skiselev/mb386sx-rc2016/KiCad/AT386SX-Schematic-1.1.pdf

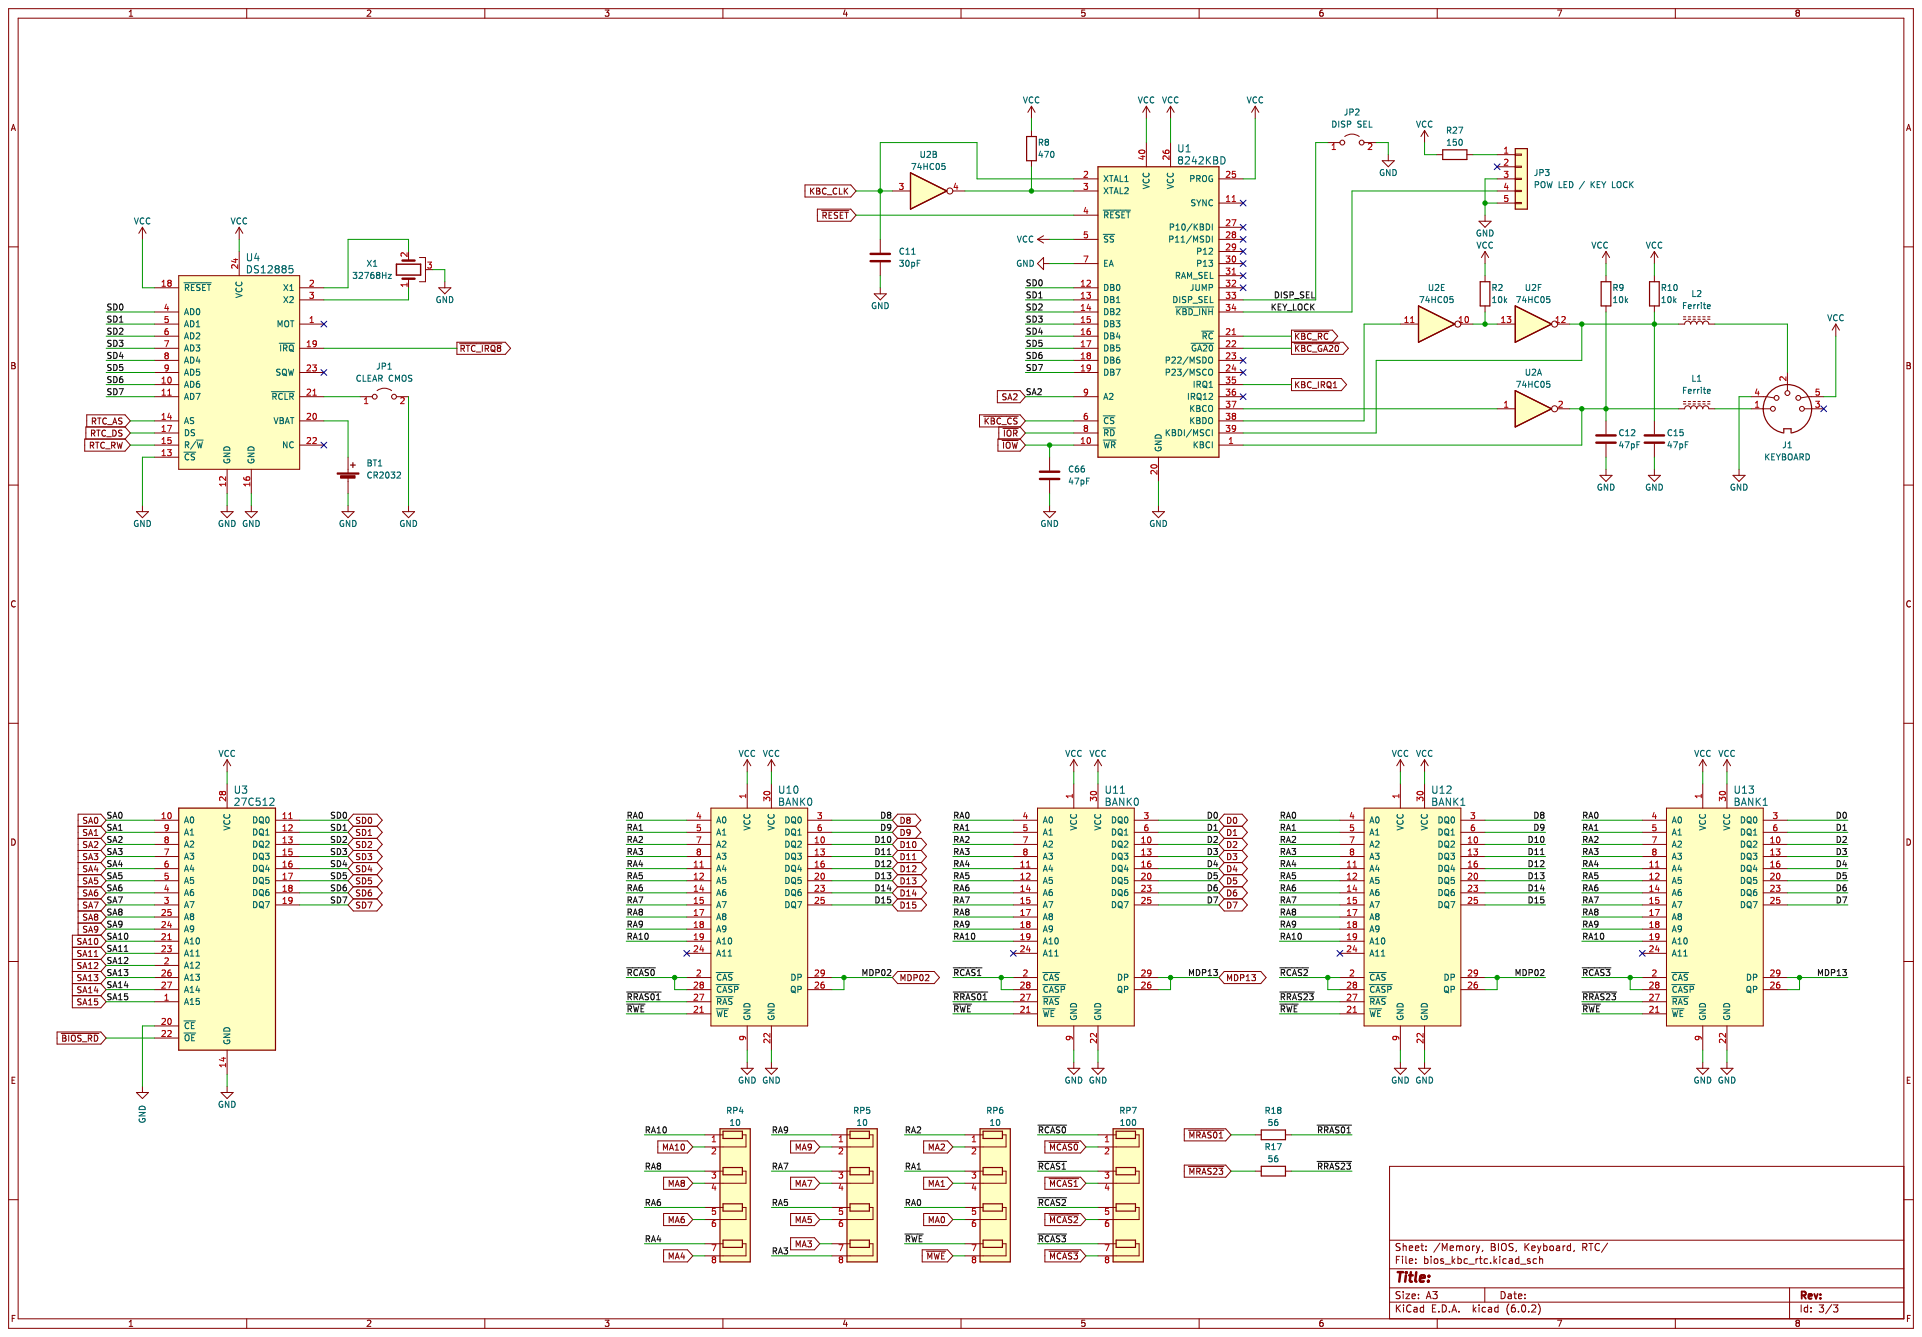
[picture p44: page 3]
