skiselev/mb386sx-rc2016/KiCad/AT386SX-Schematic-1.0.pdf

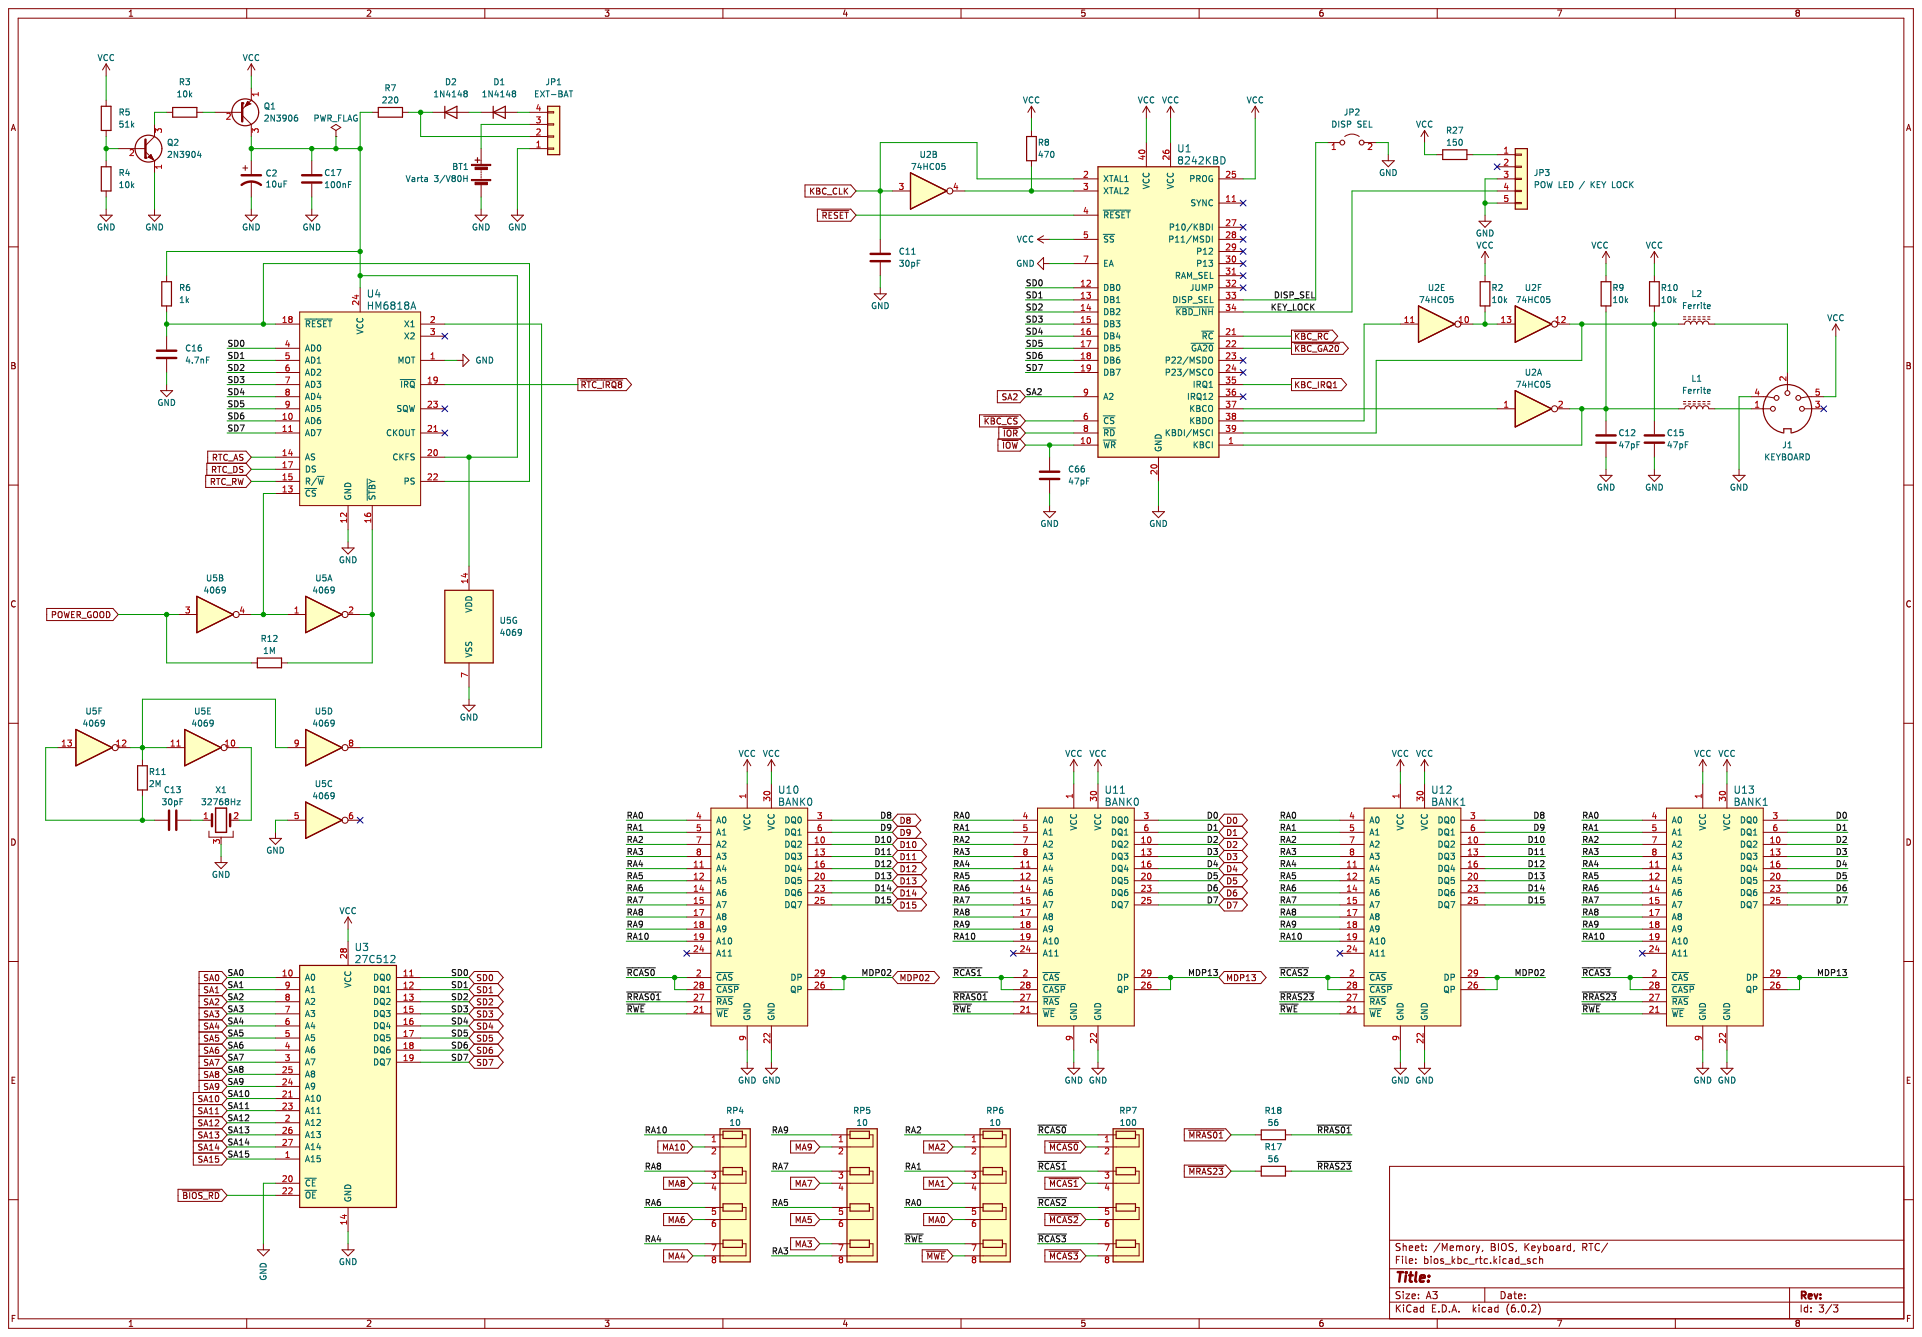
[picture p45: page 3]
