skiselev/mb386sx-rc2016/KiCad/AT386SX-Board-2.3.pdf

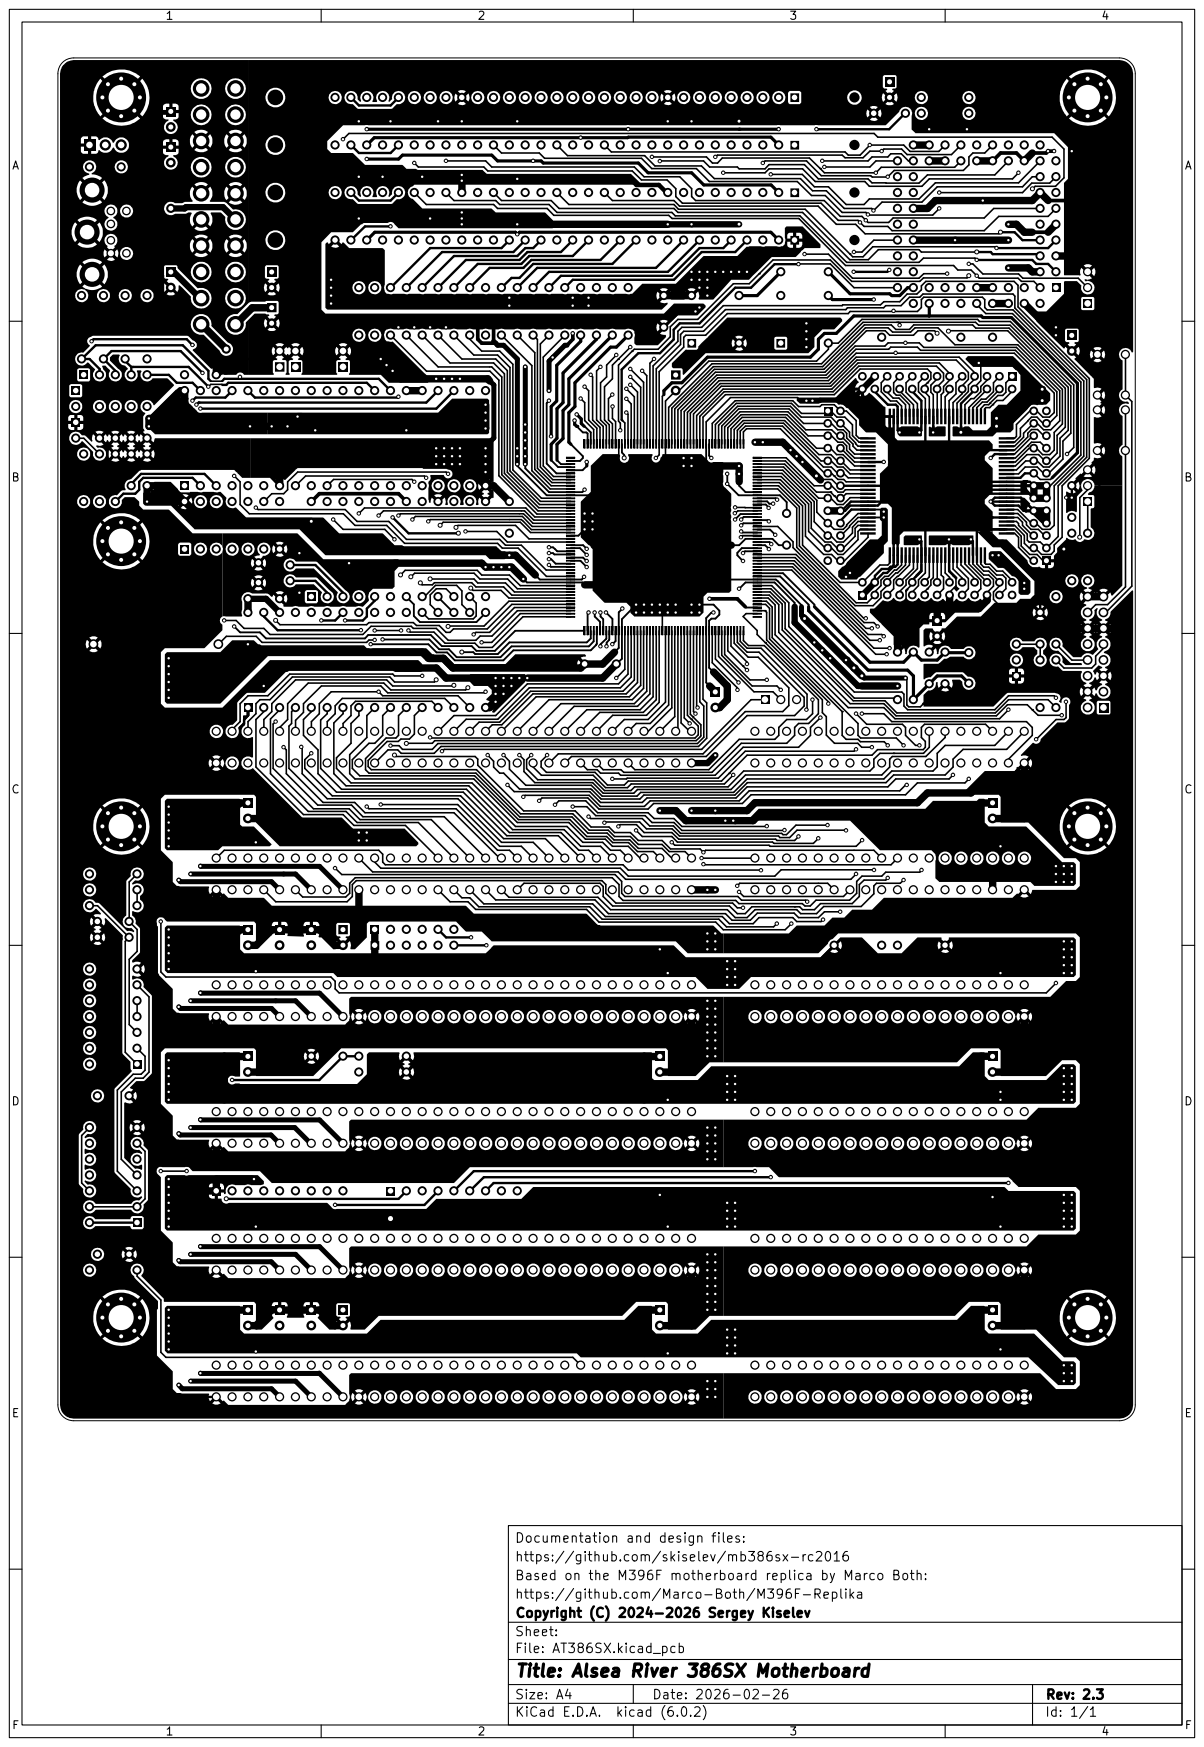
[picture p46: page 1]

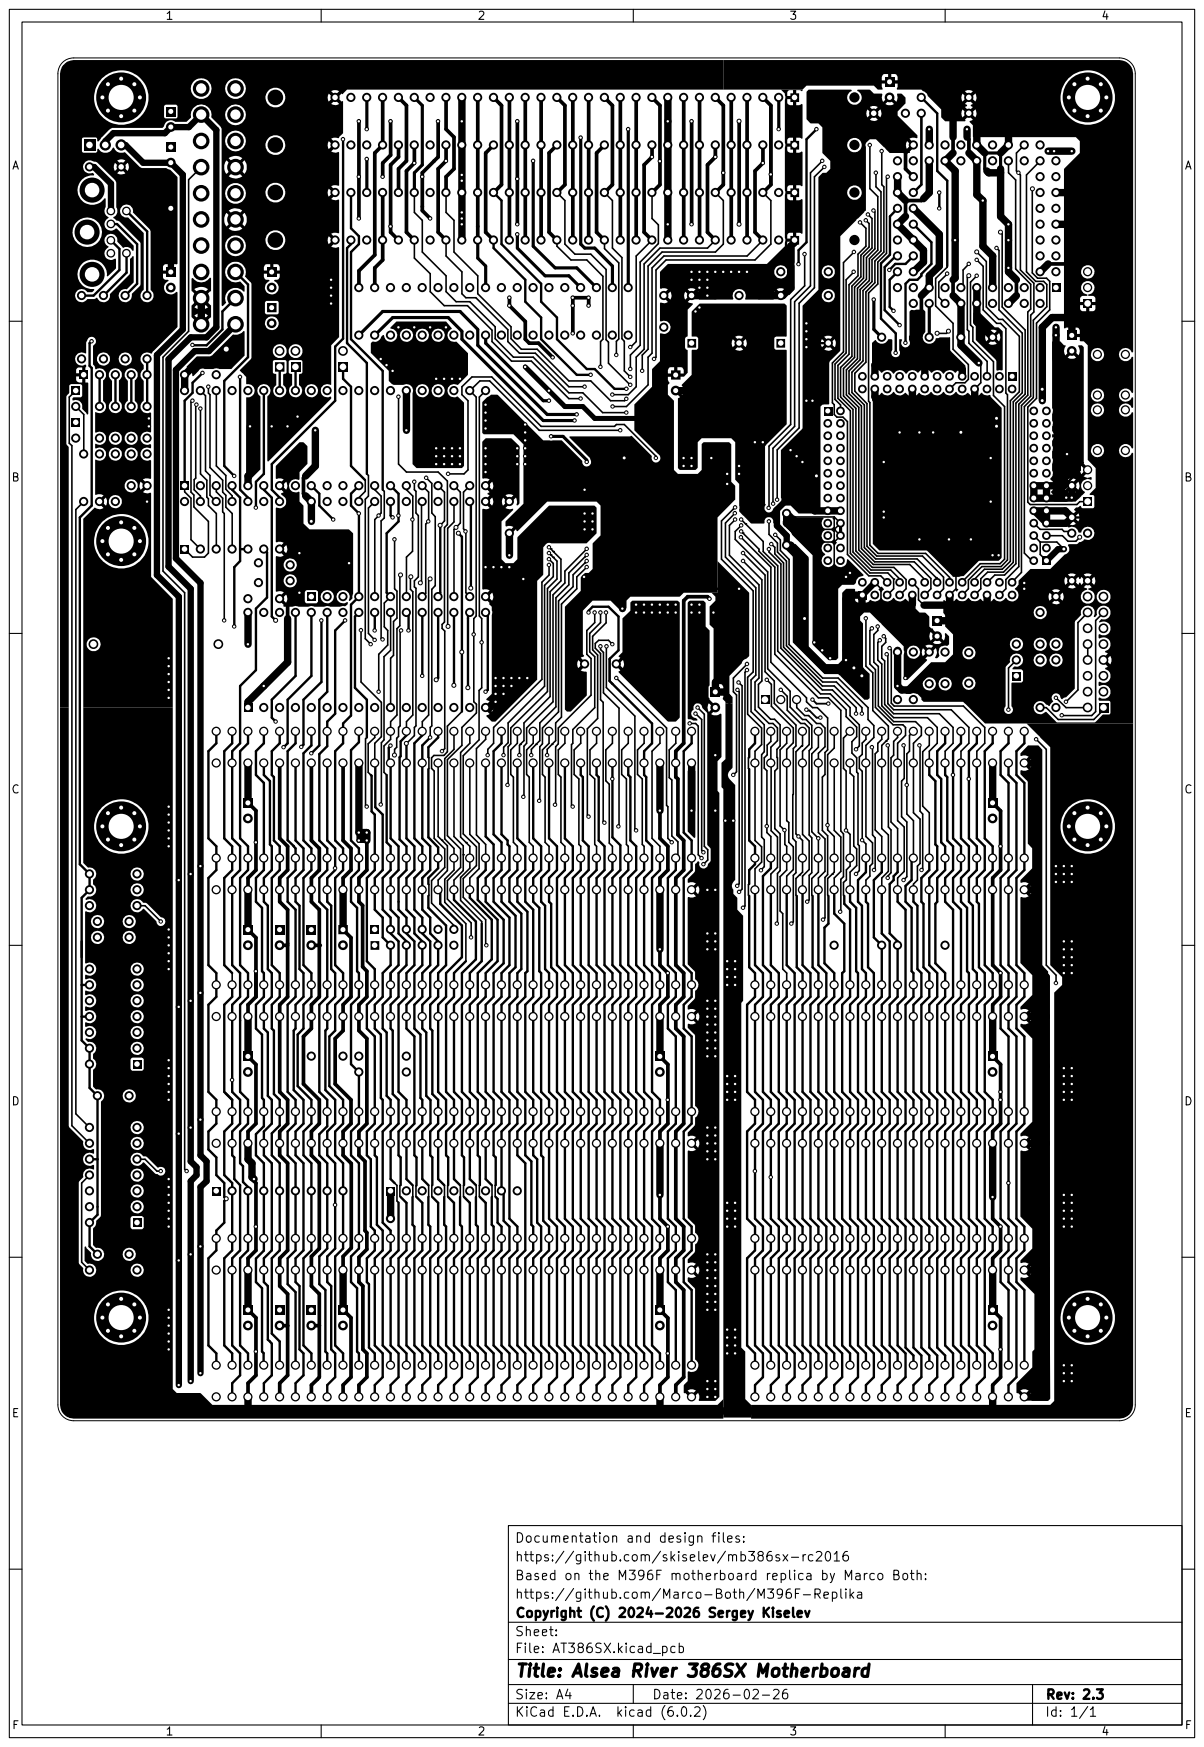
[picture p47: page 2]

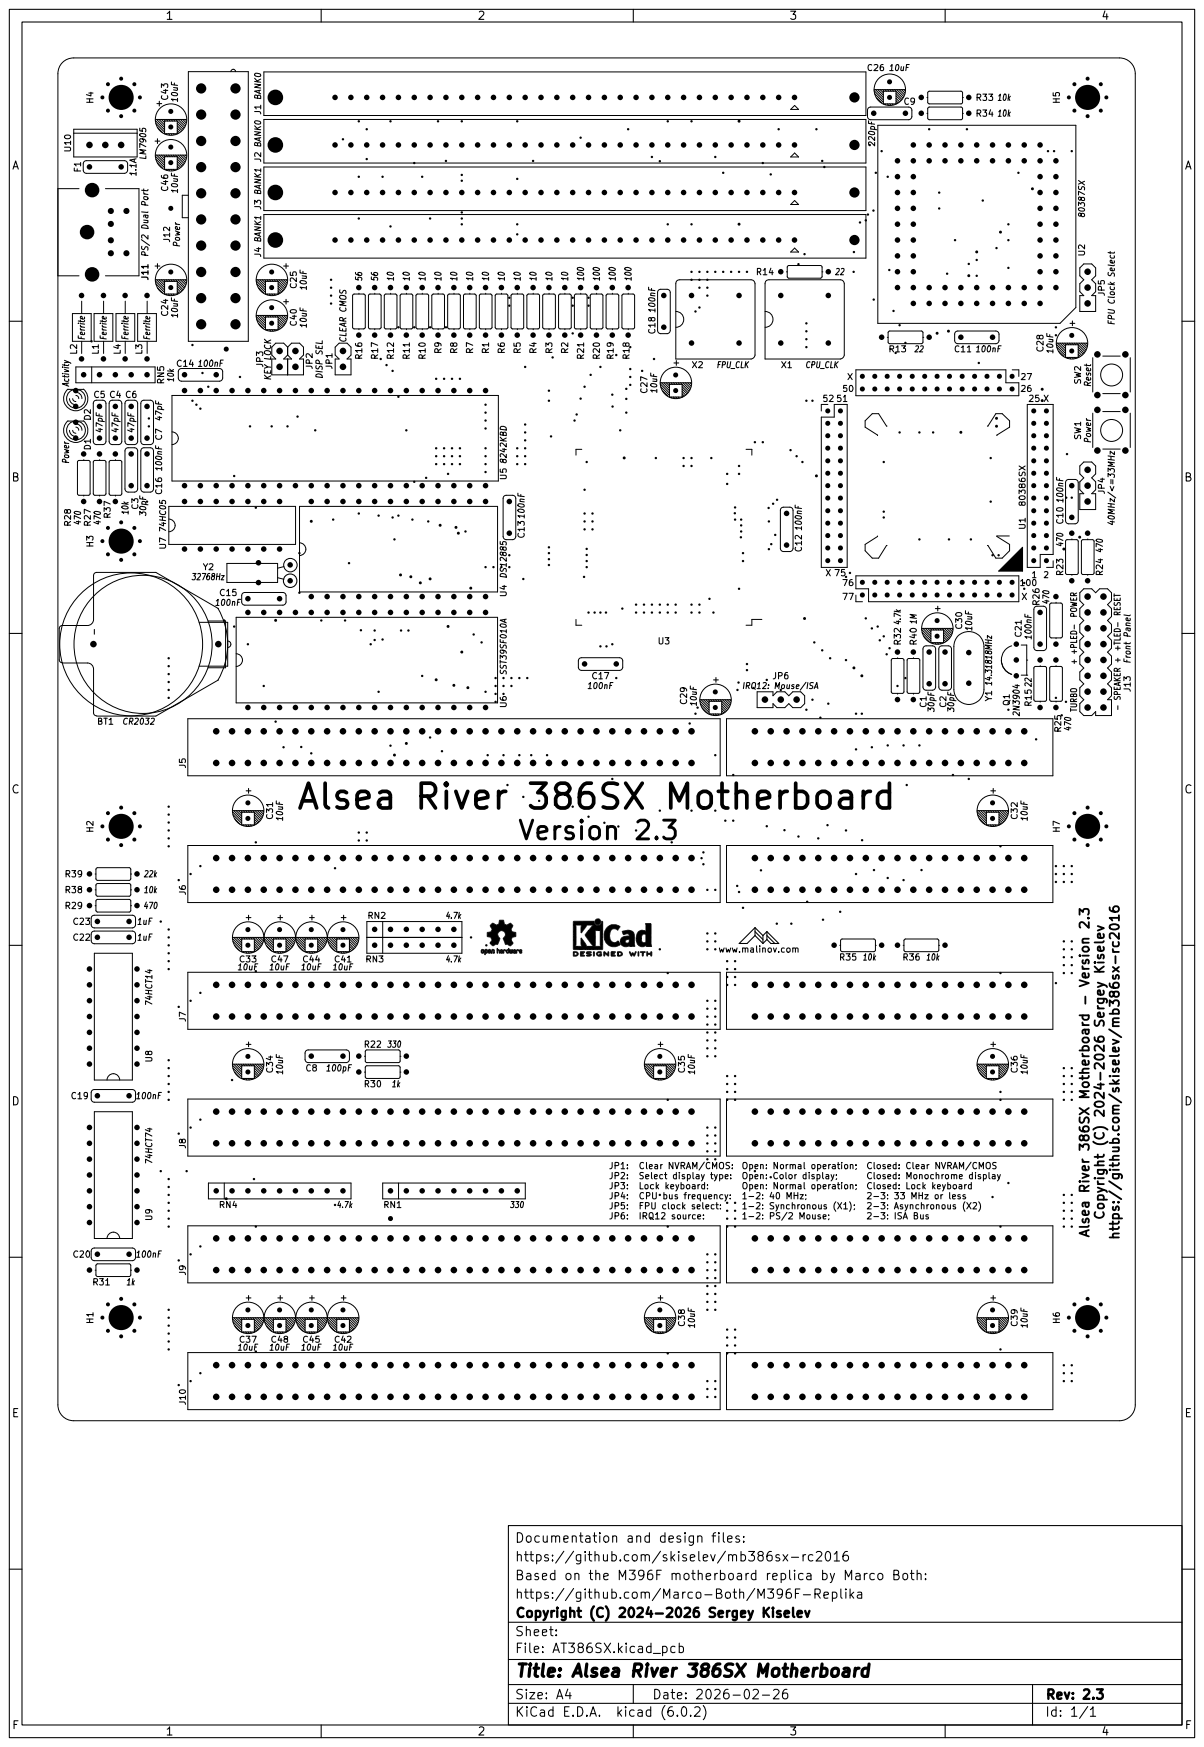
[picture p48: page 3]

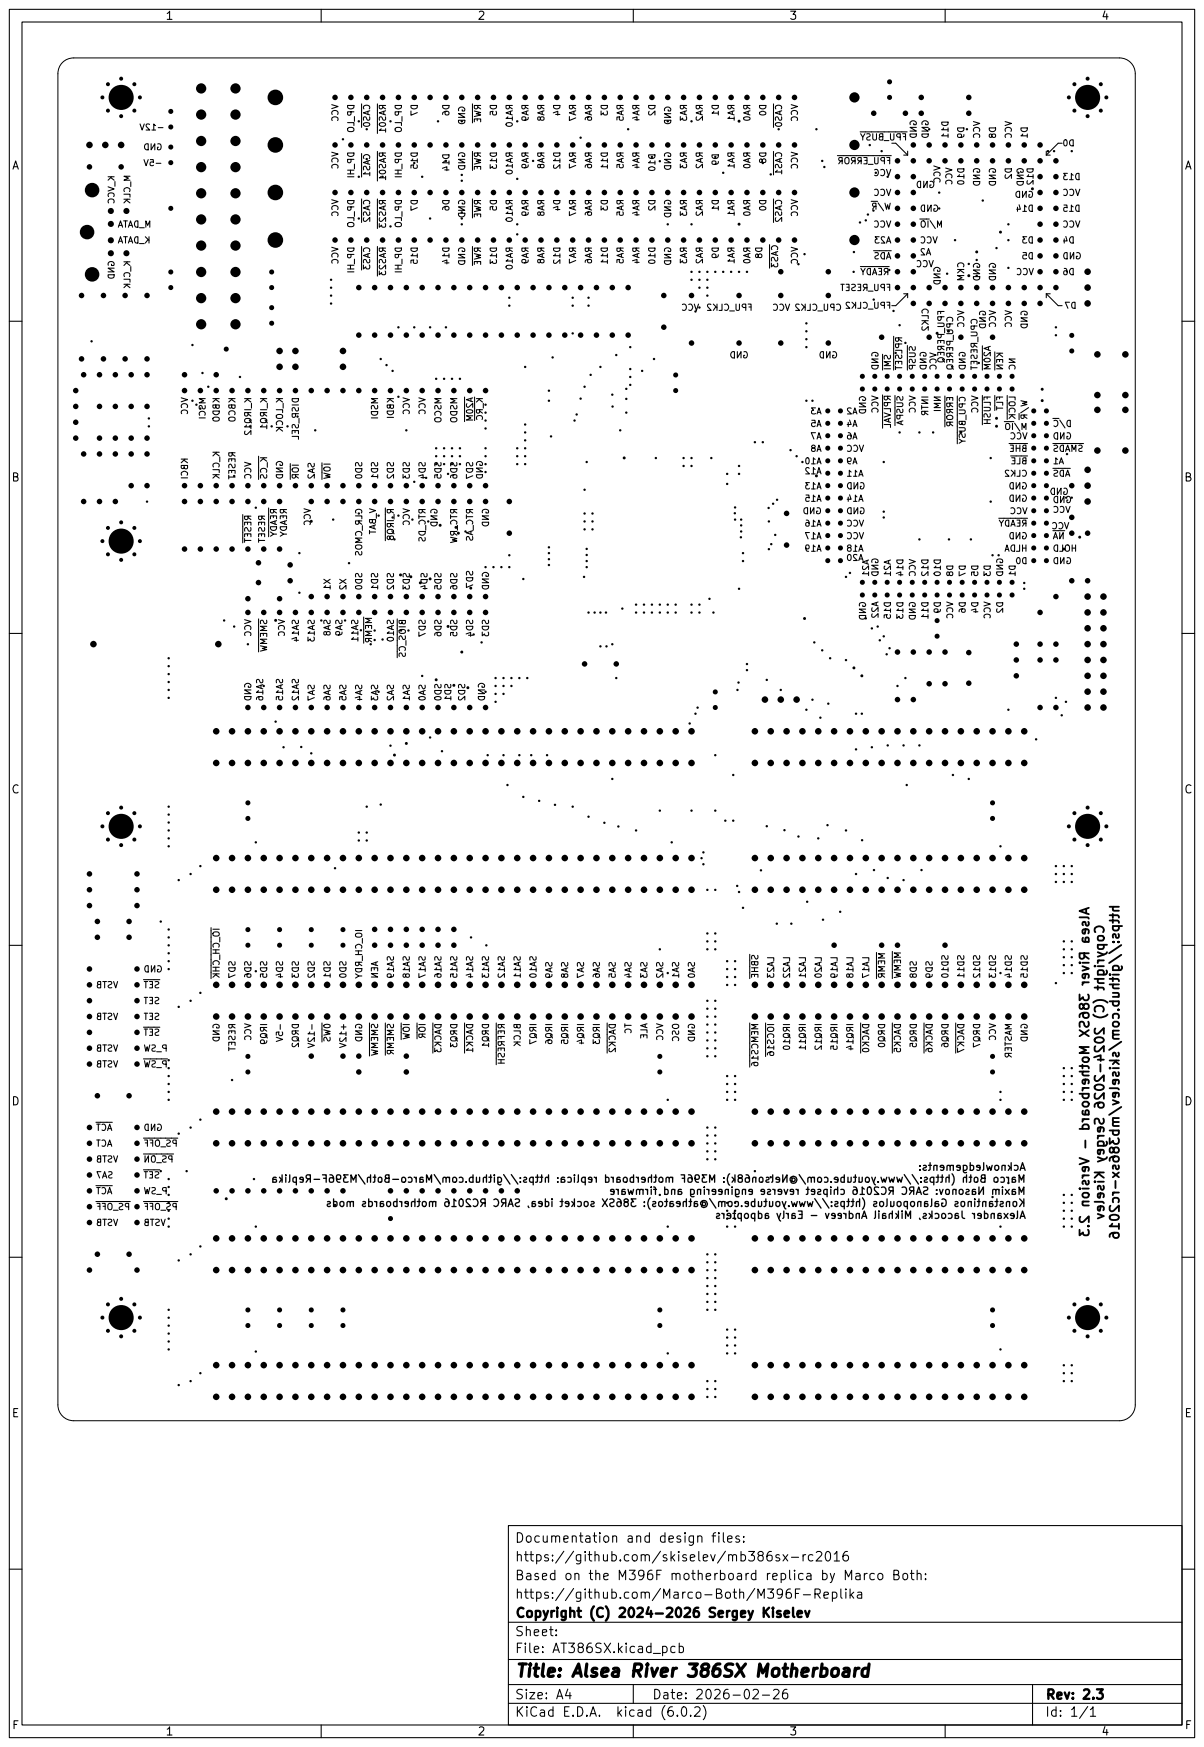
[picture p49: page 4]
