skiselev/mb386sx-rc2016/KiCad/AT386SX-Board-2.2.pdf

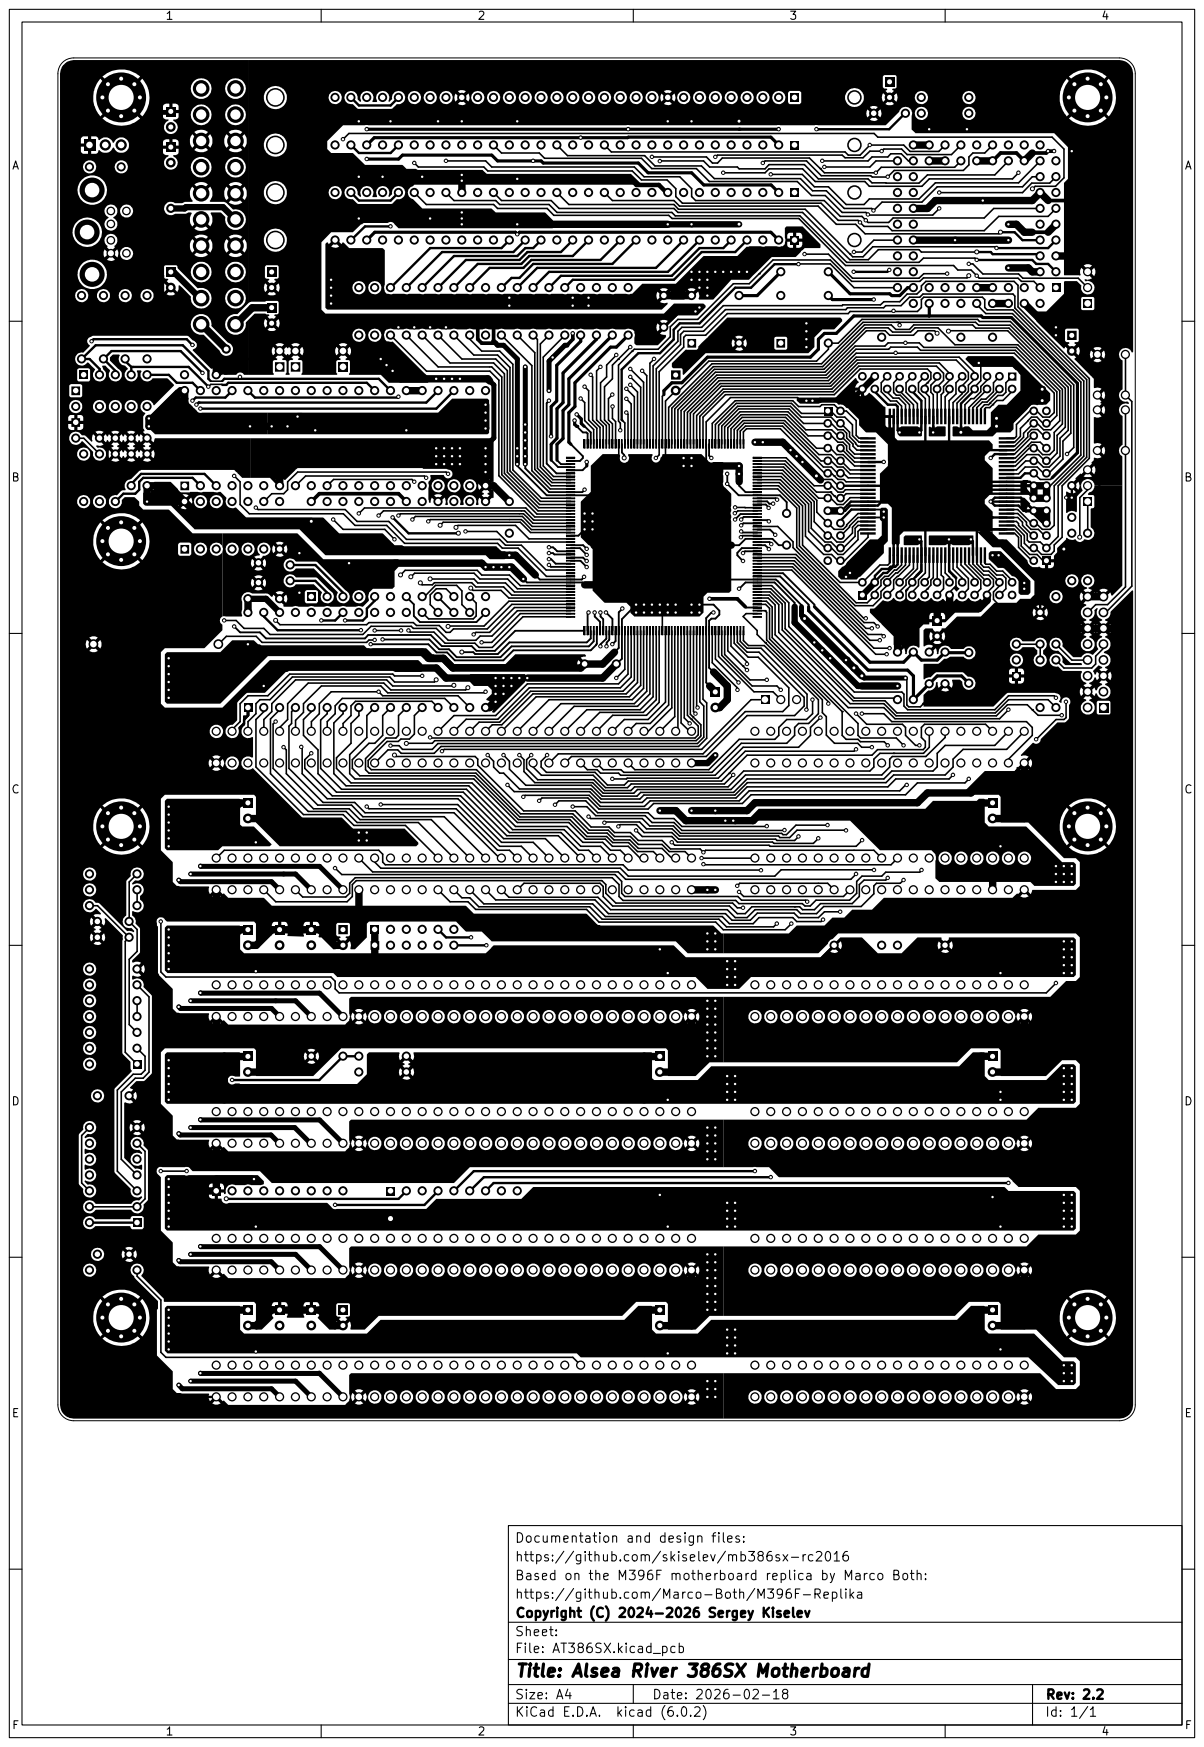
[picture p50: page 1]

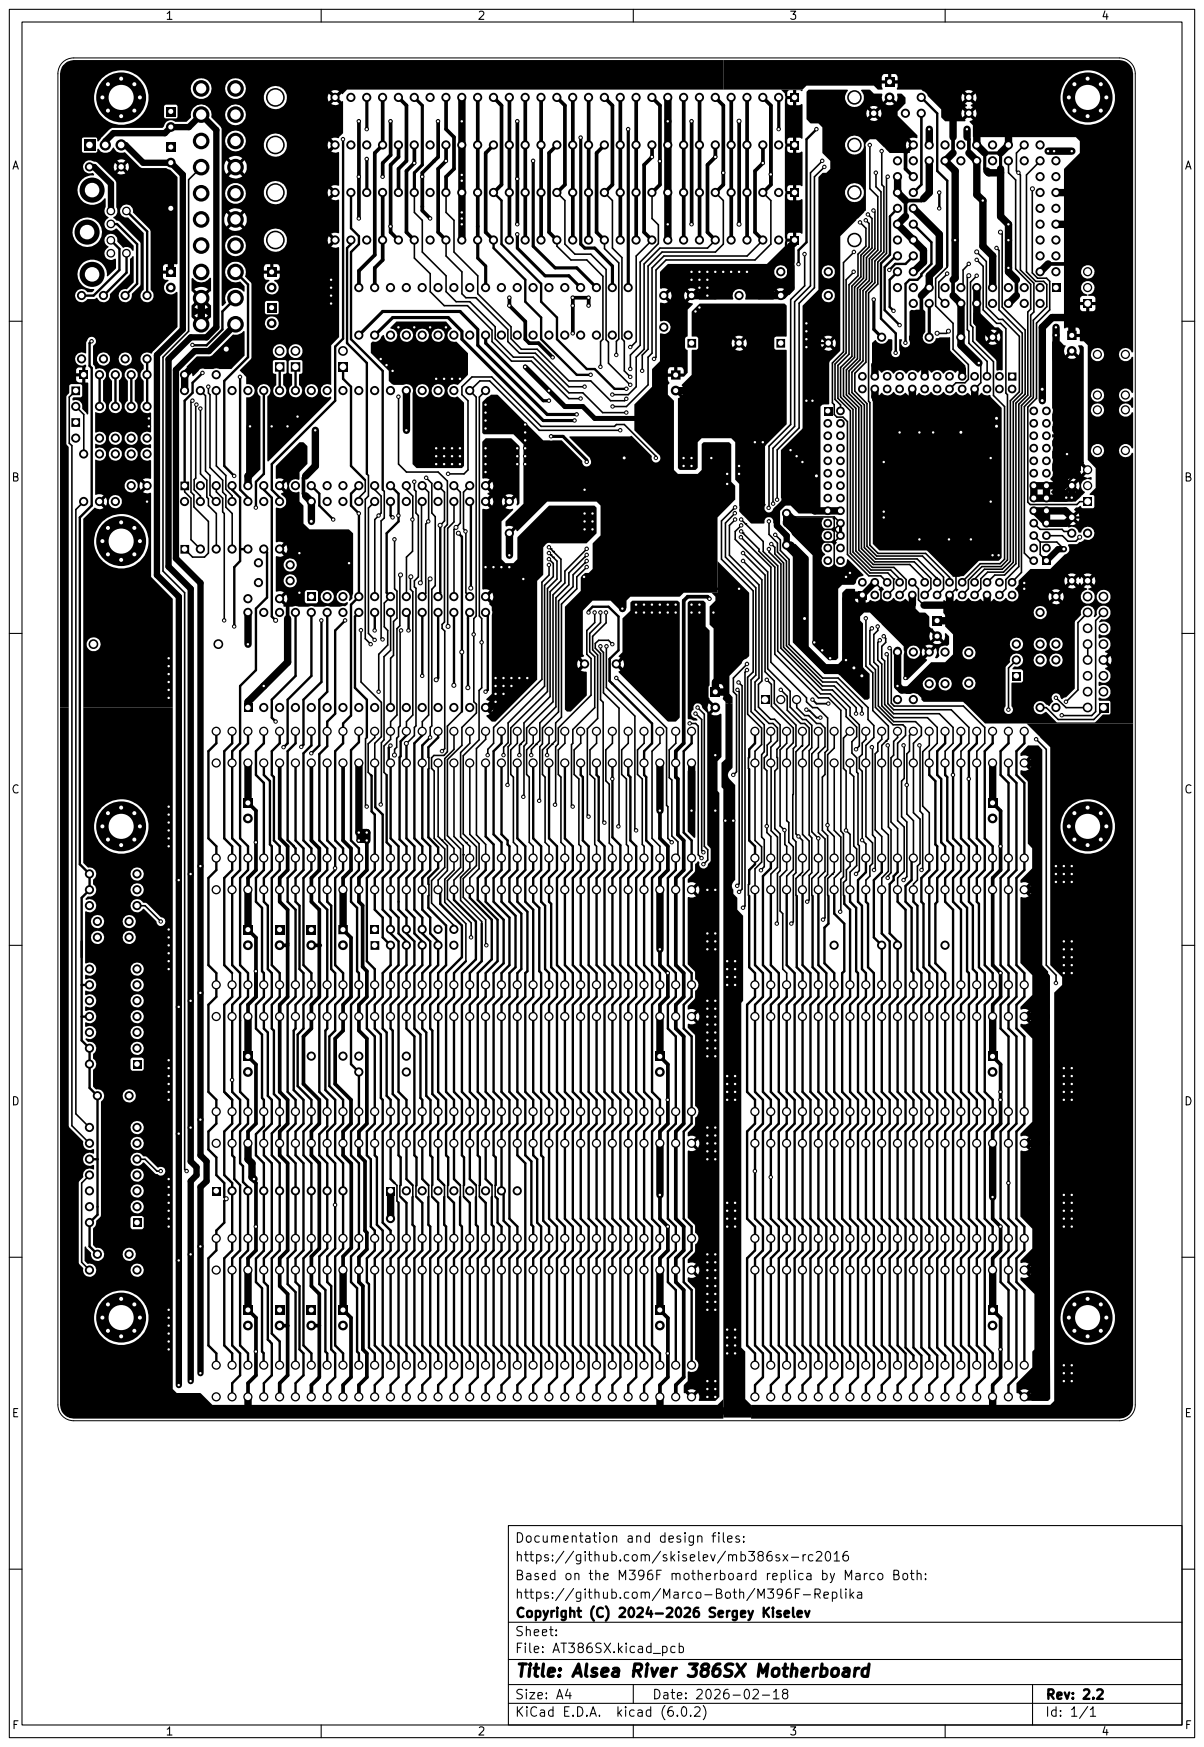
[picture p51: page 2]

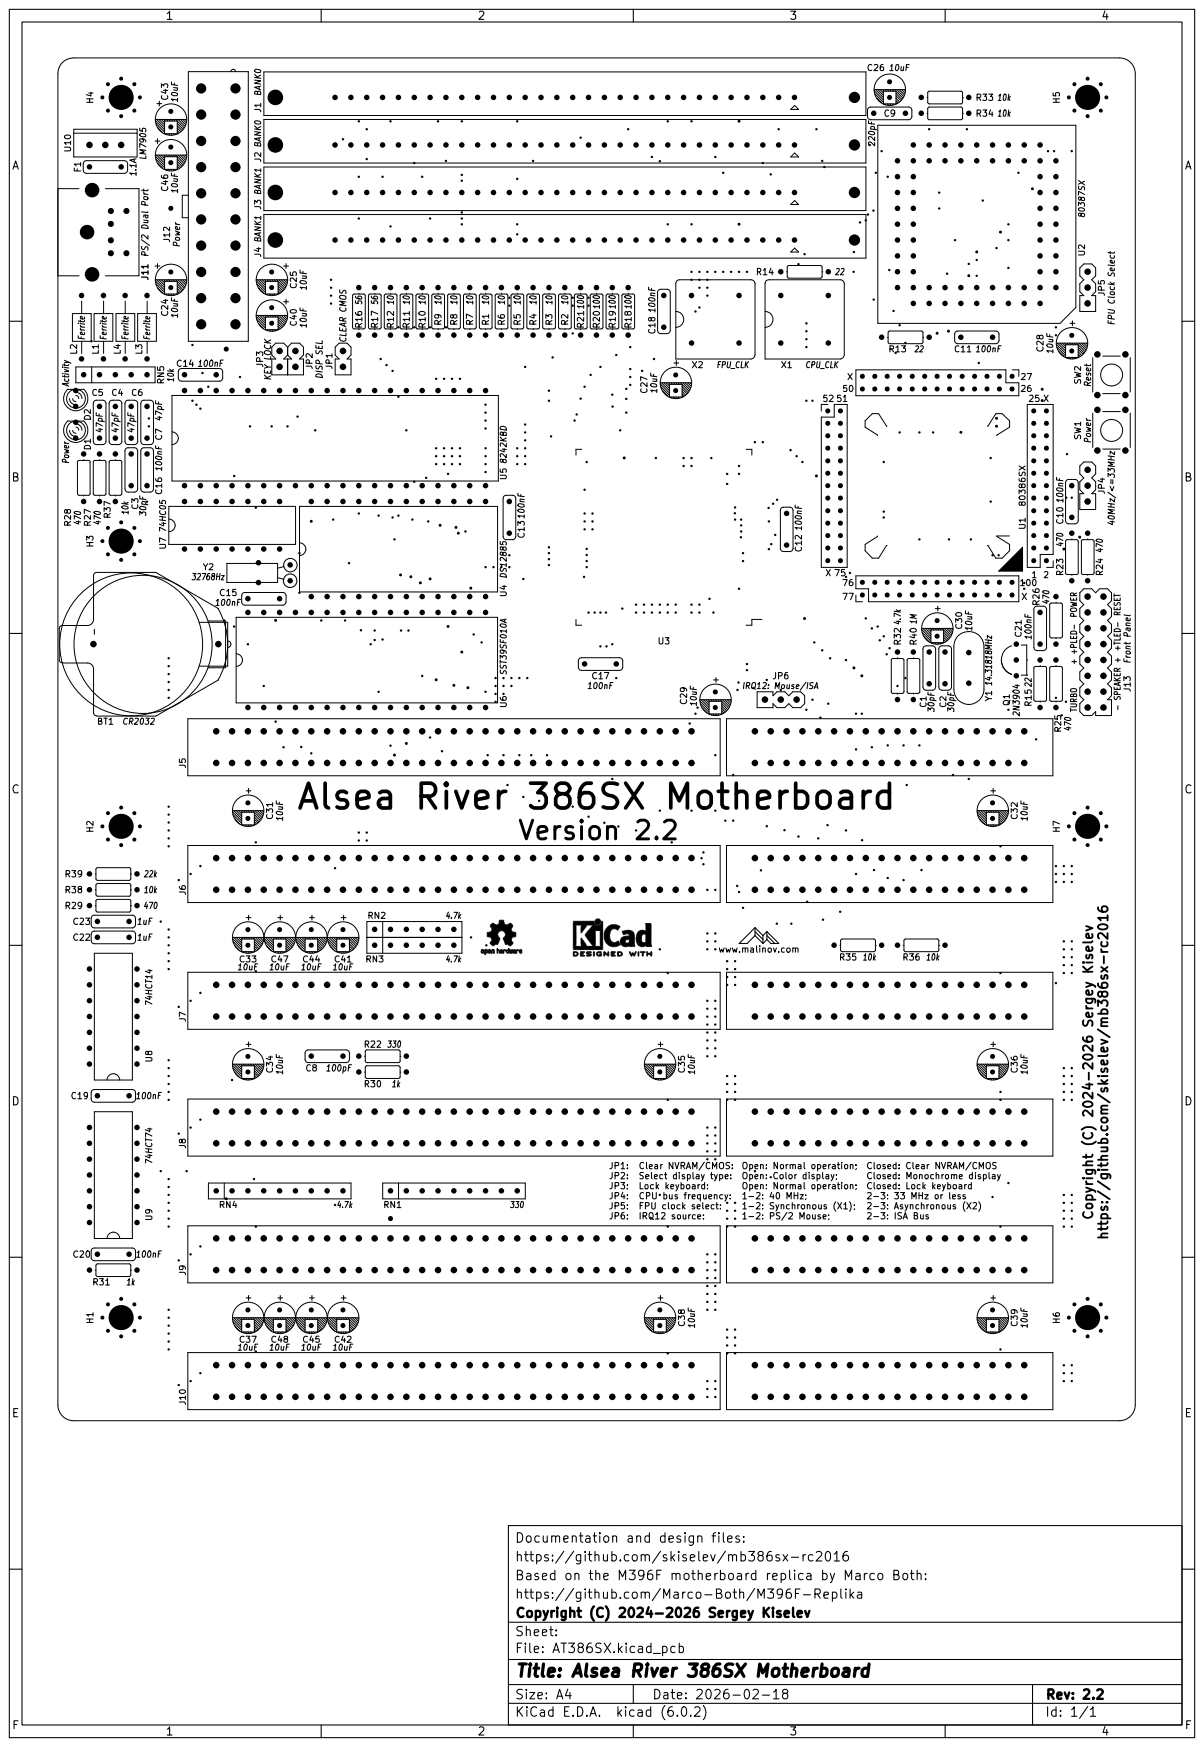
[picture p52: page 3]

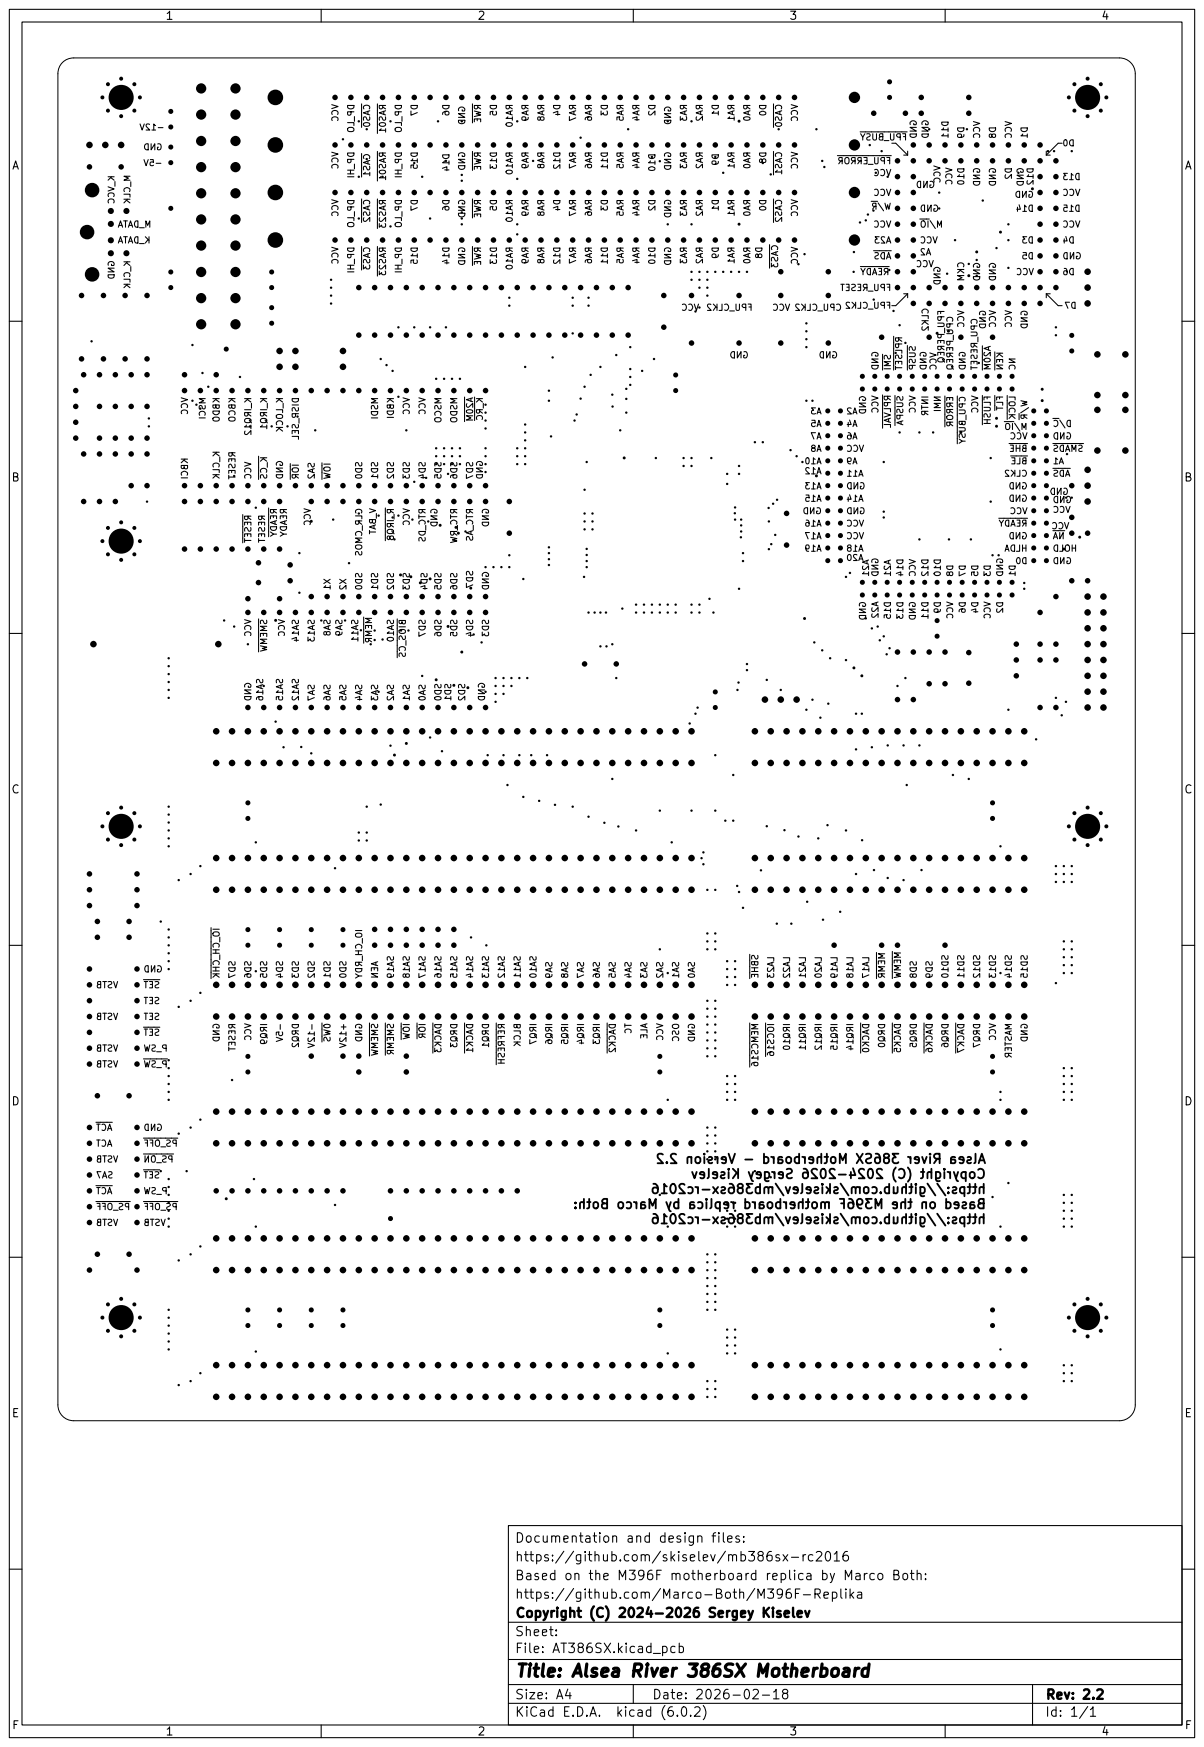
[picture p53: page 4]
