skiselev/mb386sx-rc2016/KiCad/AT386SX-Board-2.1.pdf

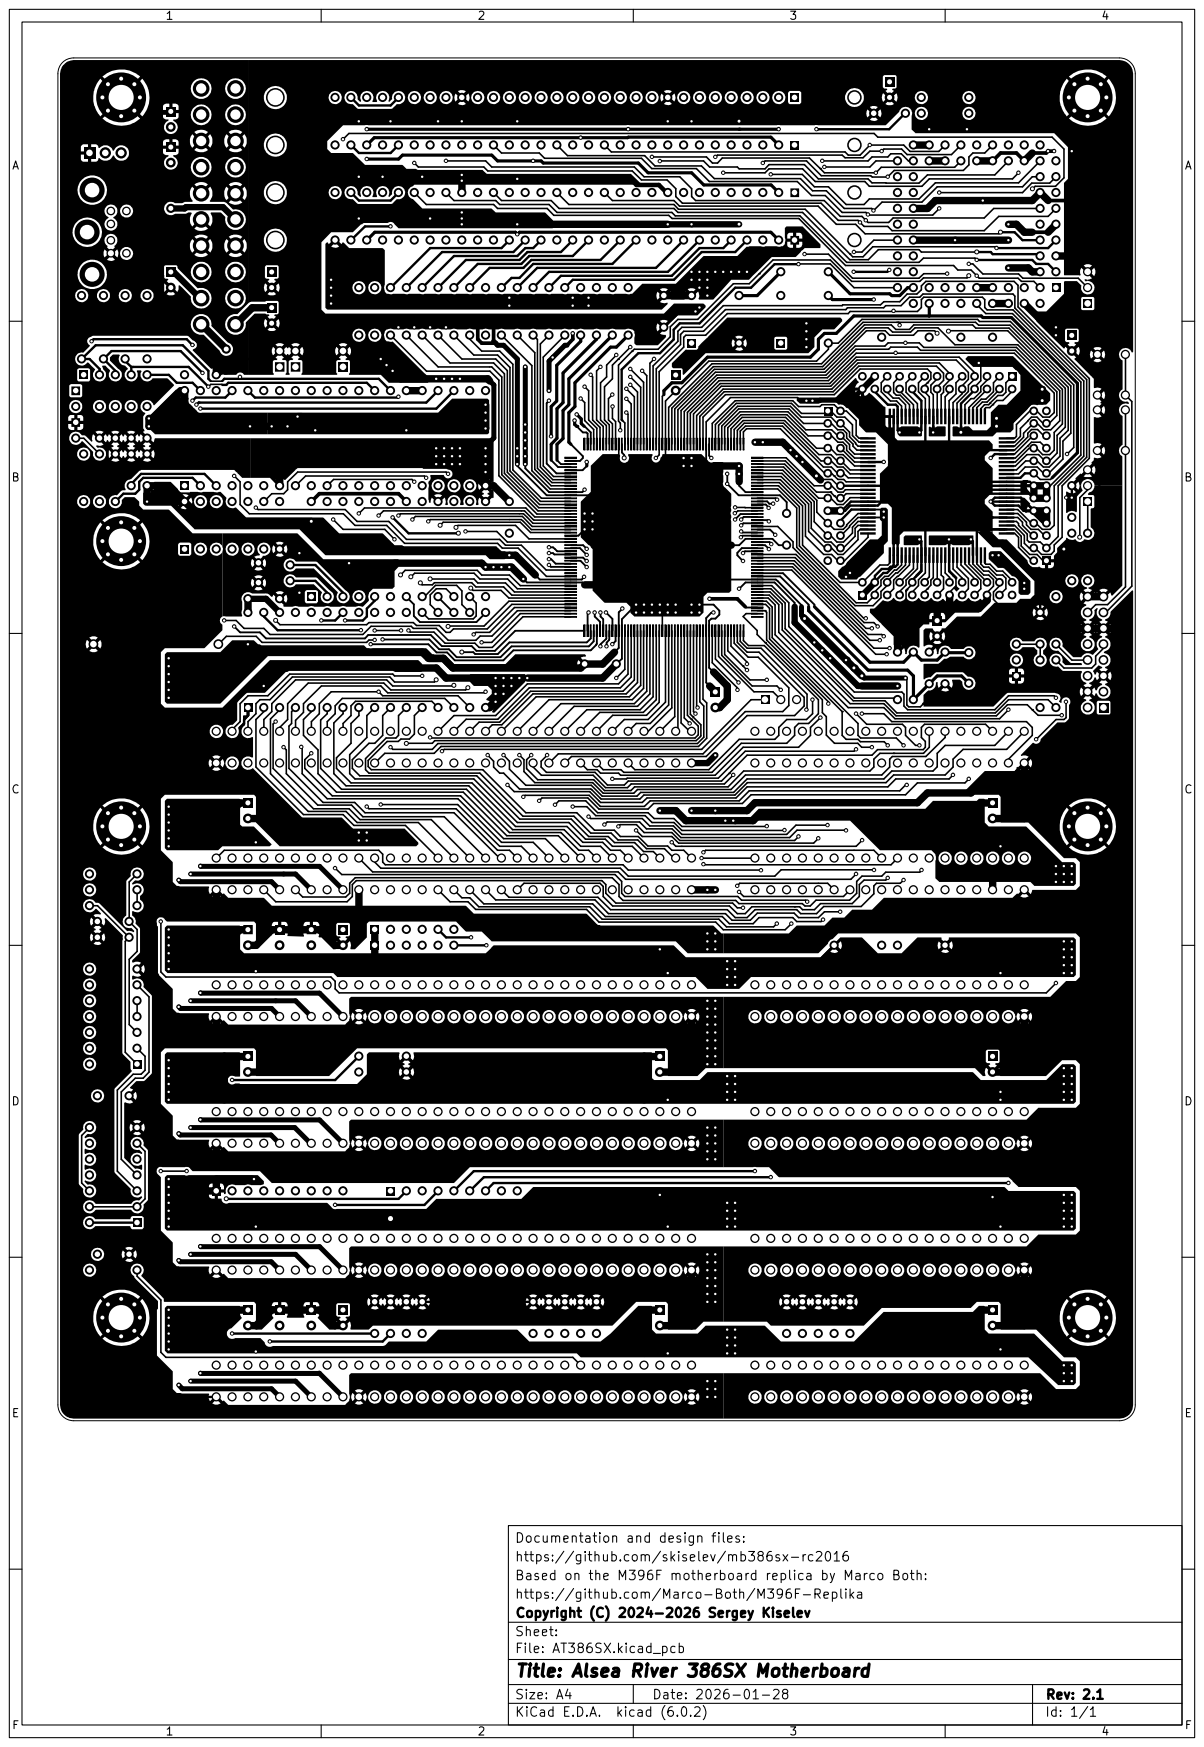
[picture p54: page 1]

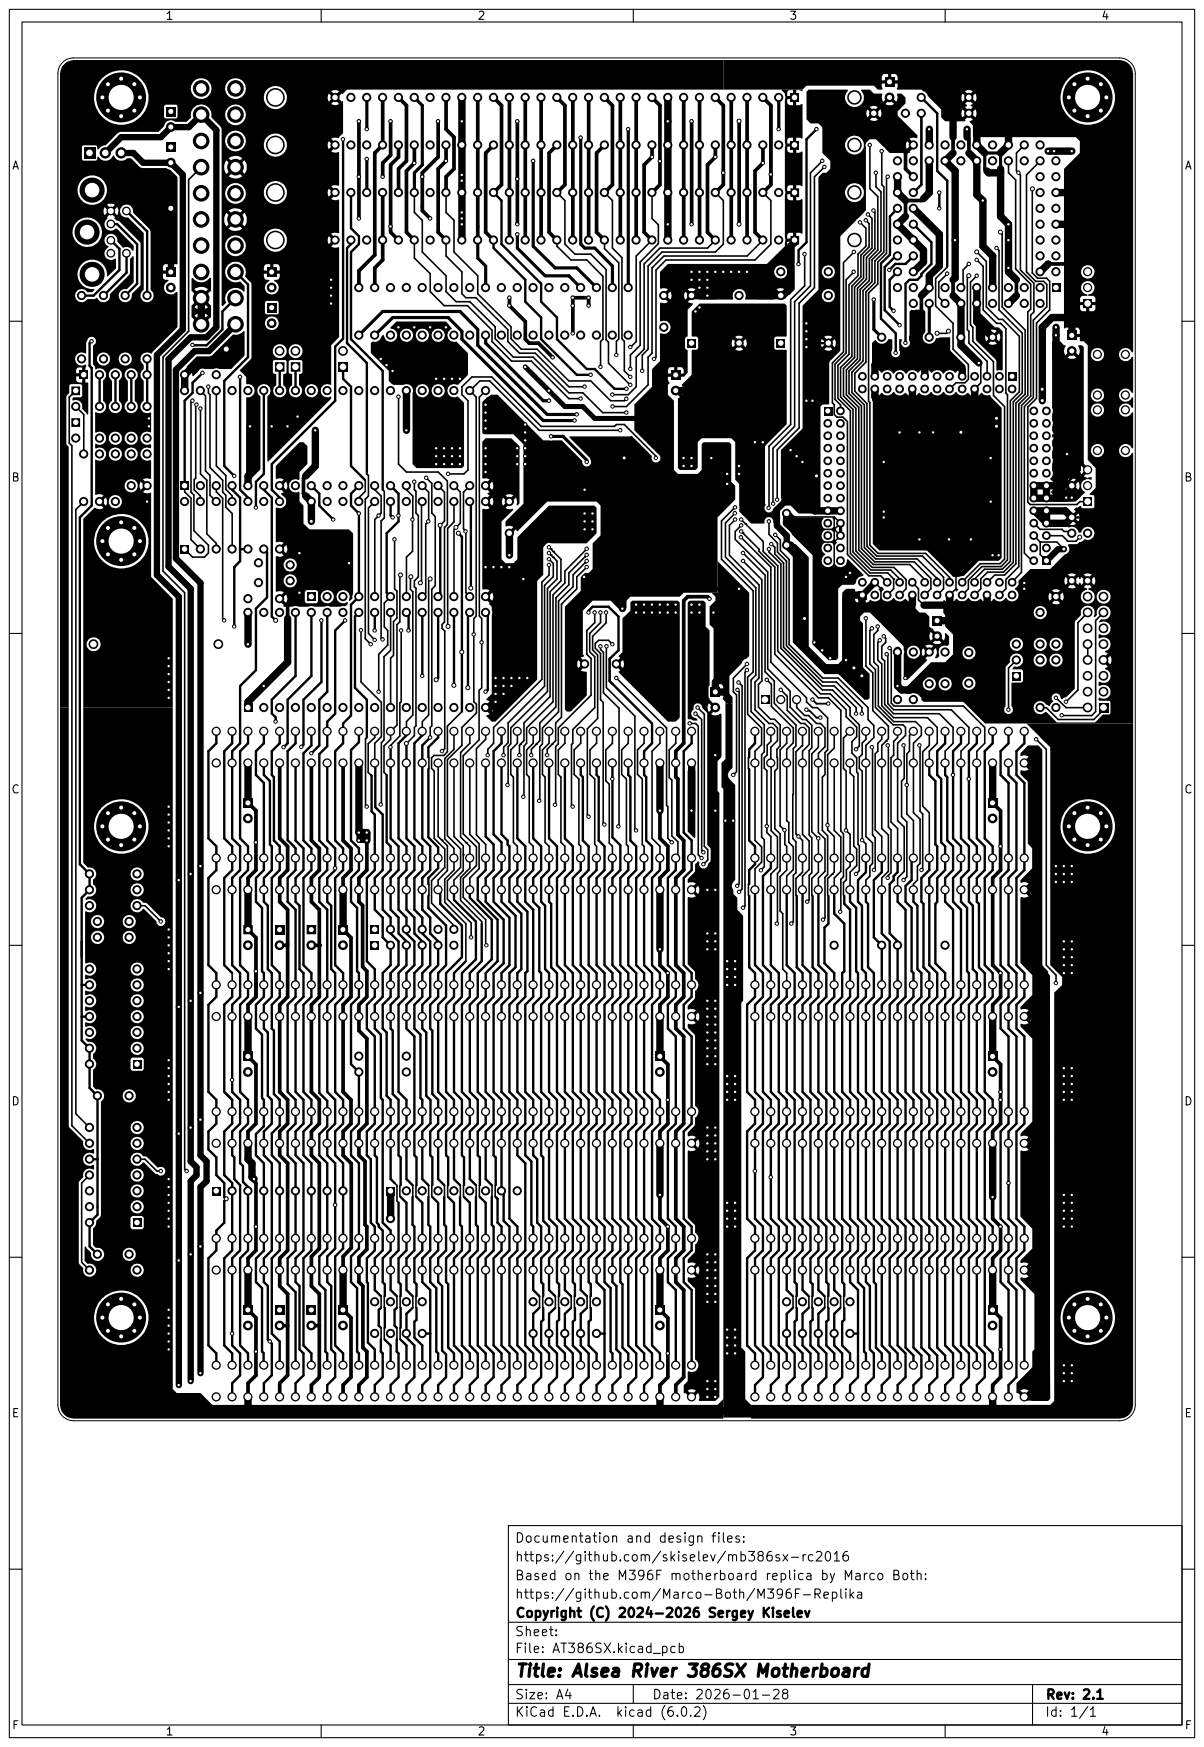
[picture p55: page 2]

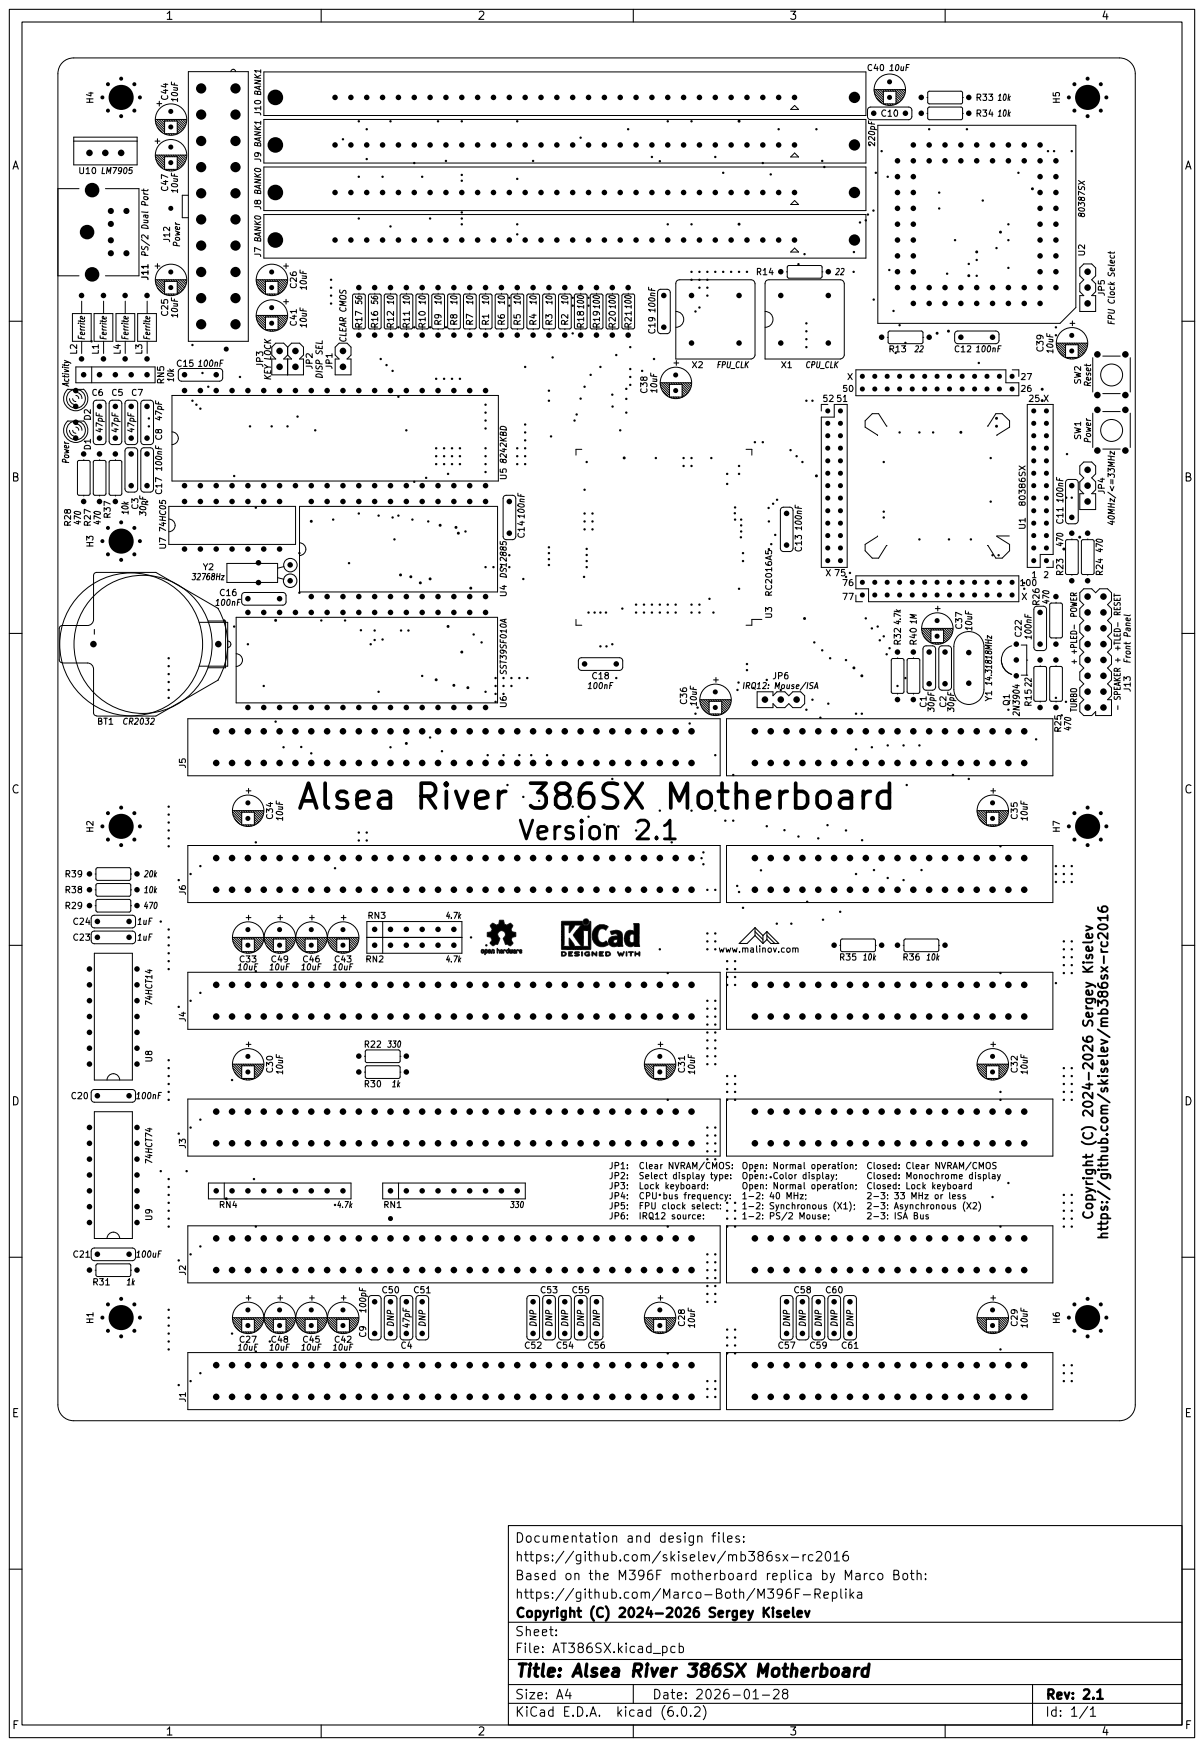
[picture p56: page 3]

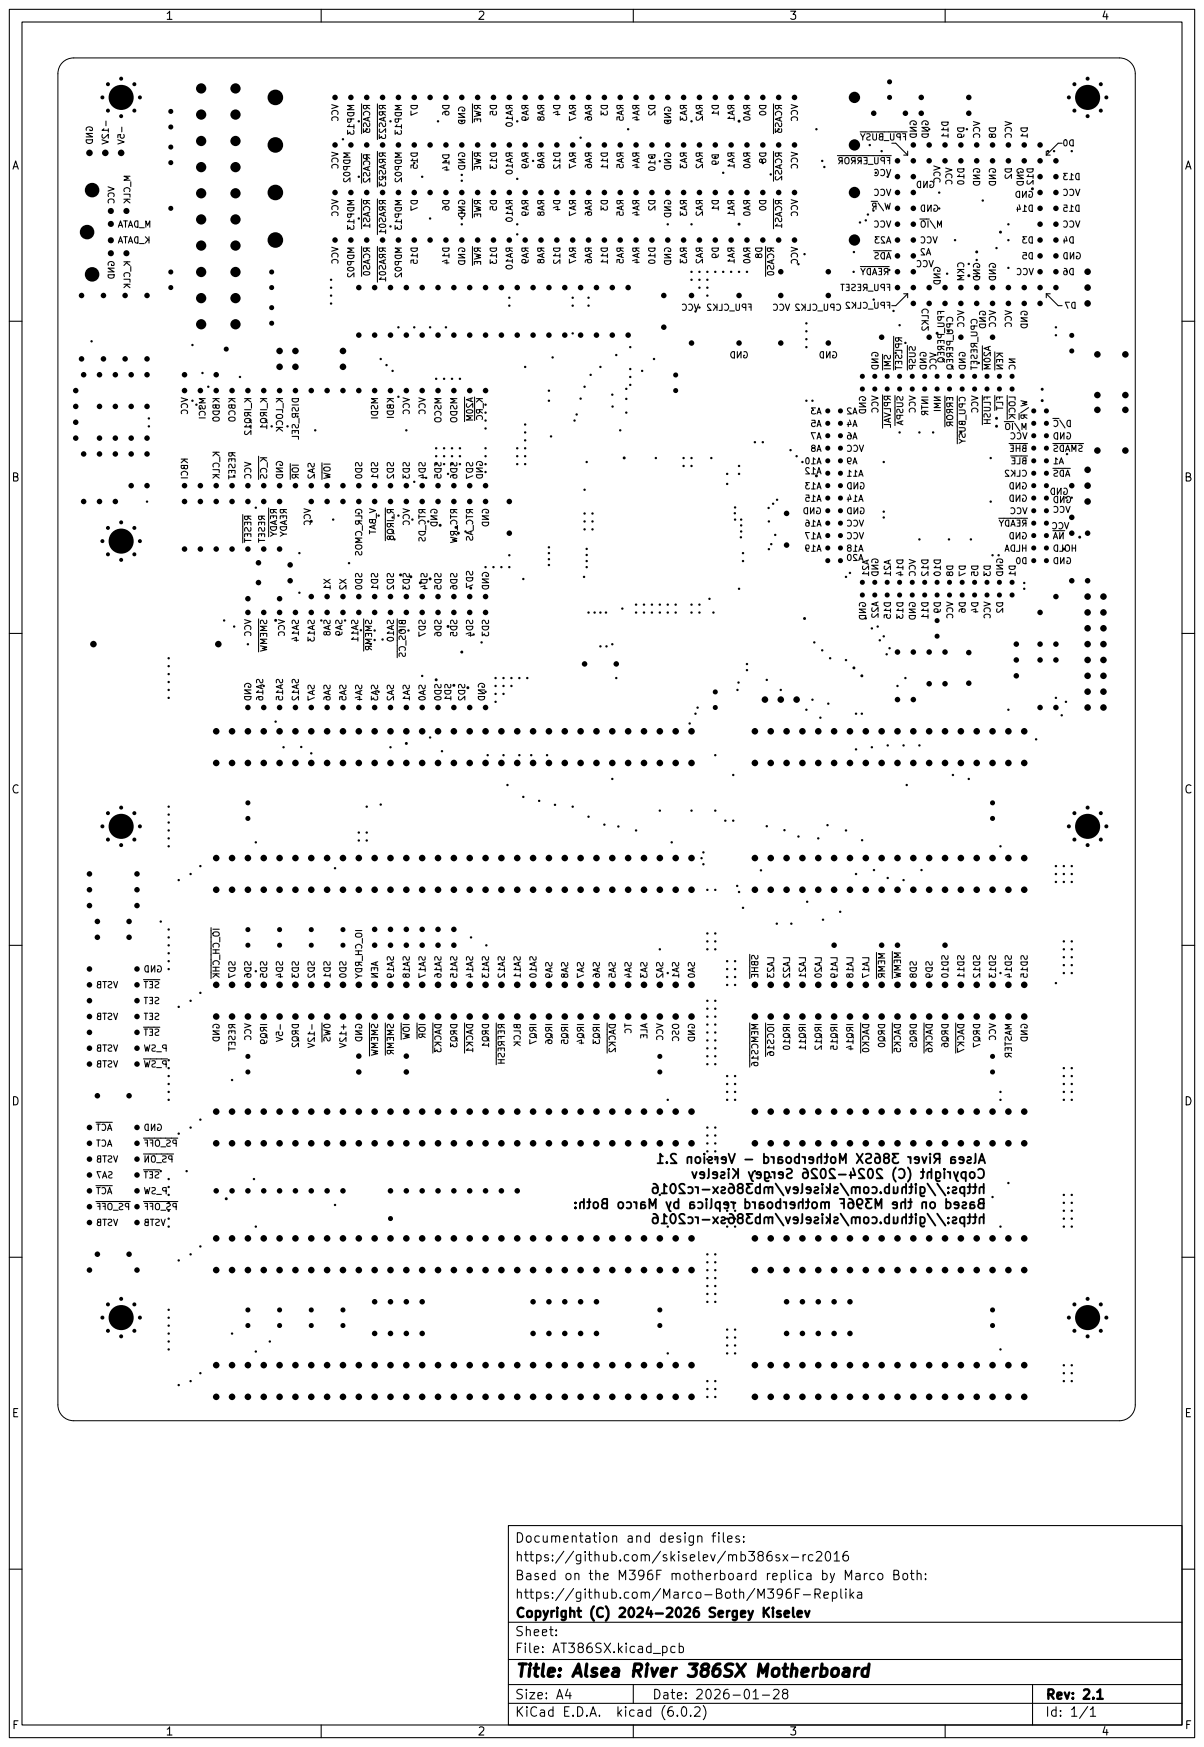
[picture p57: page 4]
