skiselev/mb386sx-rc2016/KiCad/AT386SX-Board-2.0.pdf

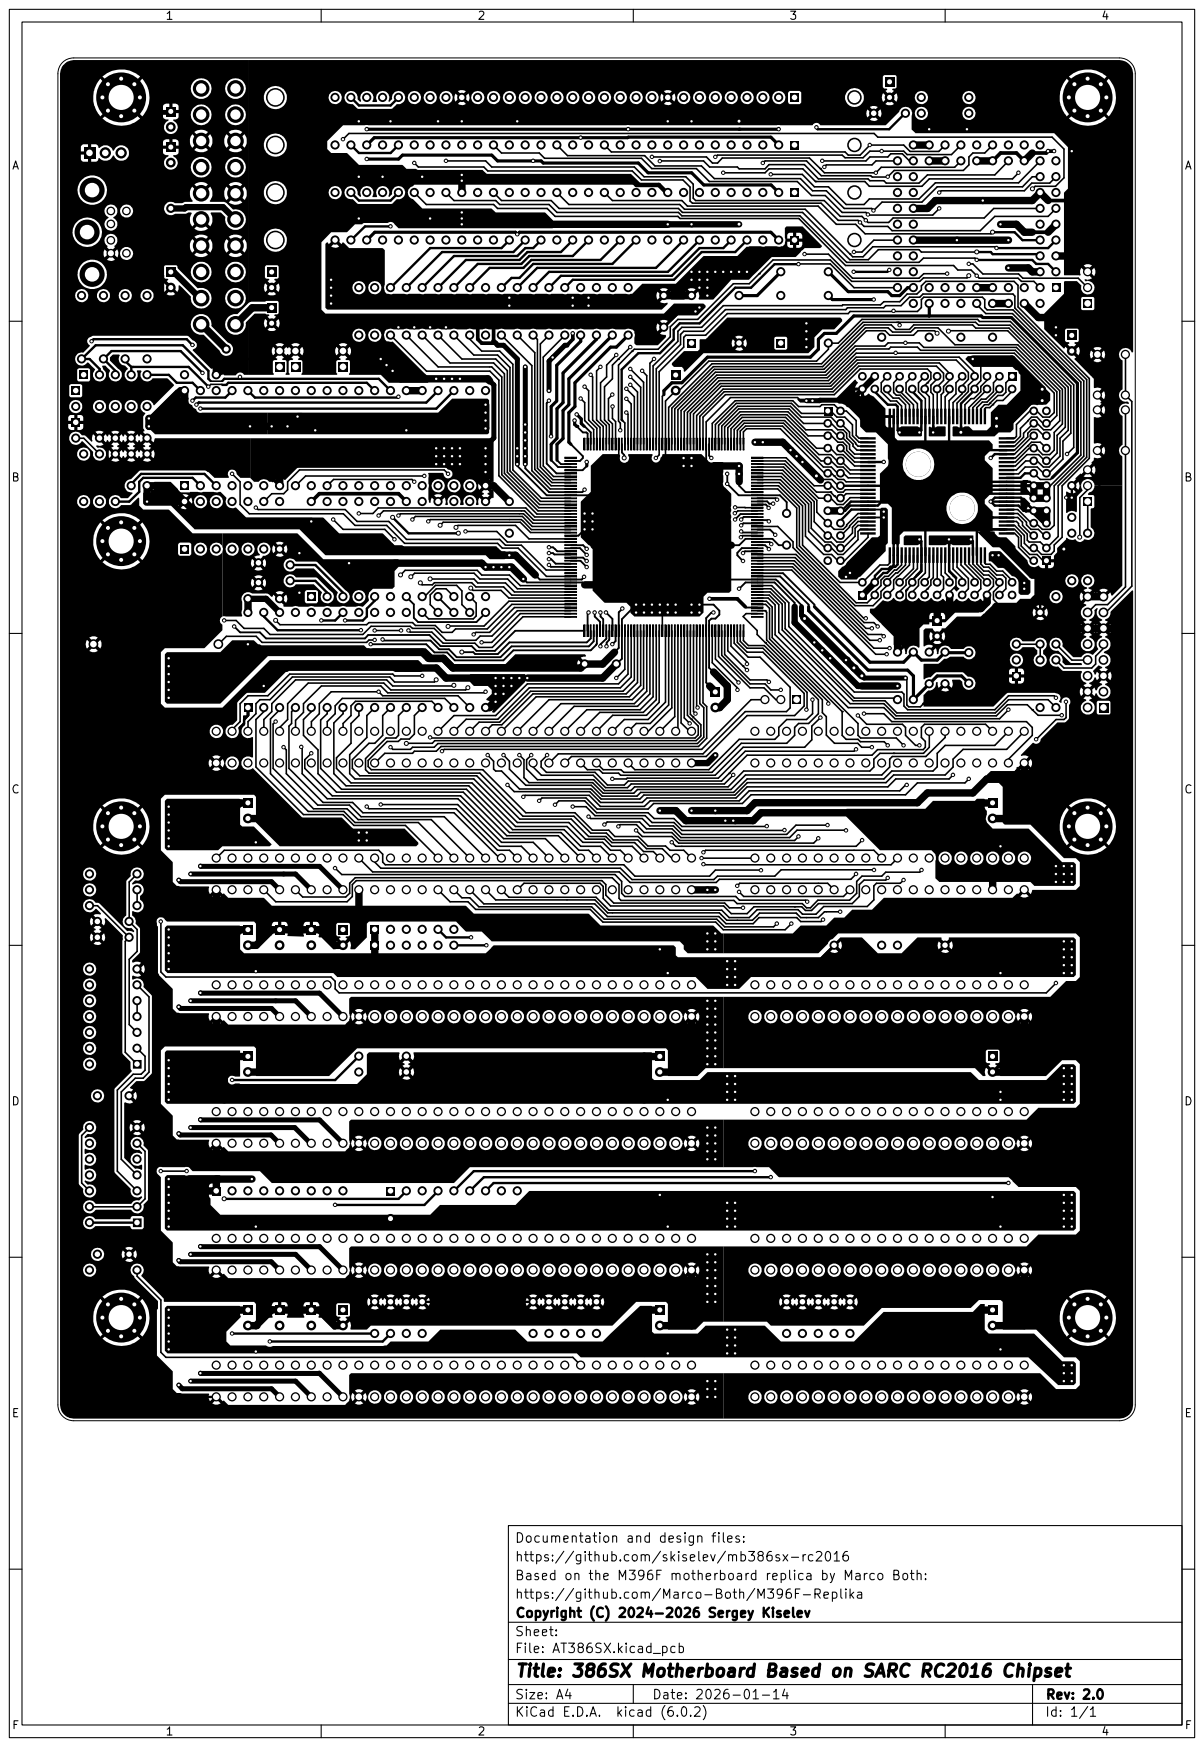
[picture p58: page 1]

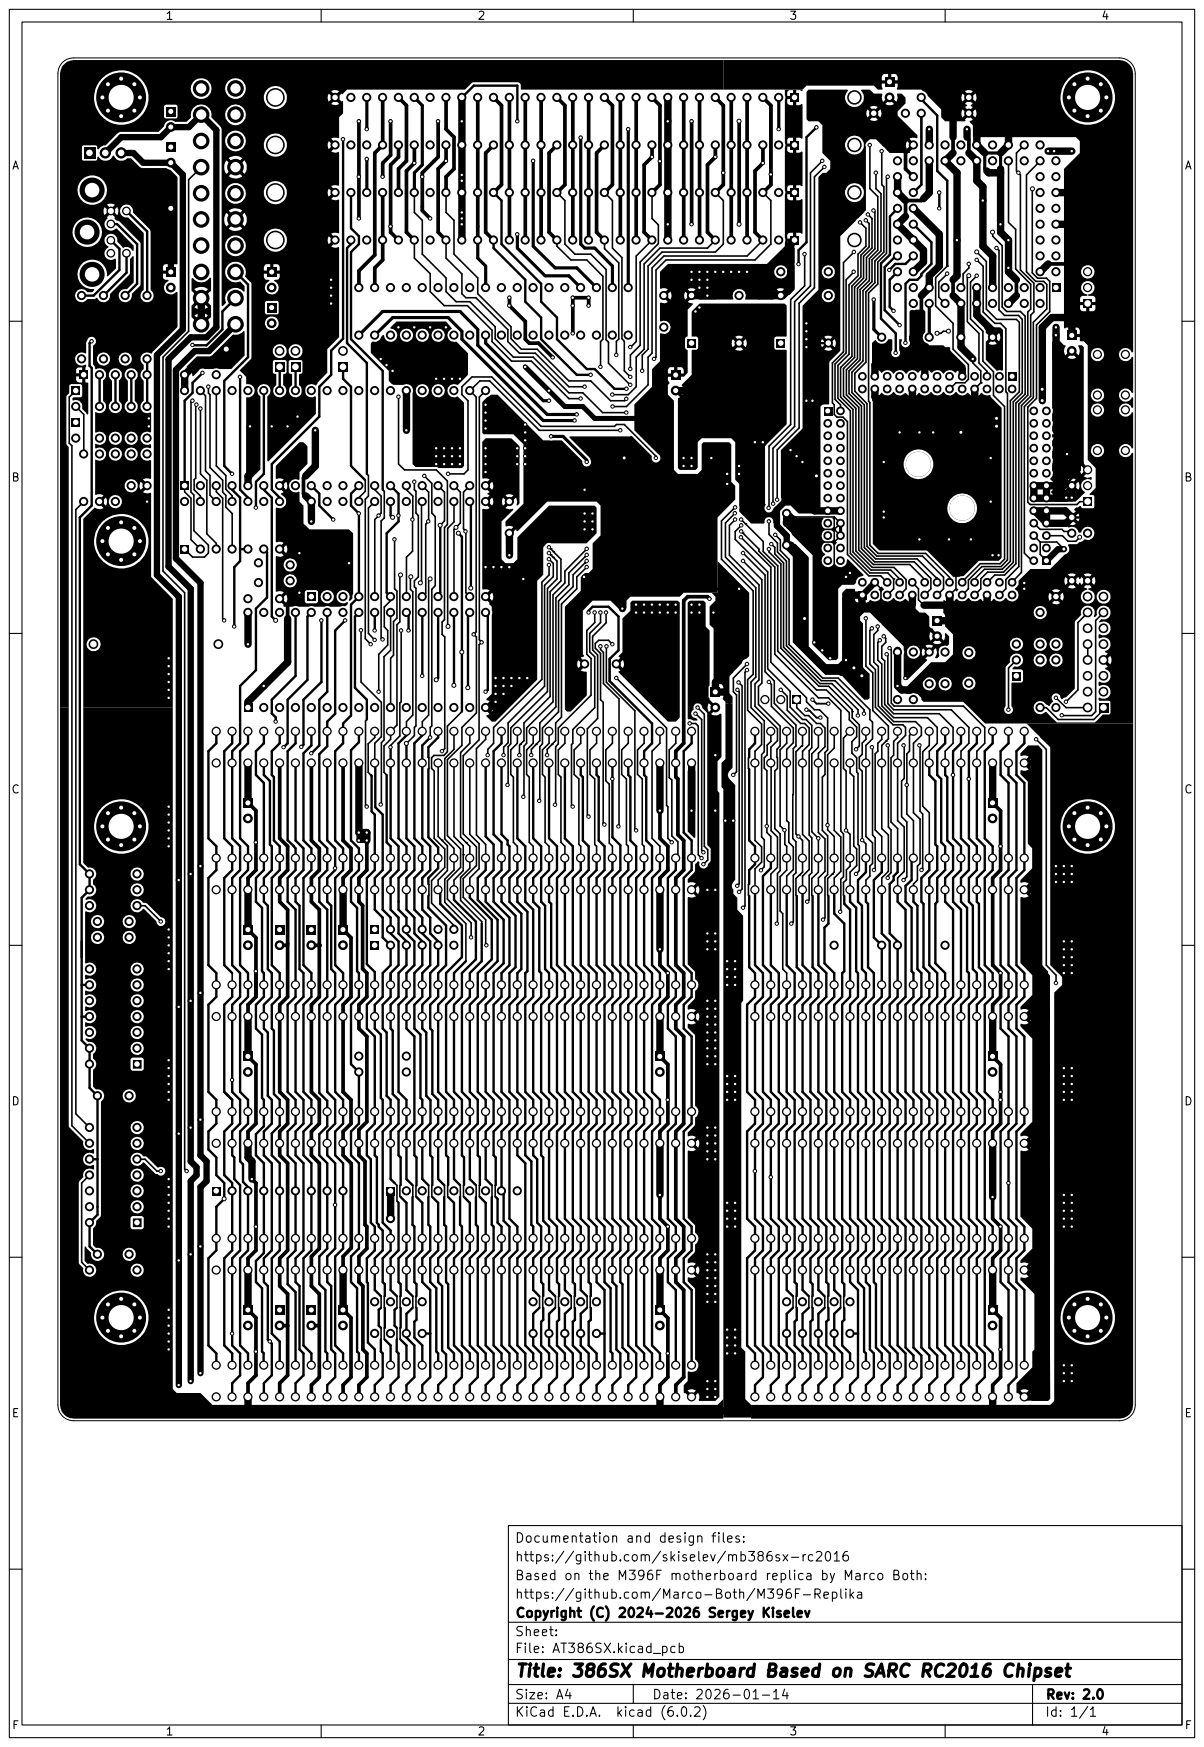
[picture p59: page 2]

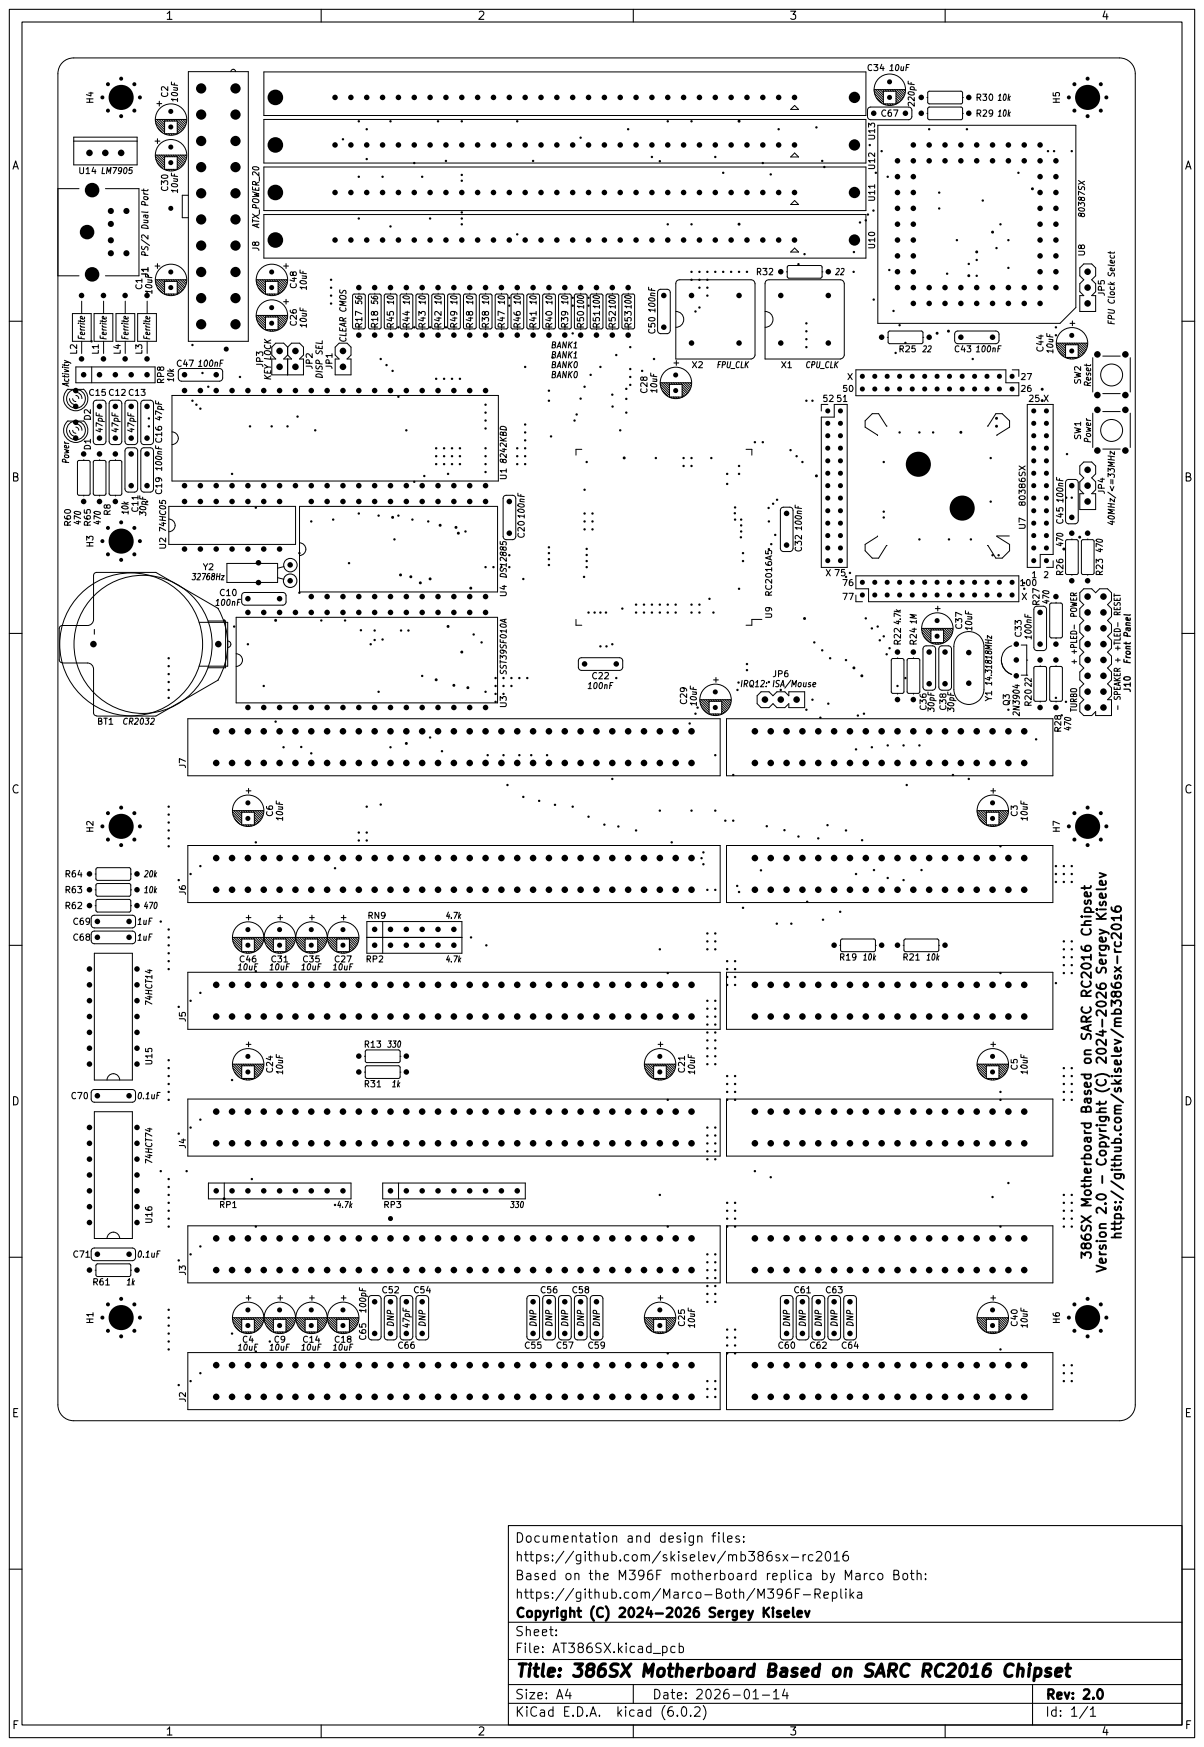
[picture p60: page 3]

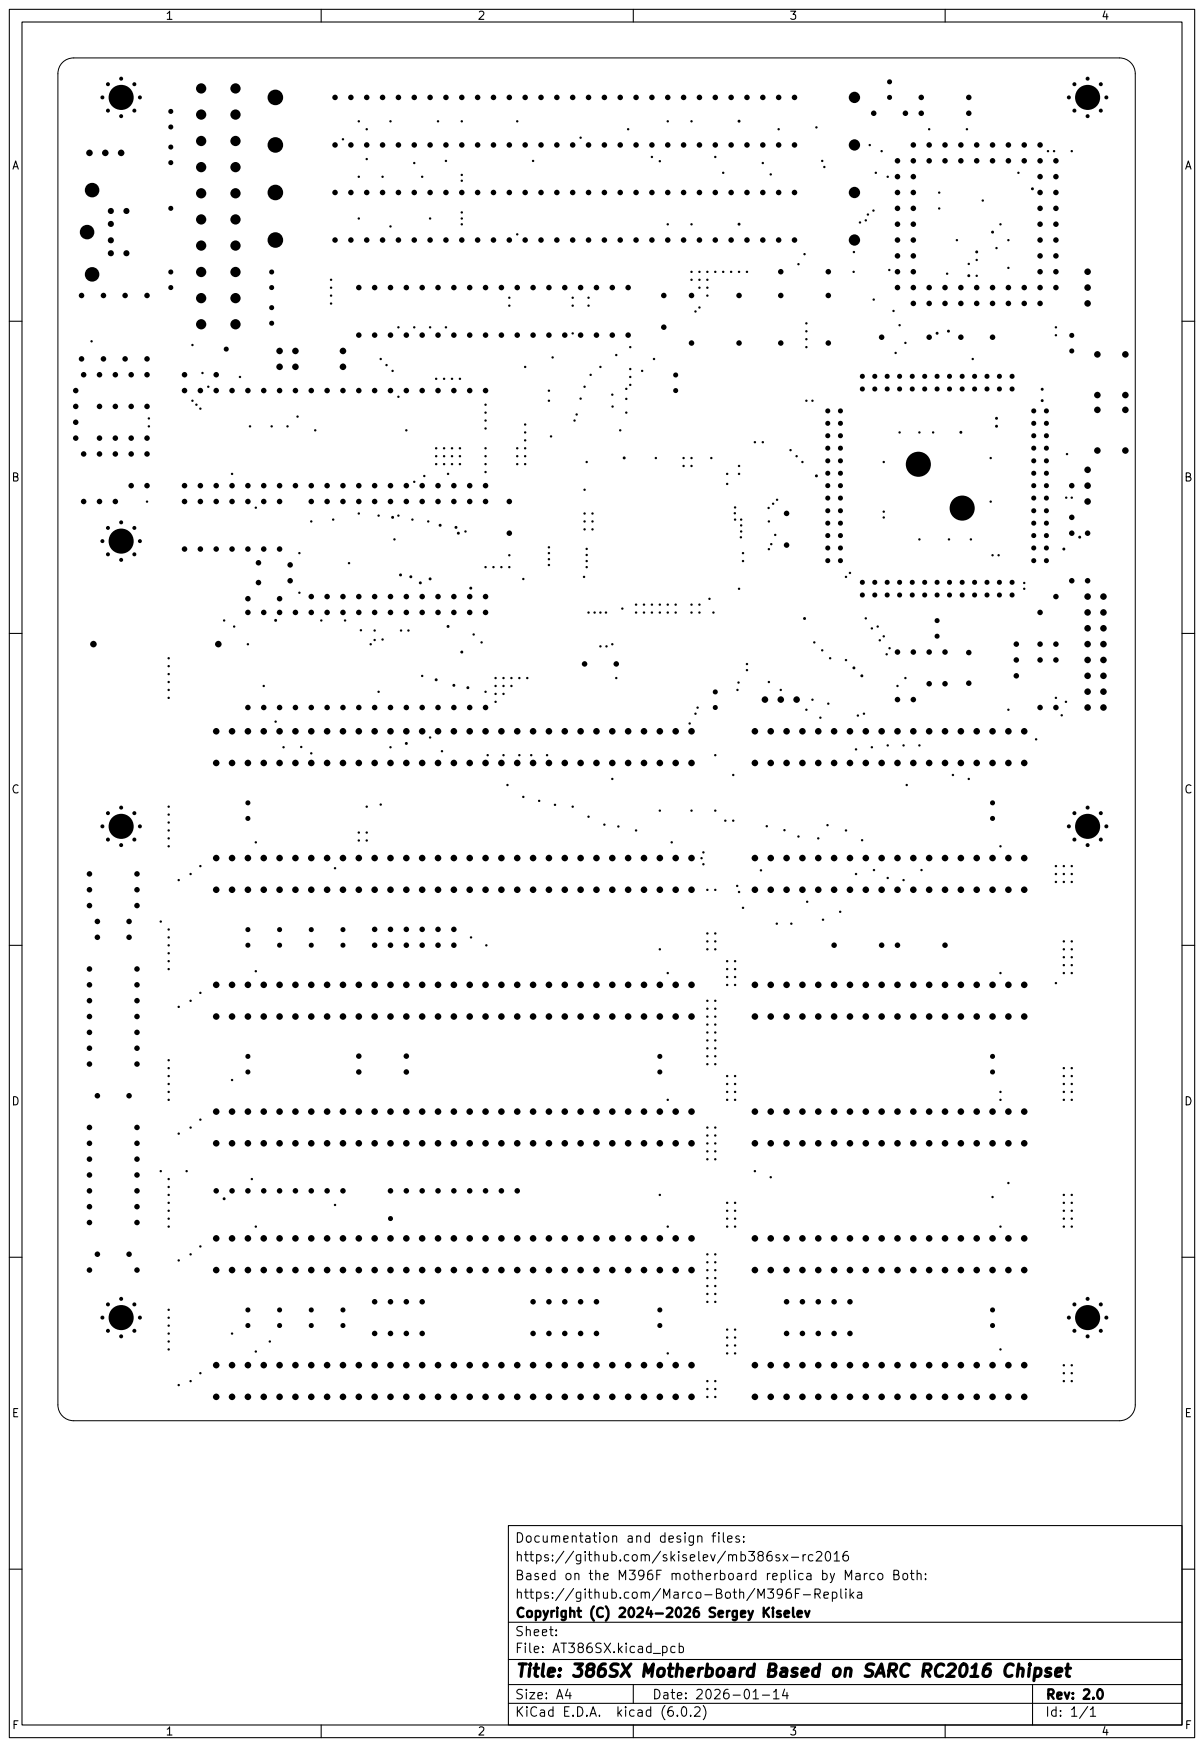
[picture p61: page 4]
