skiselev/mb386sx-rc2016/KiCad/AT386SX-Board-1.9.pdf

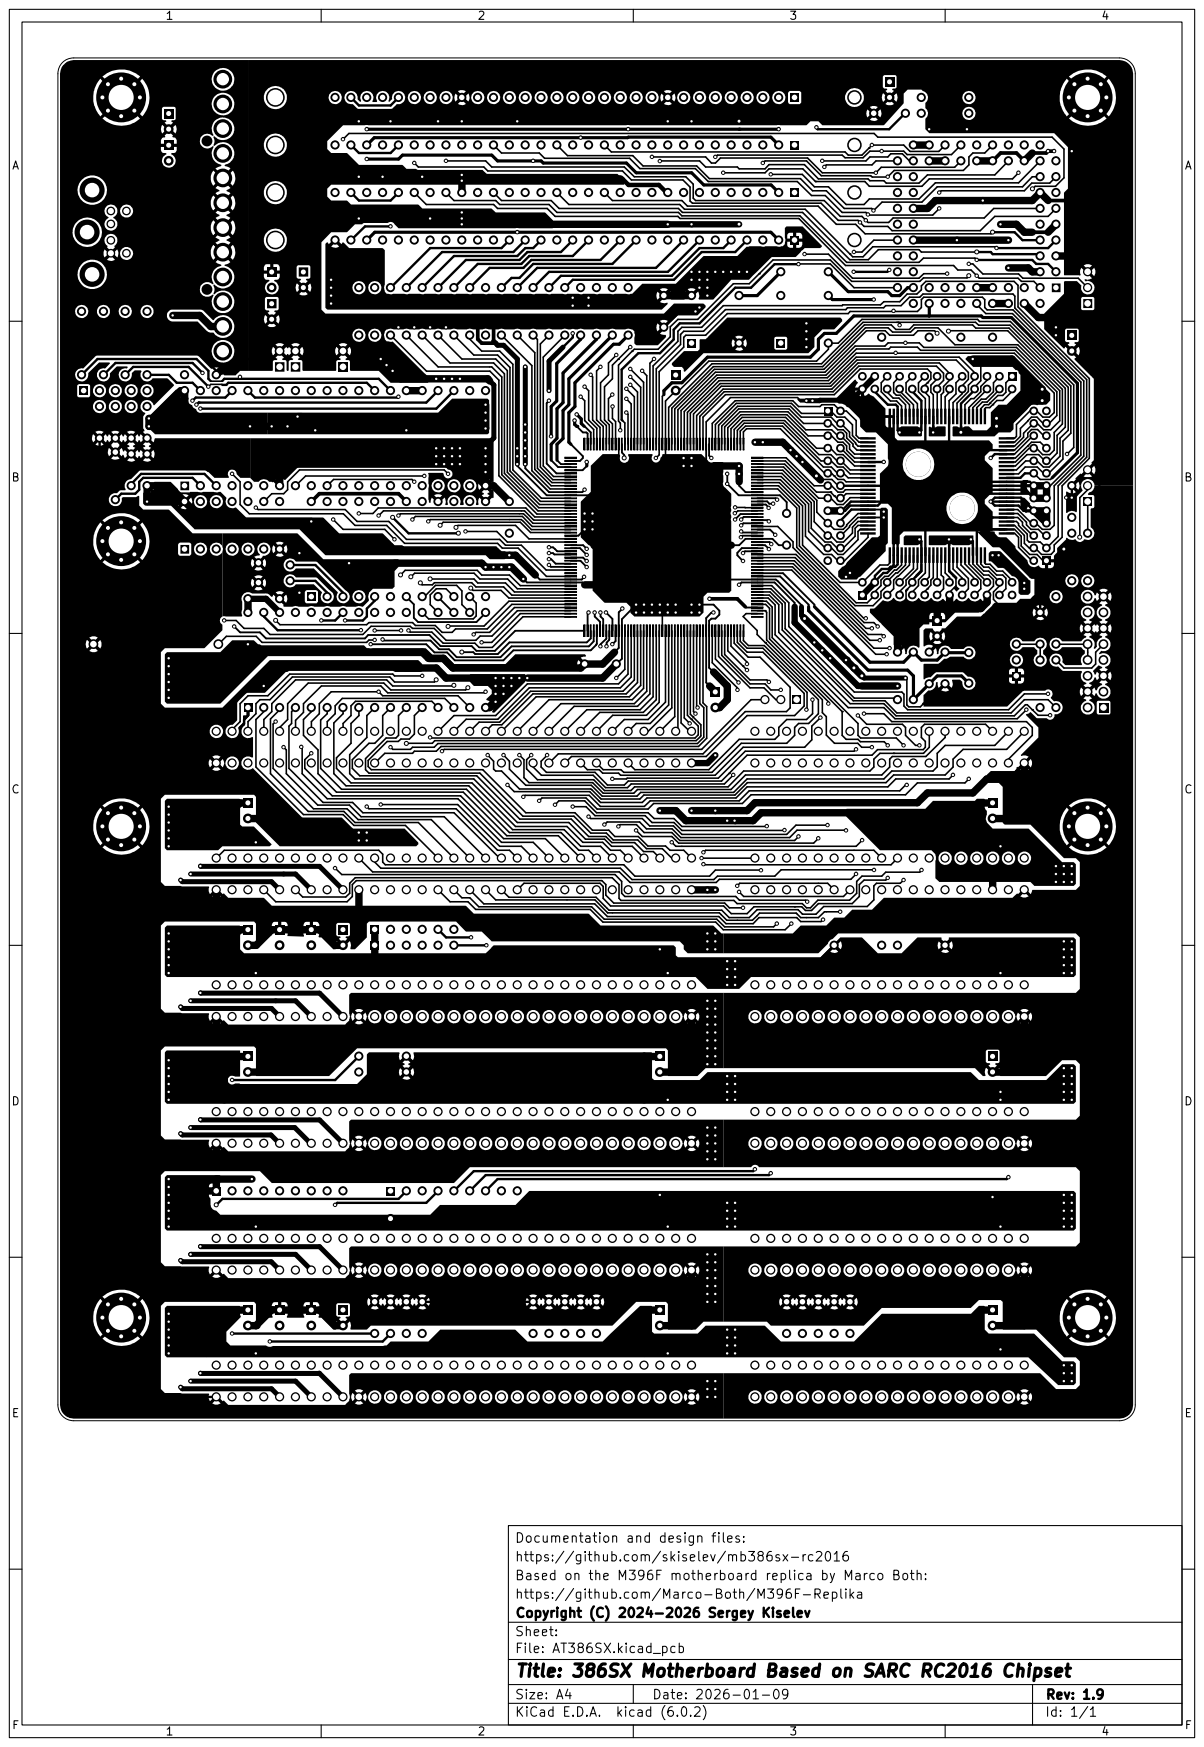
[picture p62: page 1]

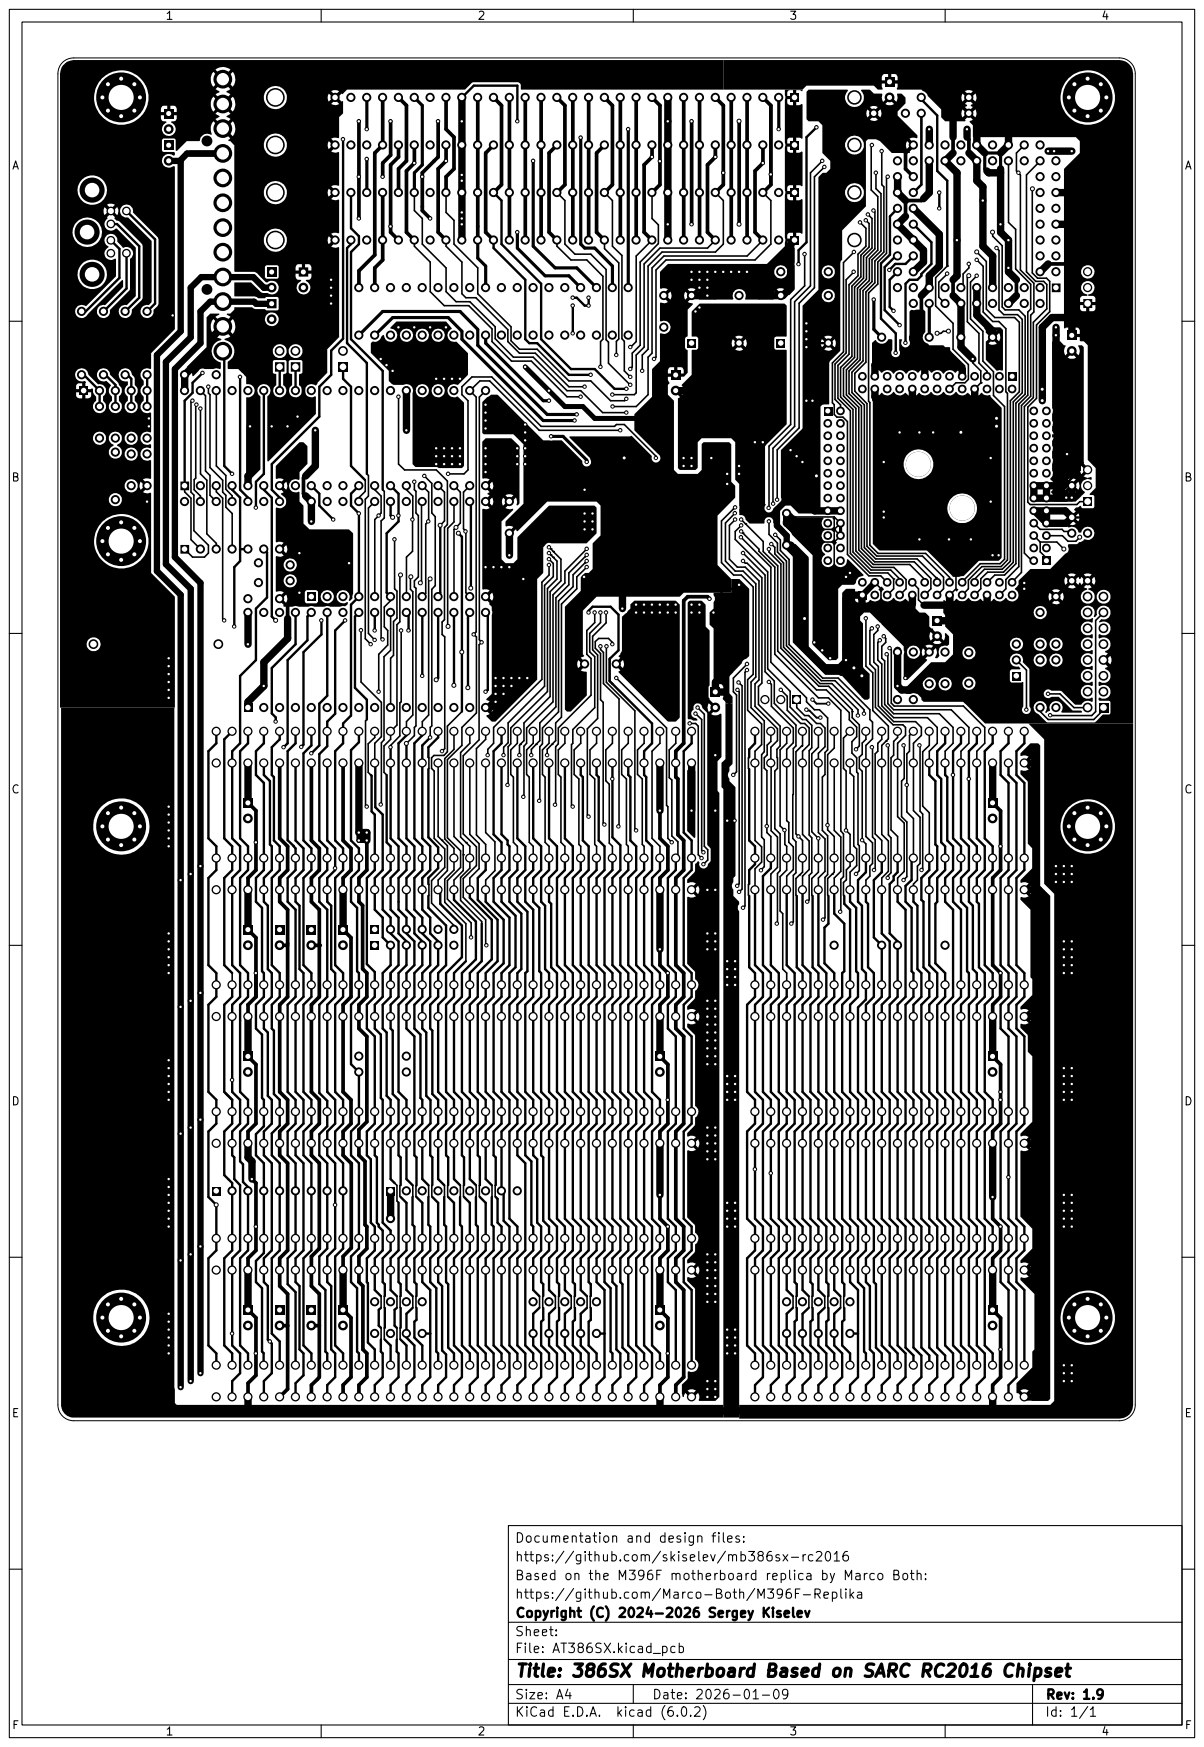
[picture p63: page 2]

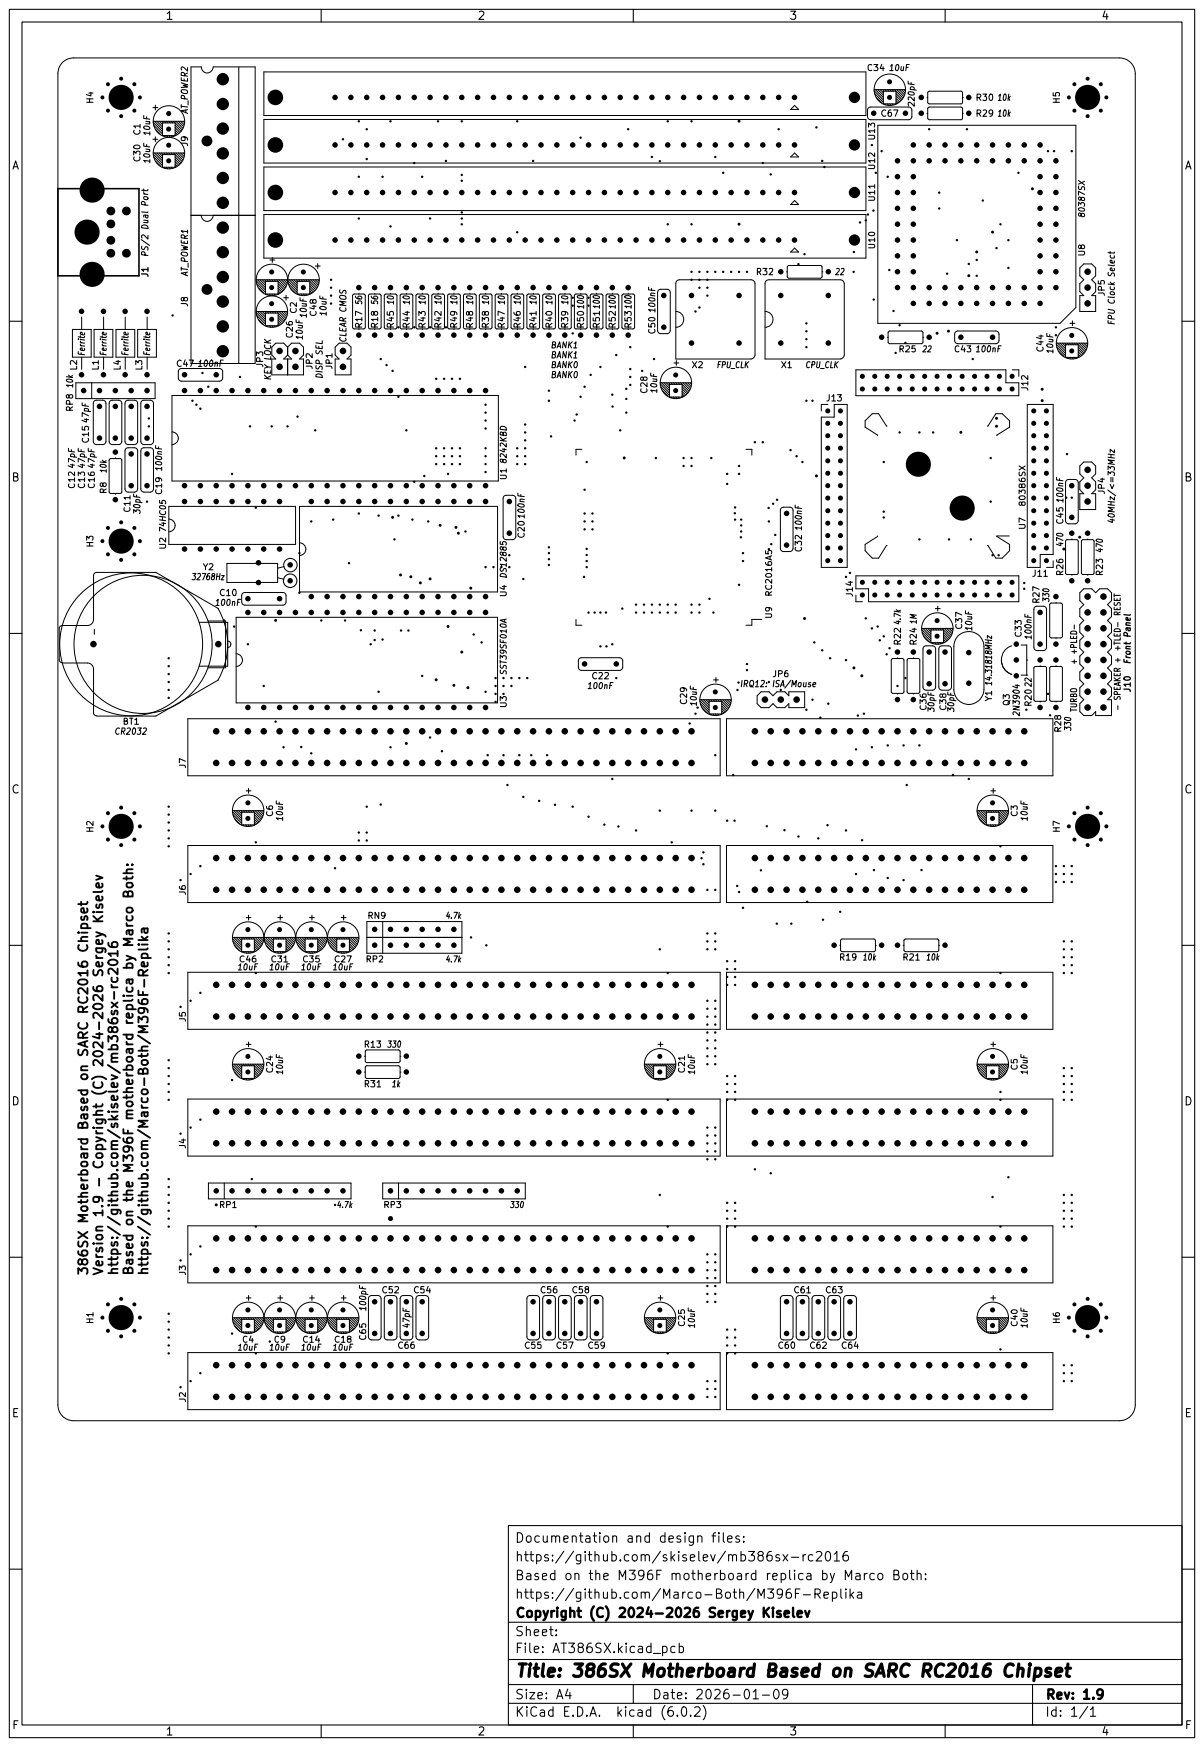
[picture p64: page 3]

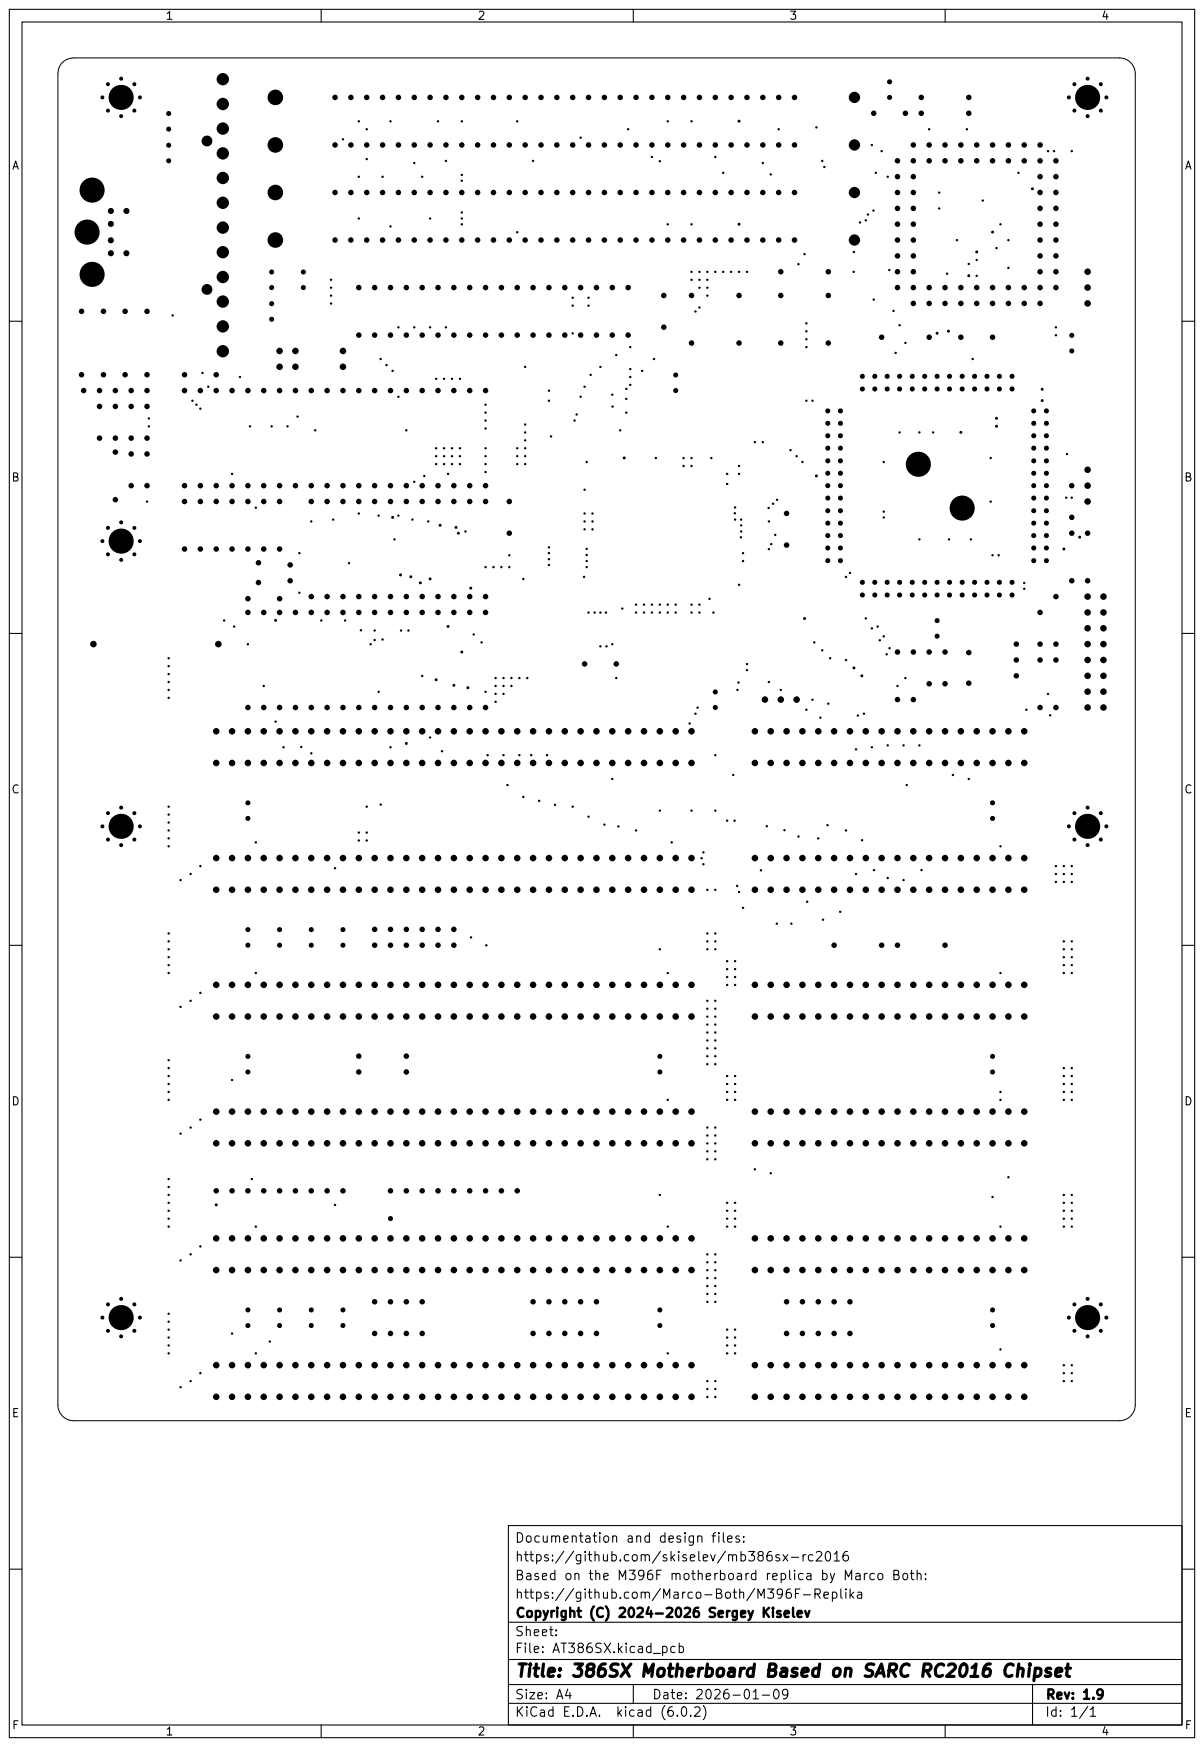
[picture p65: page 4]
