skiselev/mb386sx-rc2016/KiCad/AT386SX-Board-1.8.pdf

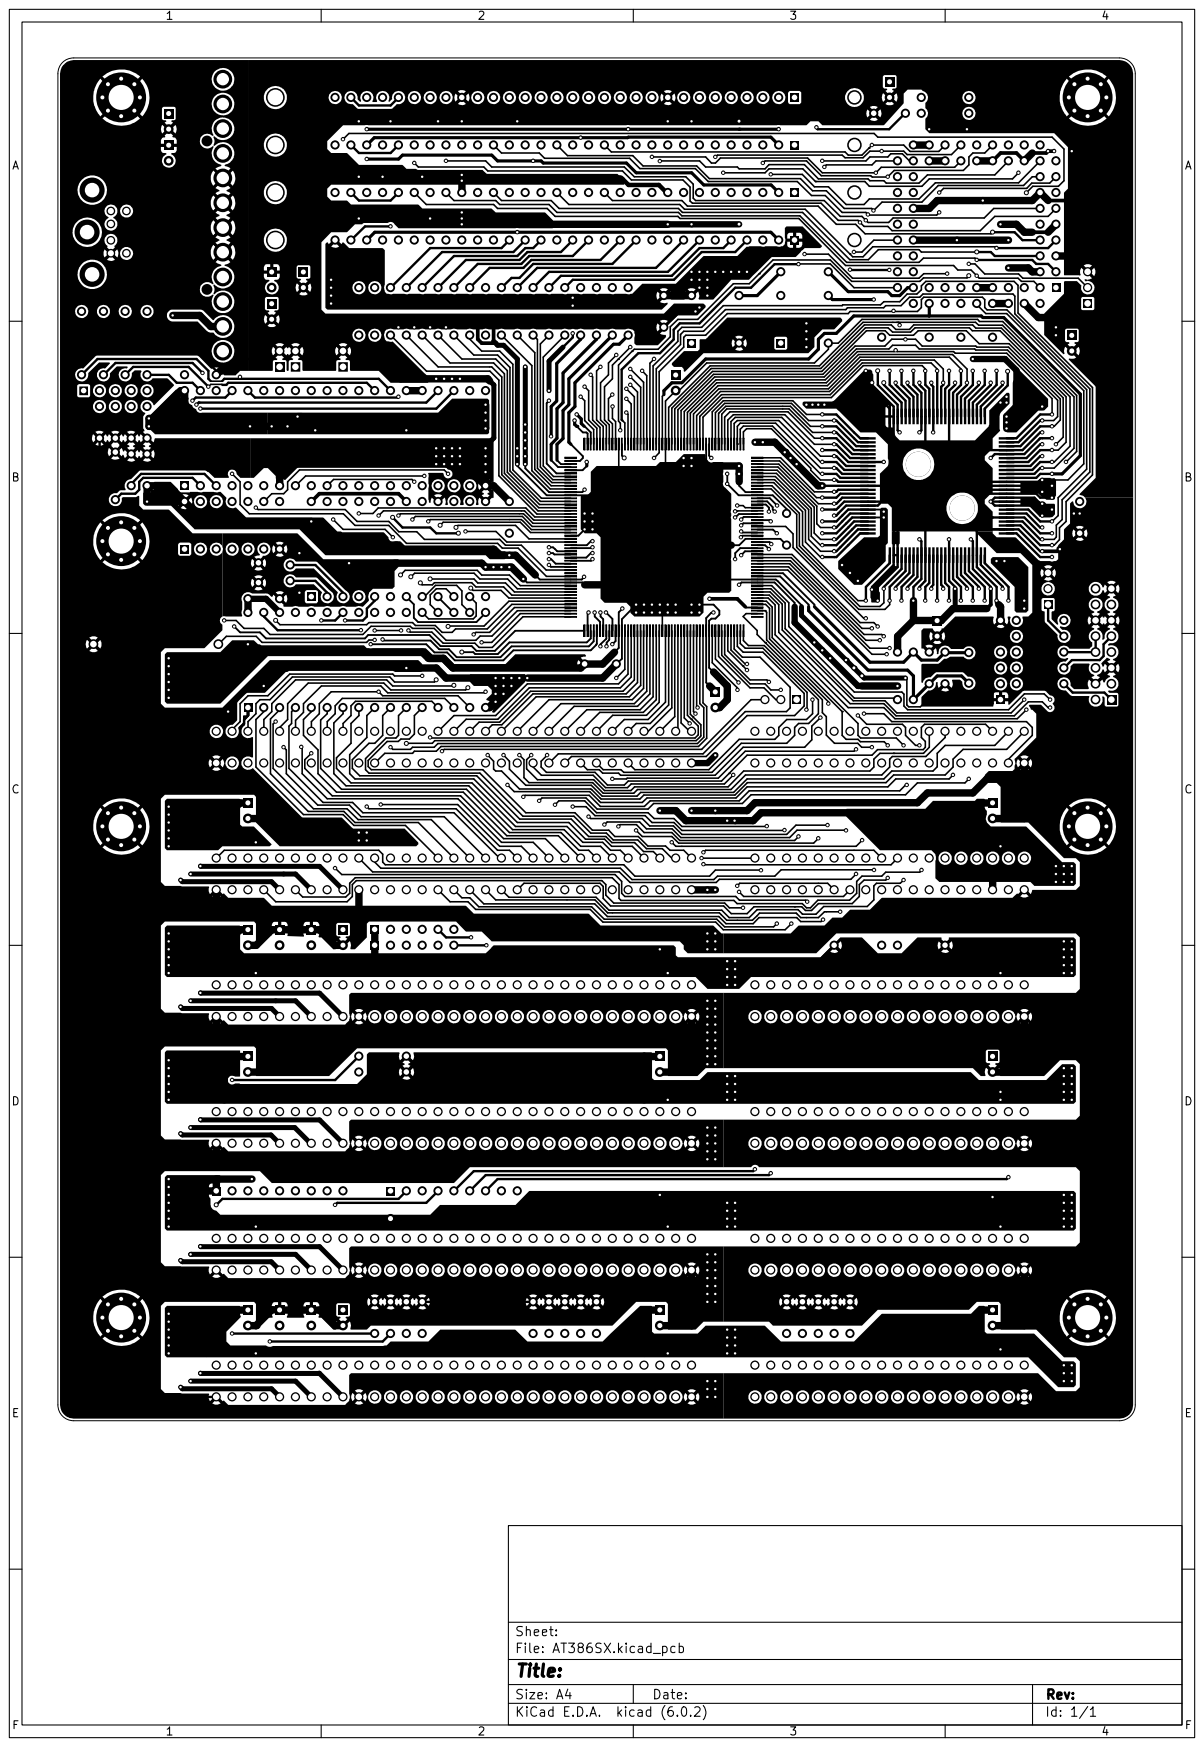
[picture p66: page 1]

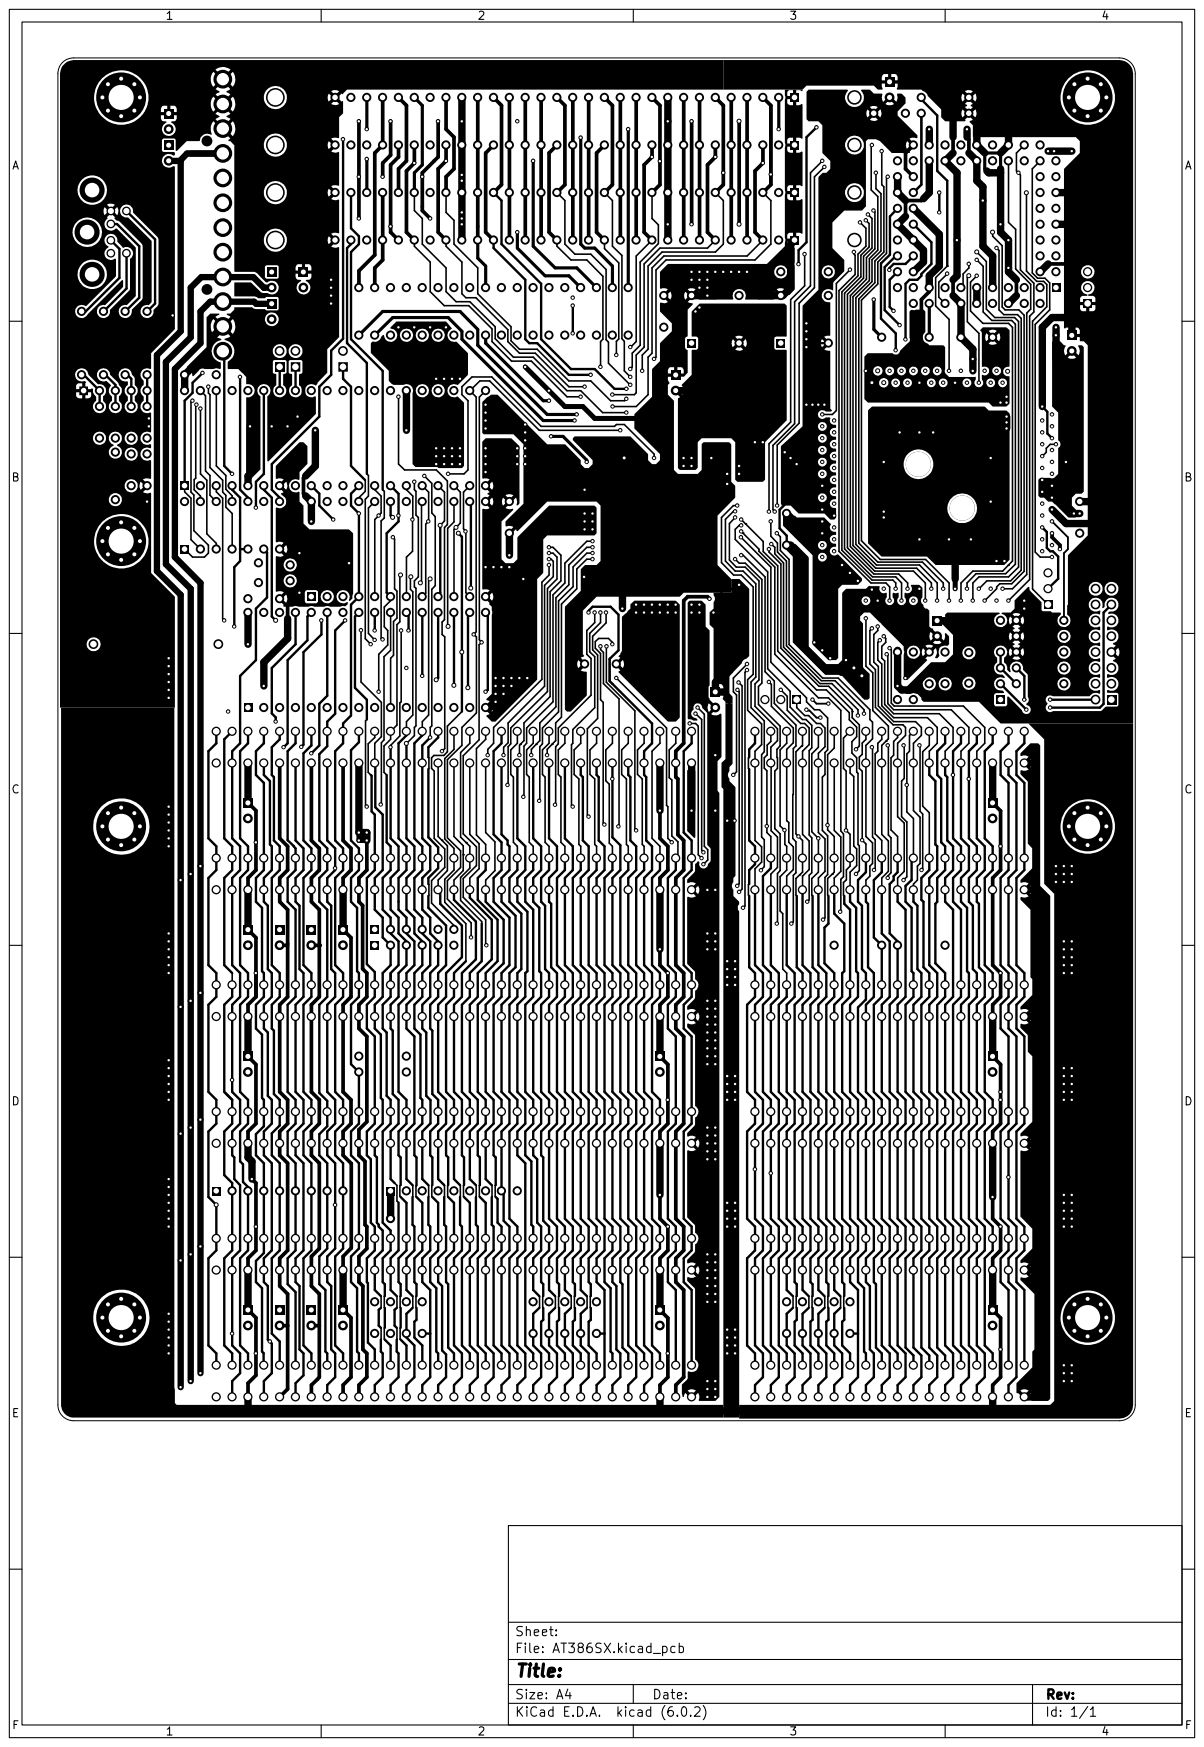
[picture p67: page 2]

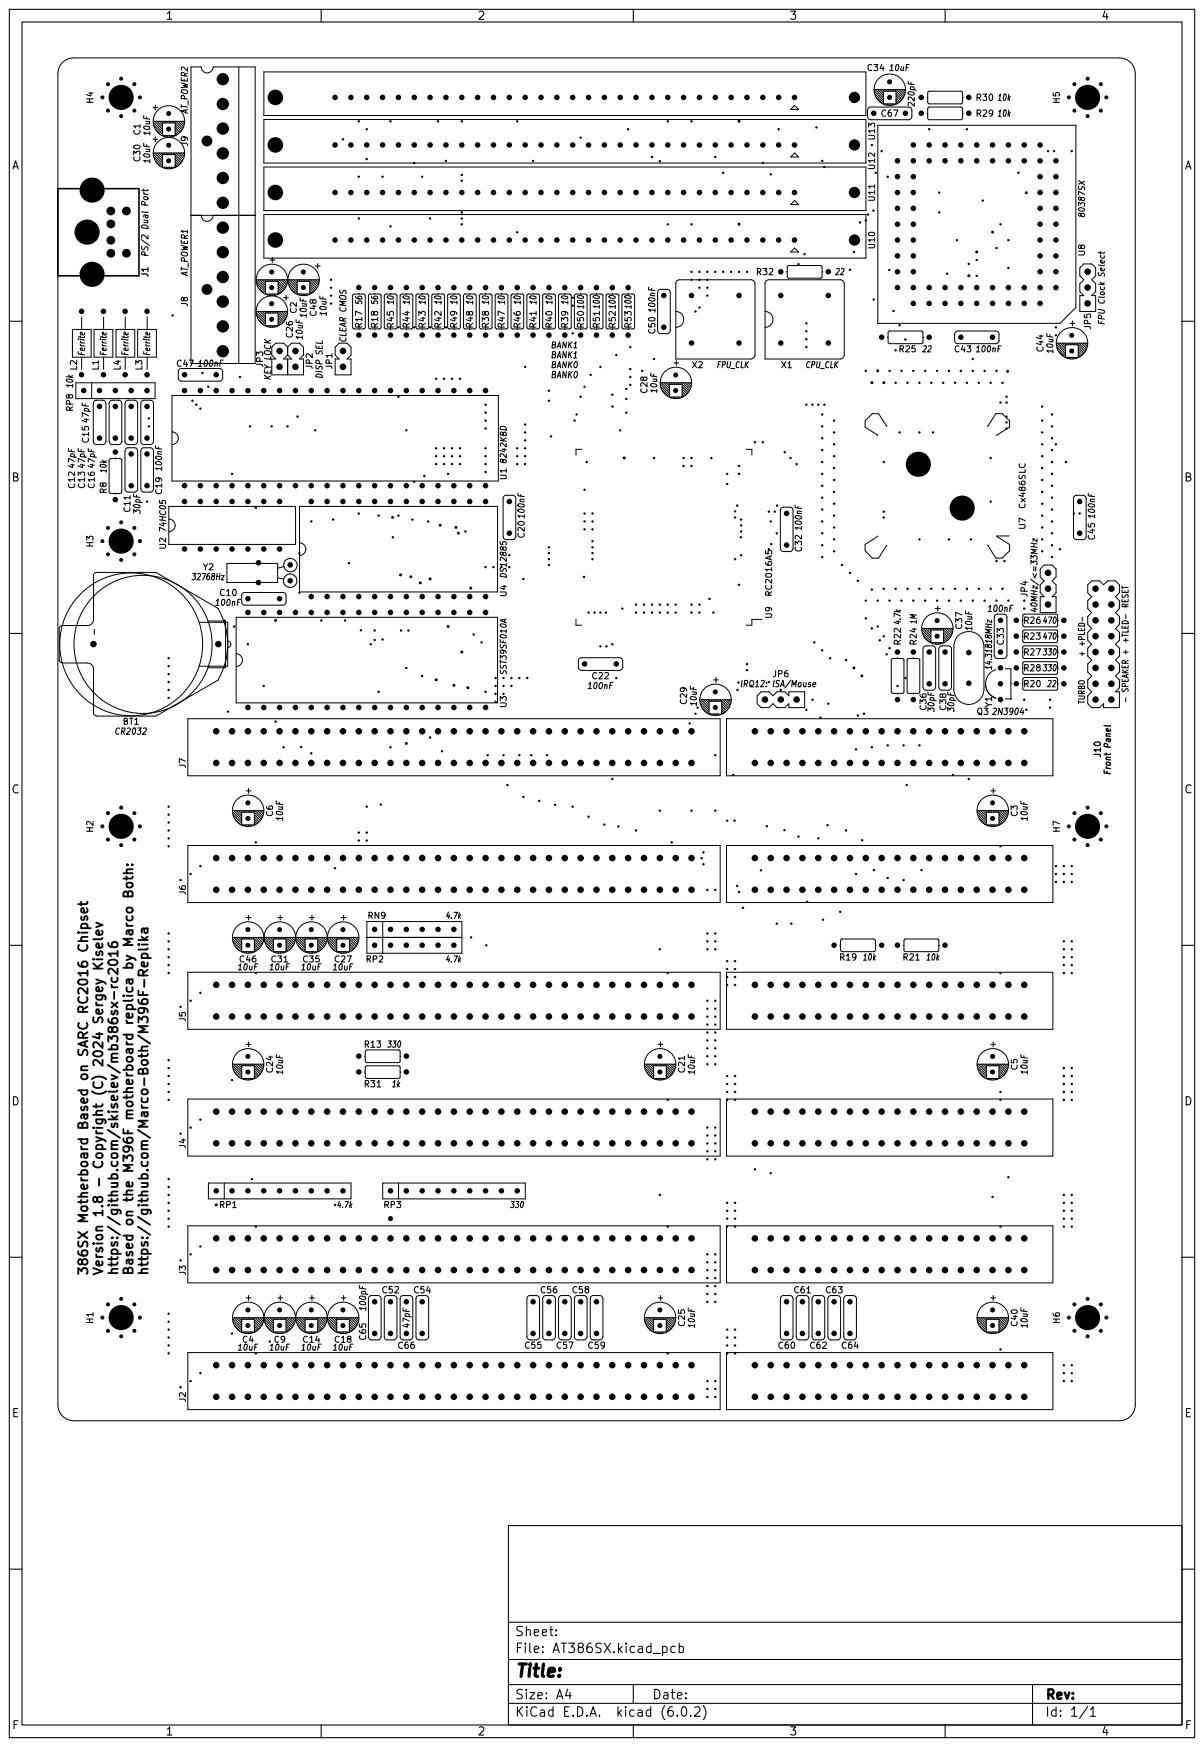
[picture p68: page 3]

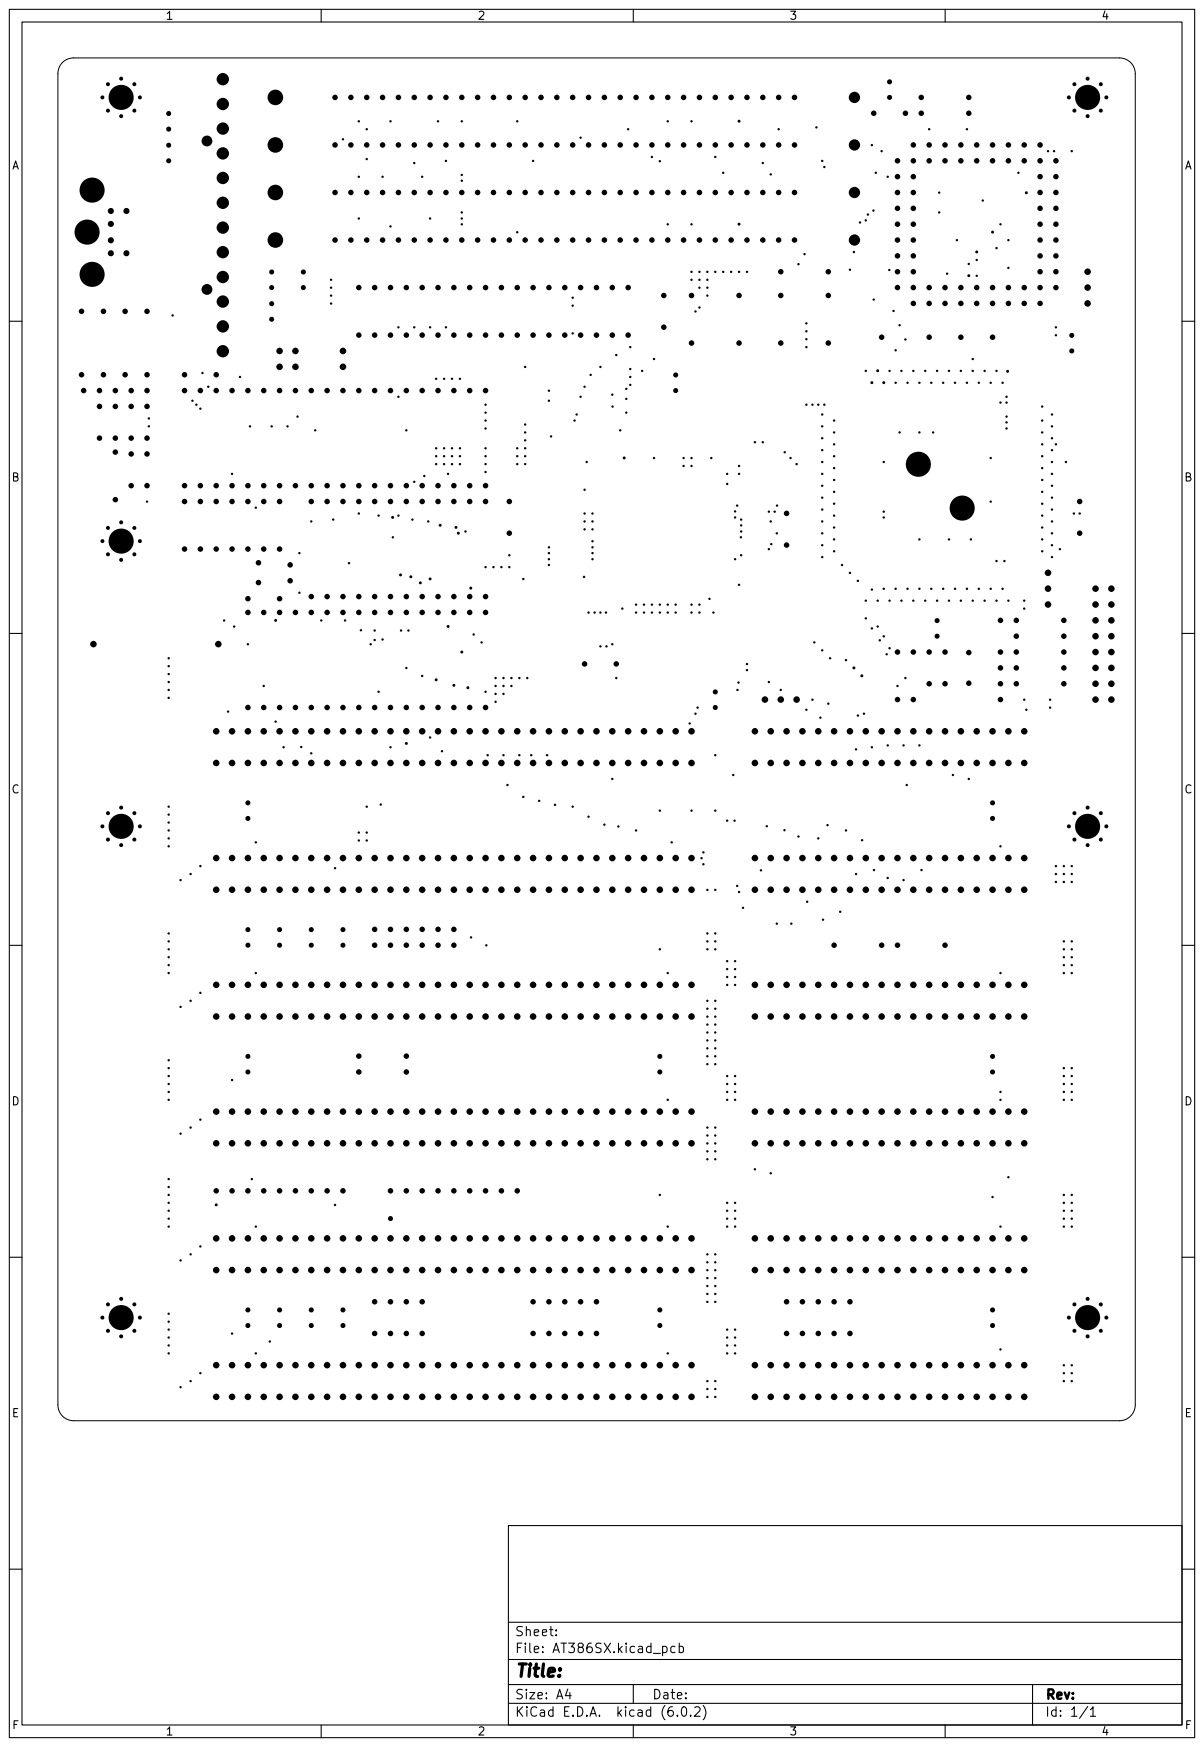
[picture p69: page 4]
