skiselev/mb386sx-rc2016/KiCad/AT386SX-Board-1.7.pdf

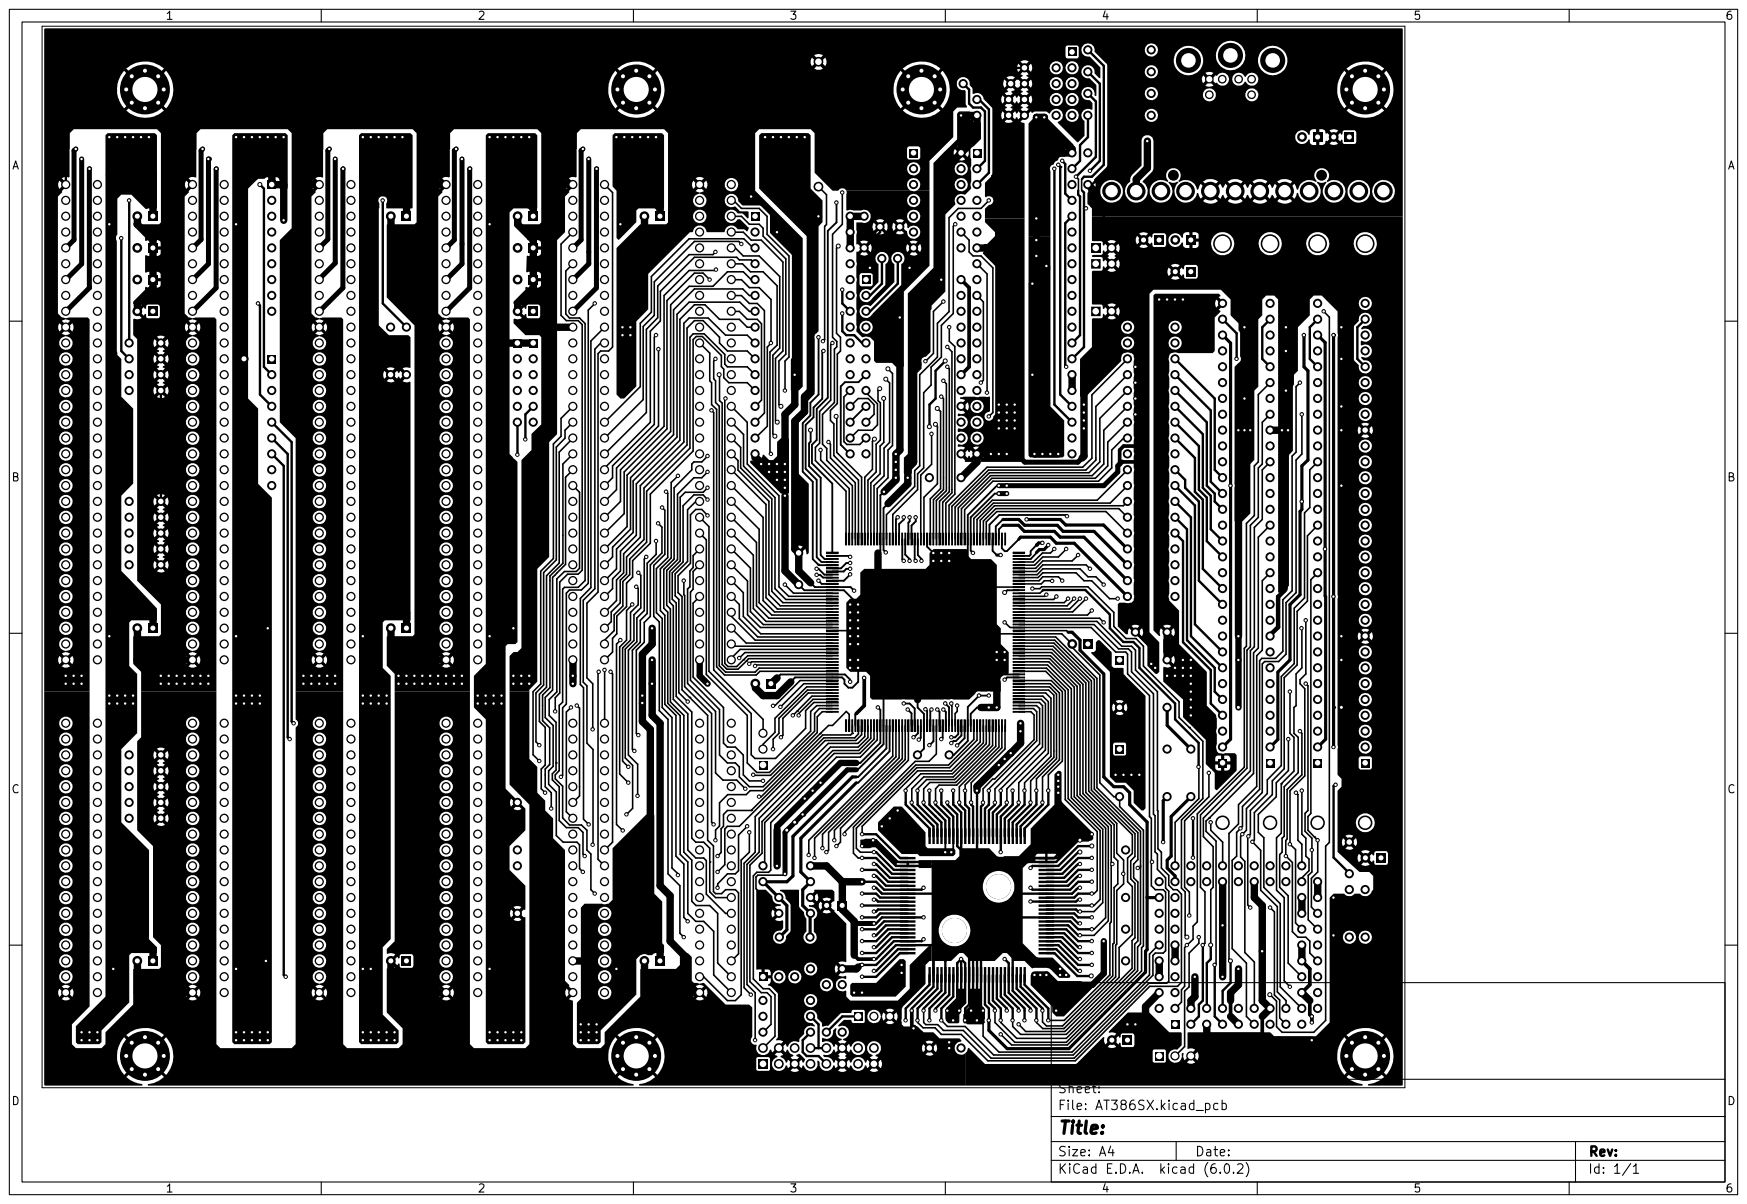
[picture p70: page 1]

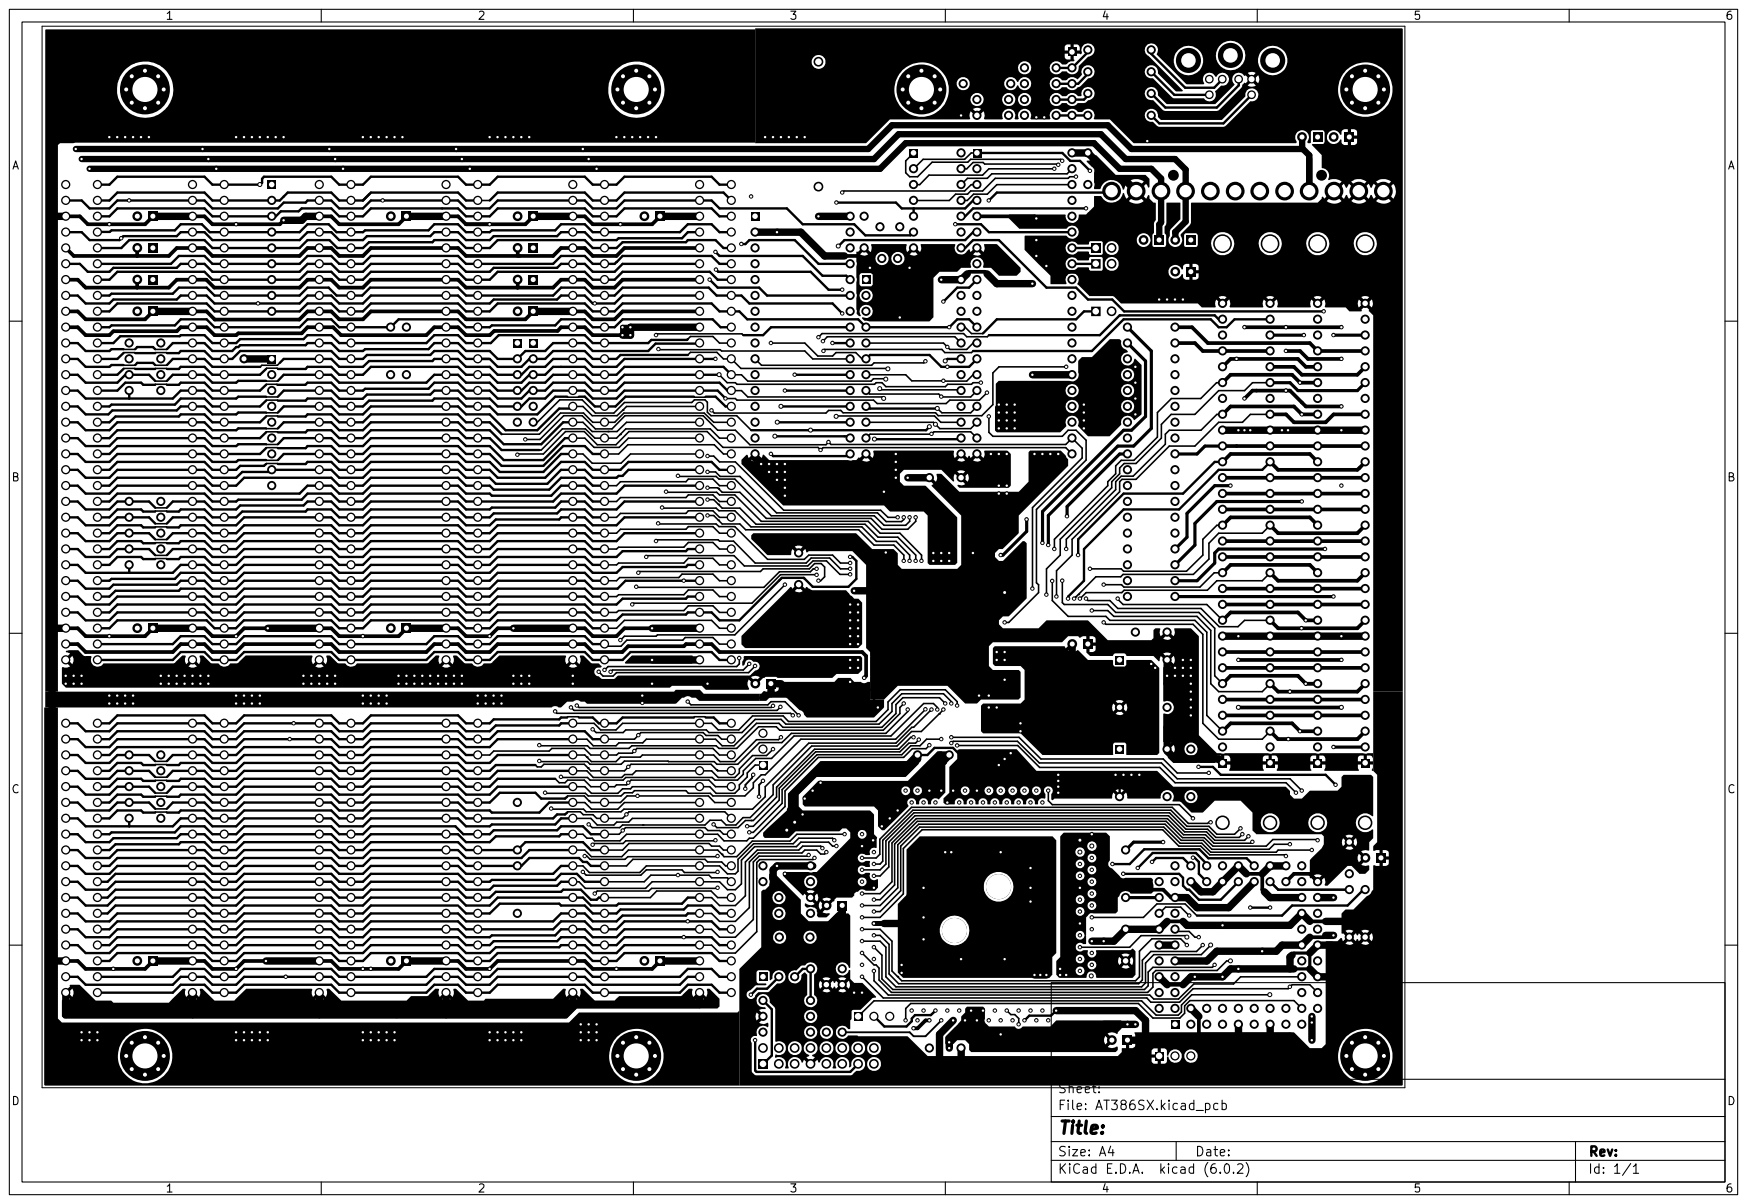
[picture p71: page 2]

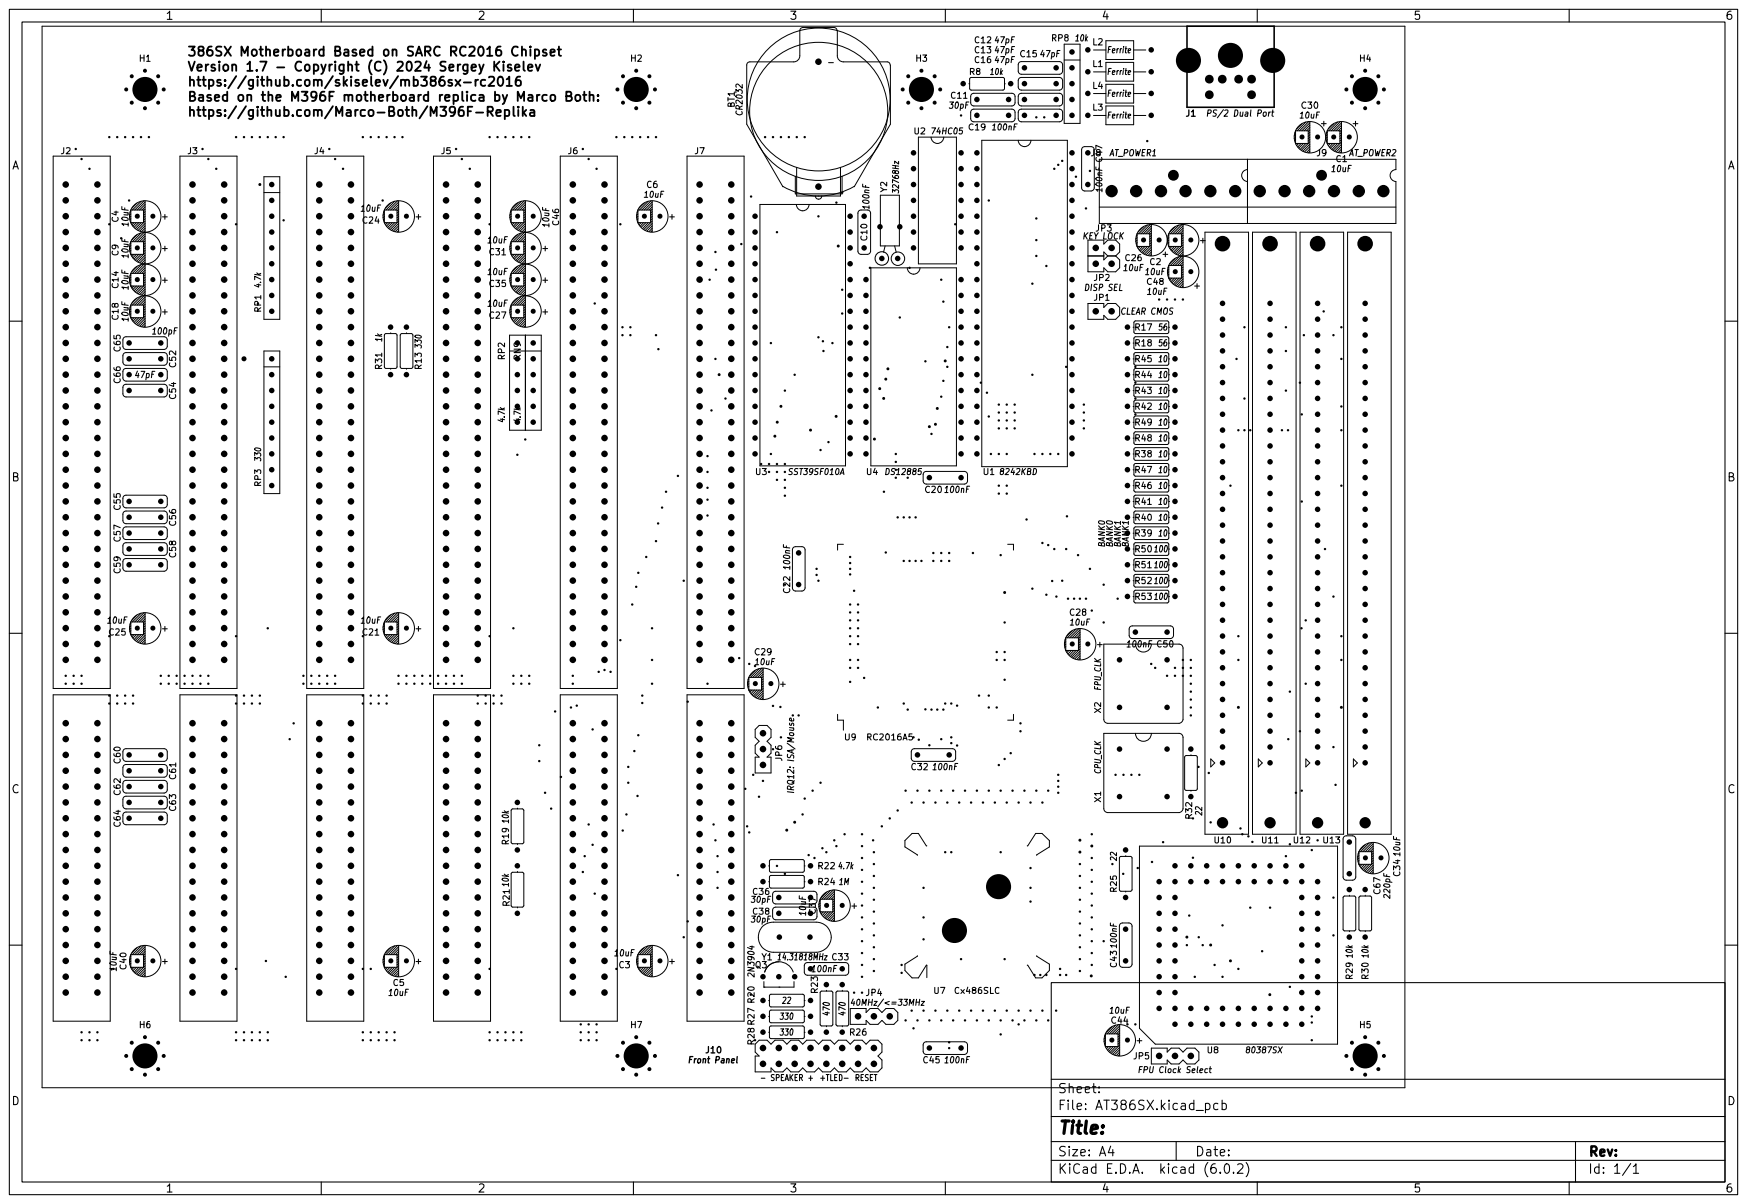
[picture p72: page 3]

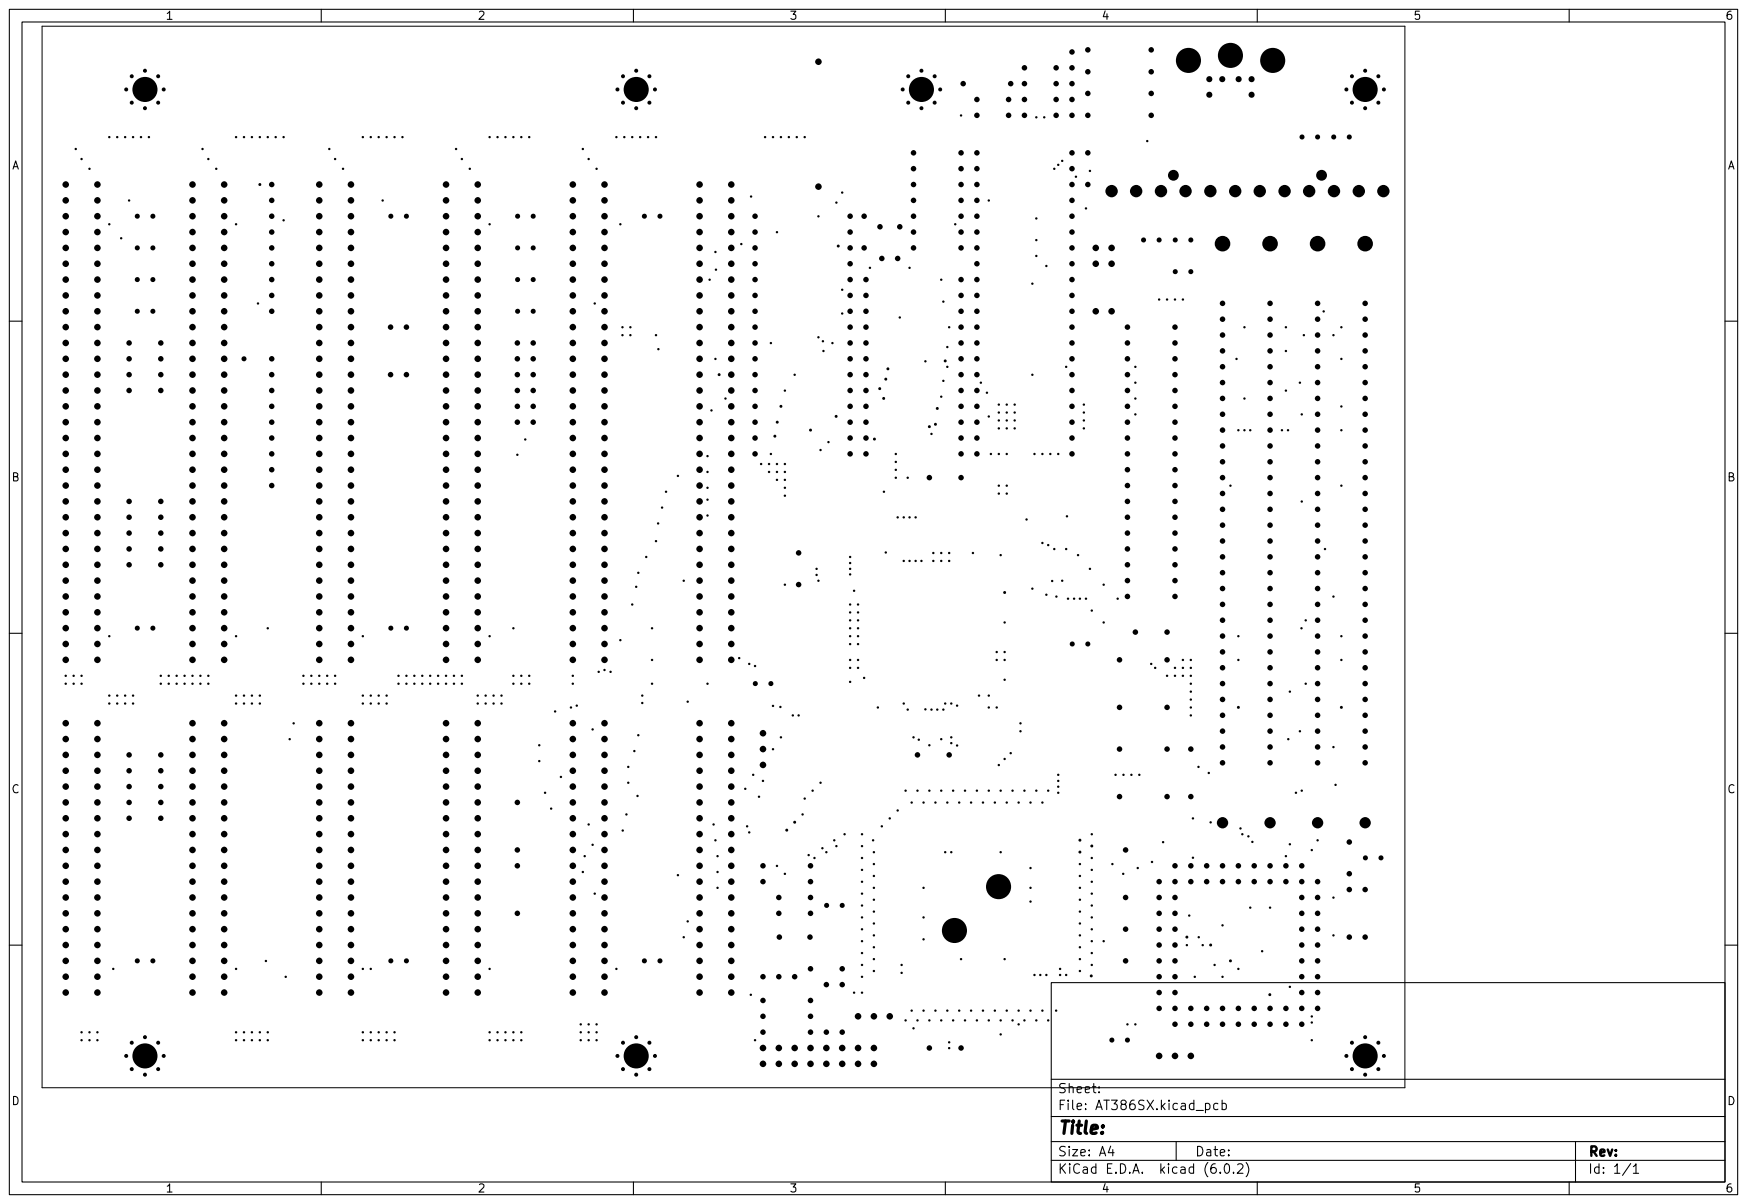
[picture p73: page 4]
