skiselev/mb386sx-rc2016/KiCad/AT386SX-Board-1.6.pdf

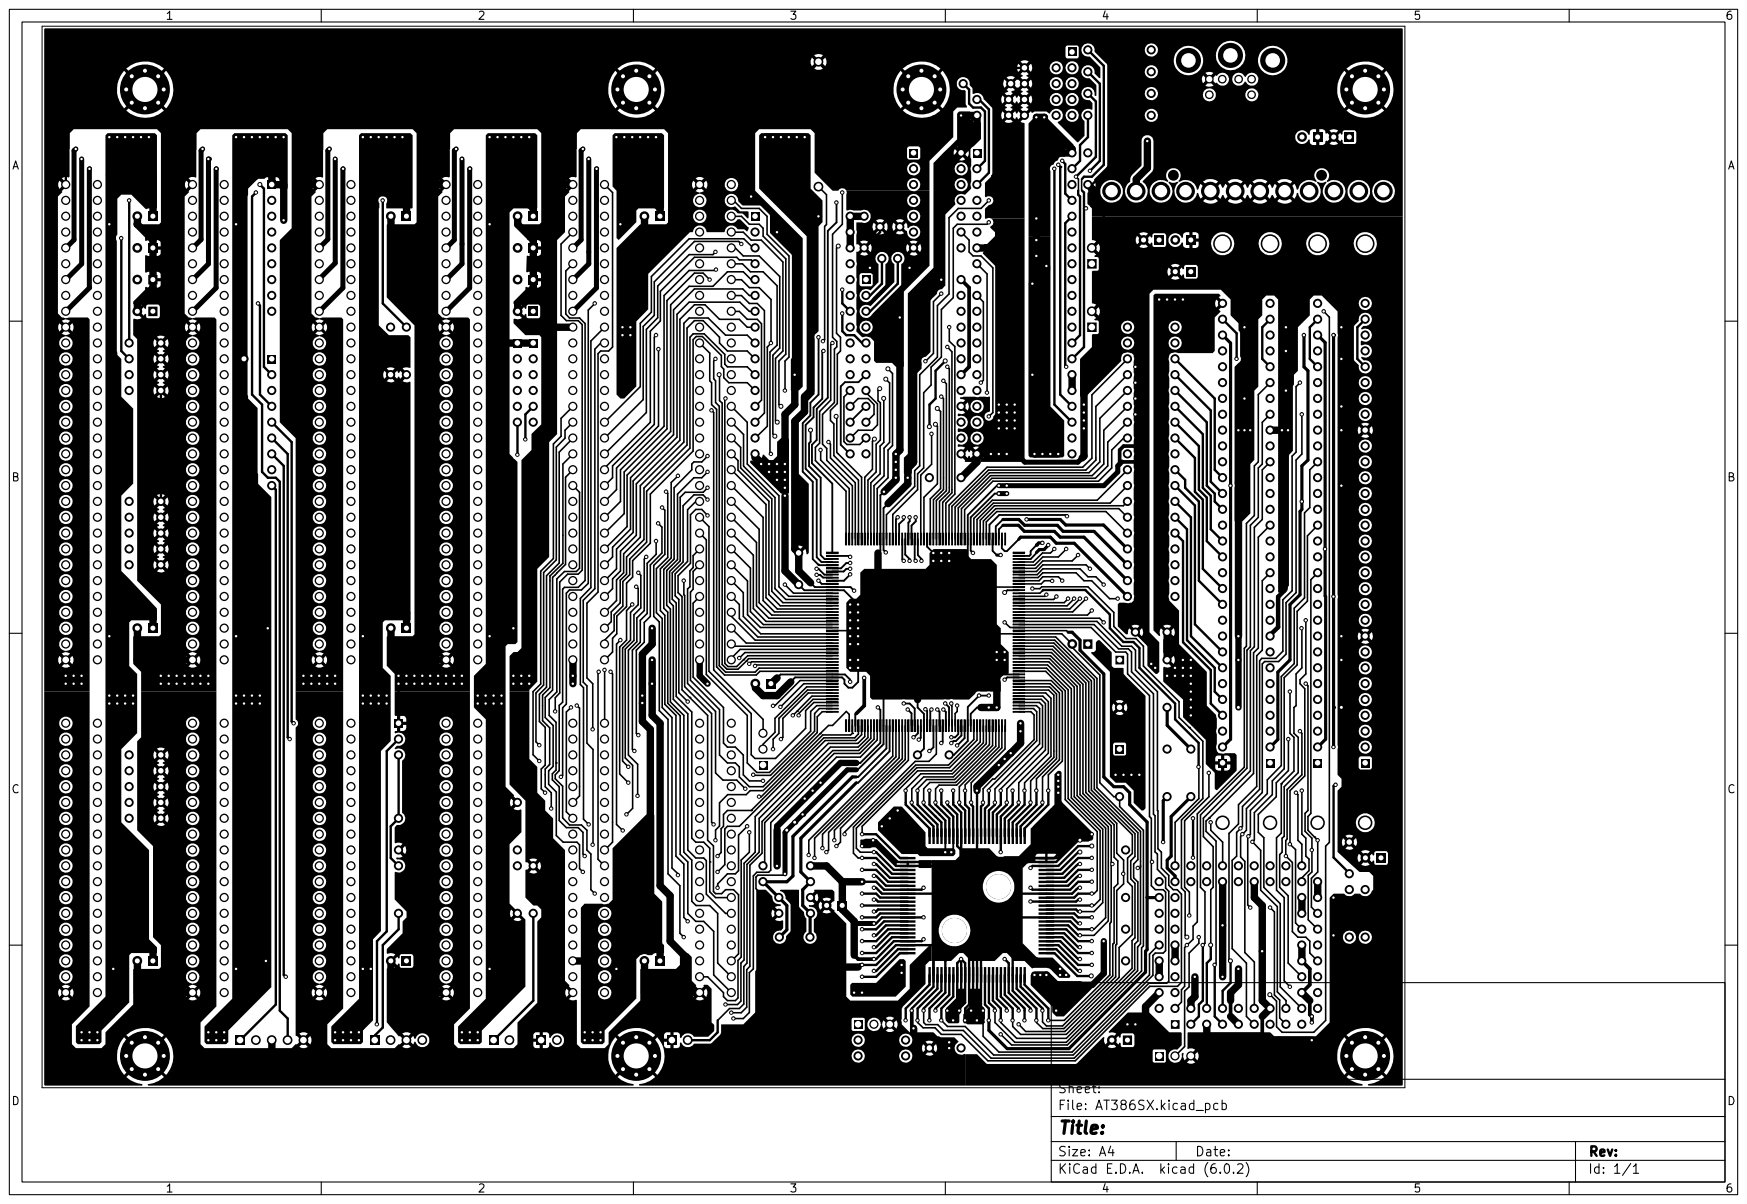
[picture p74: page 1]

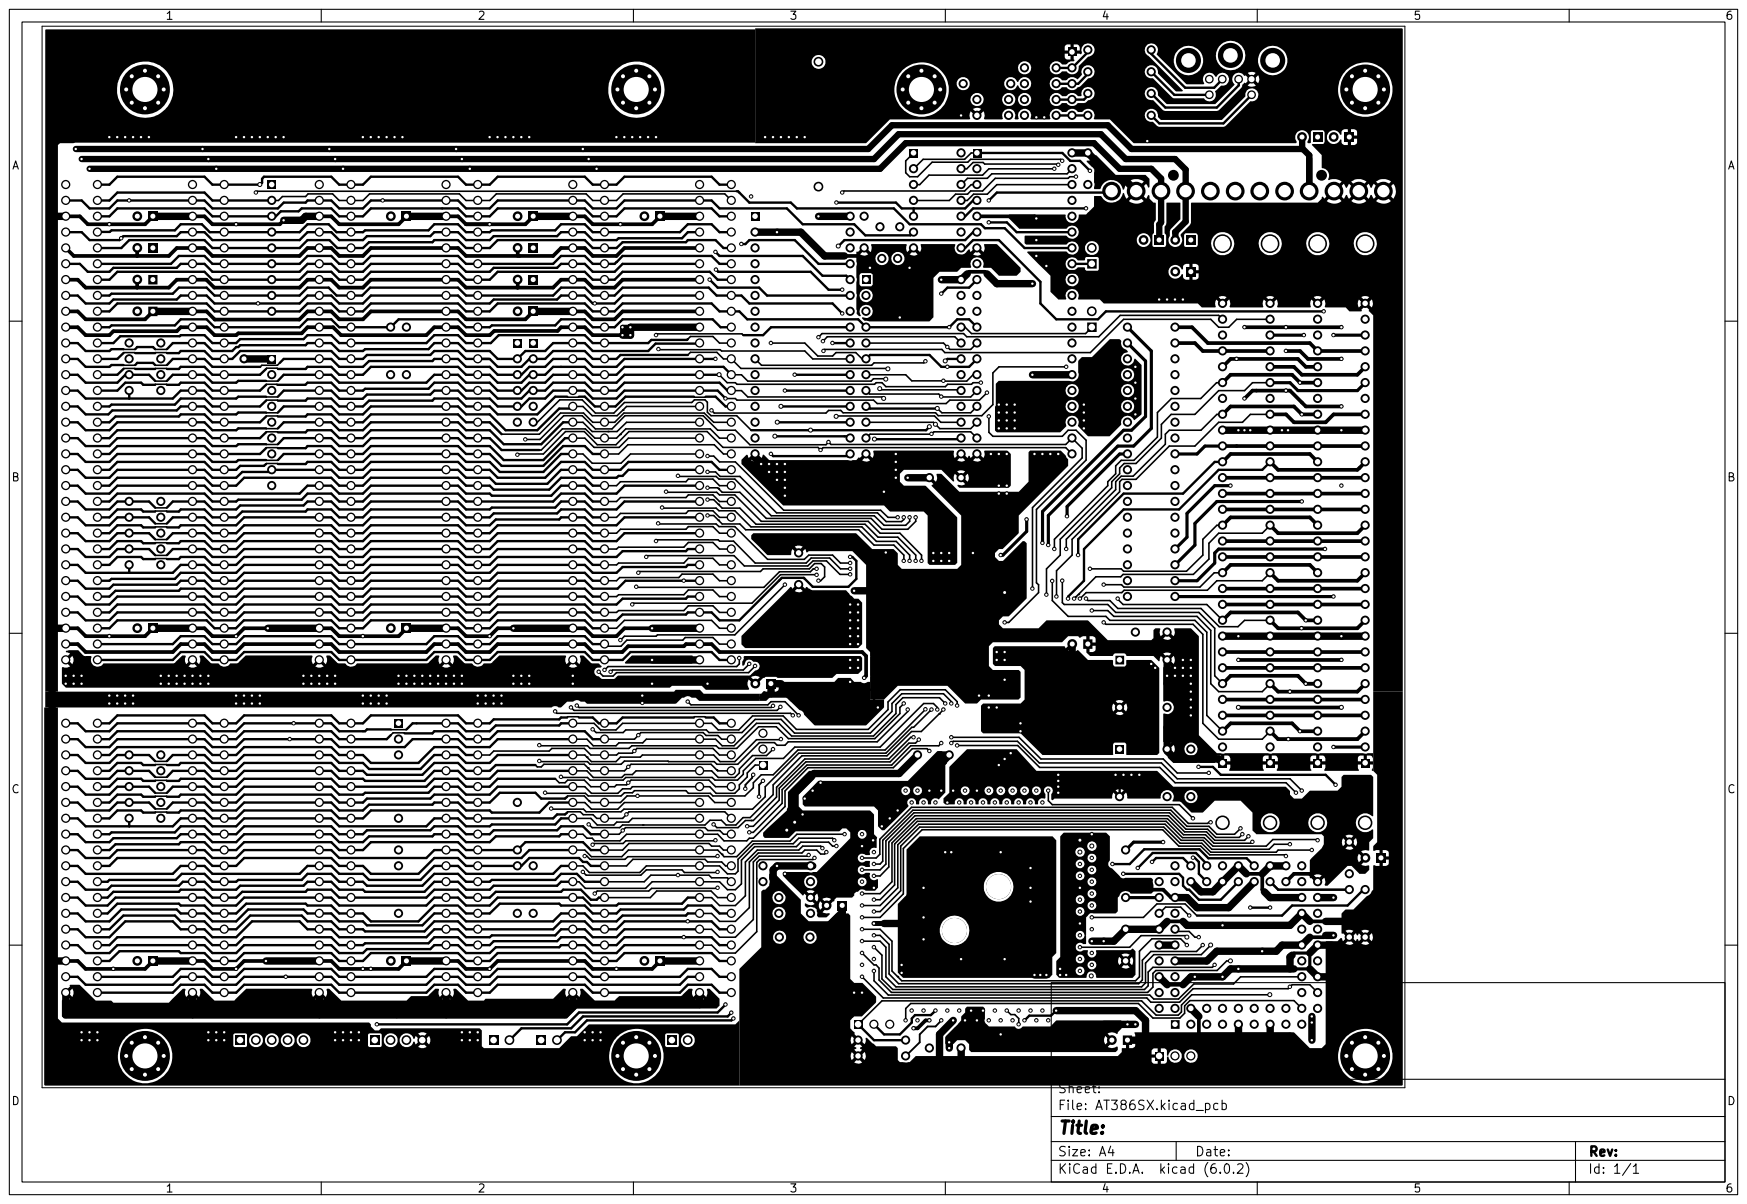
[picture p75: page 2]

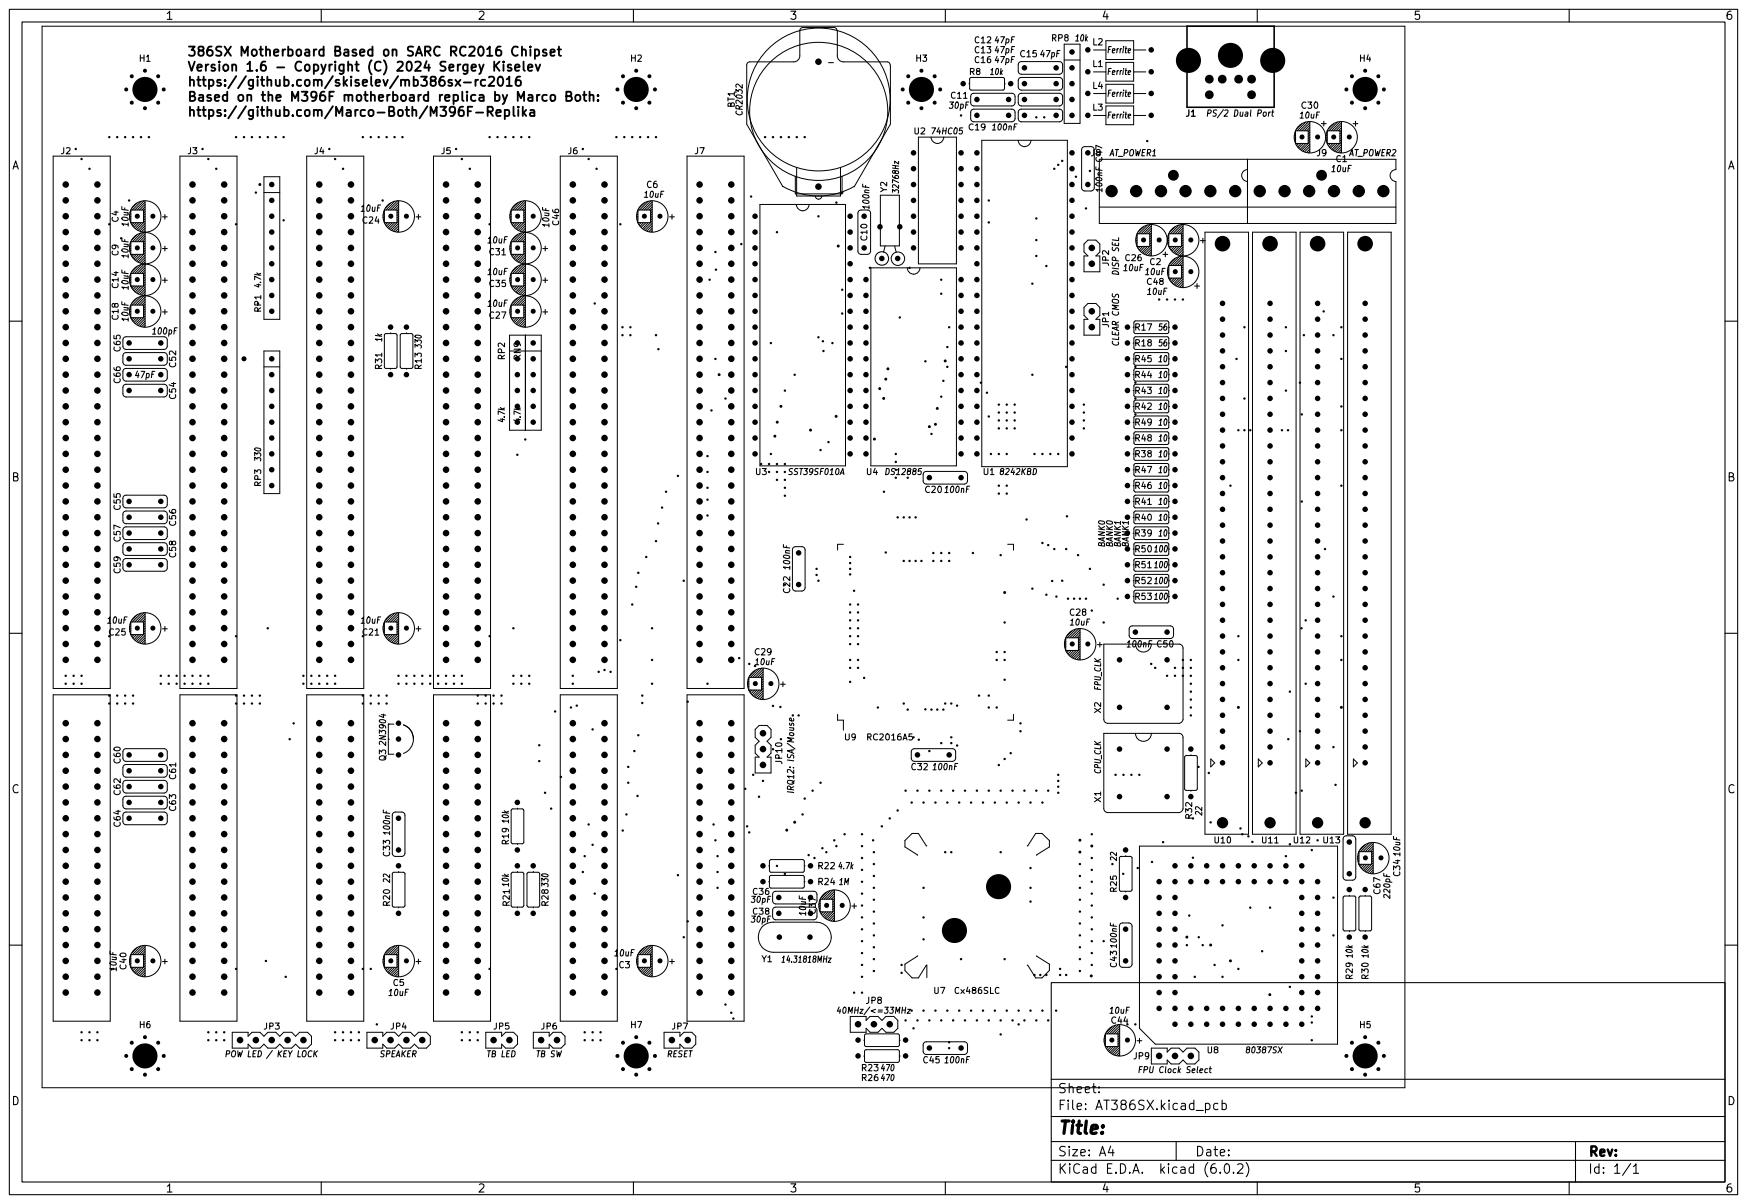
[picture p76: page 3]

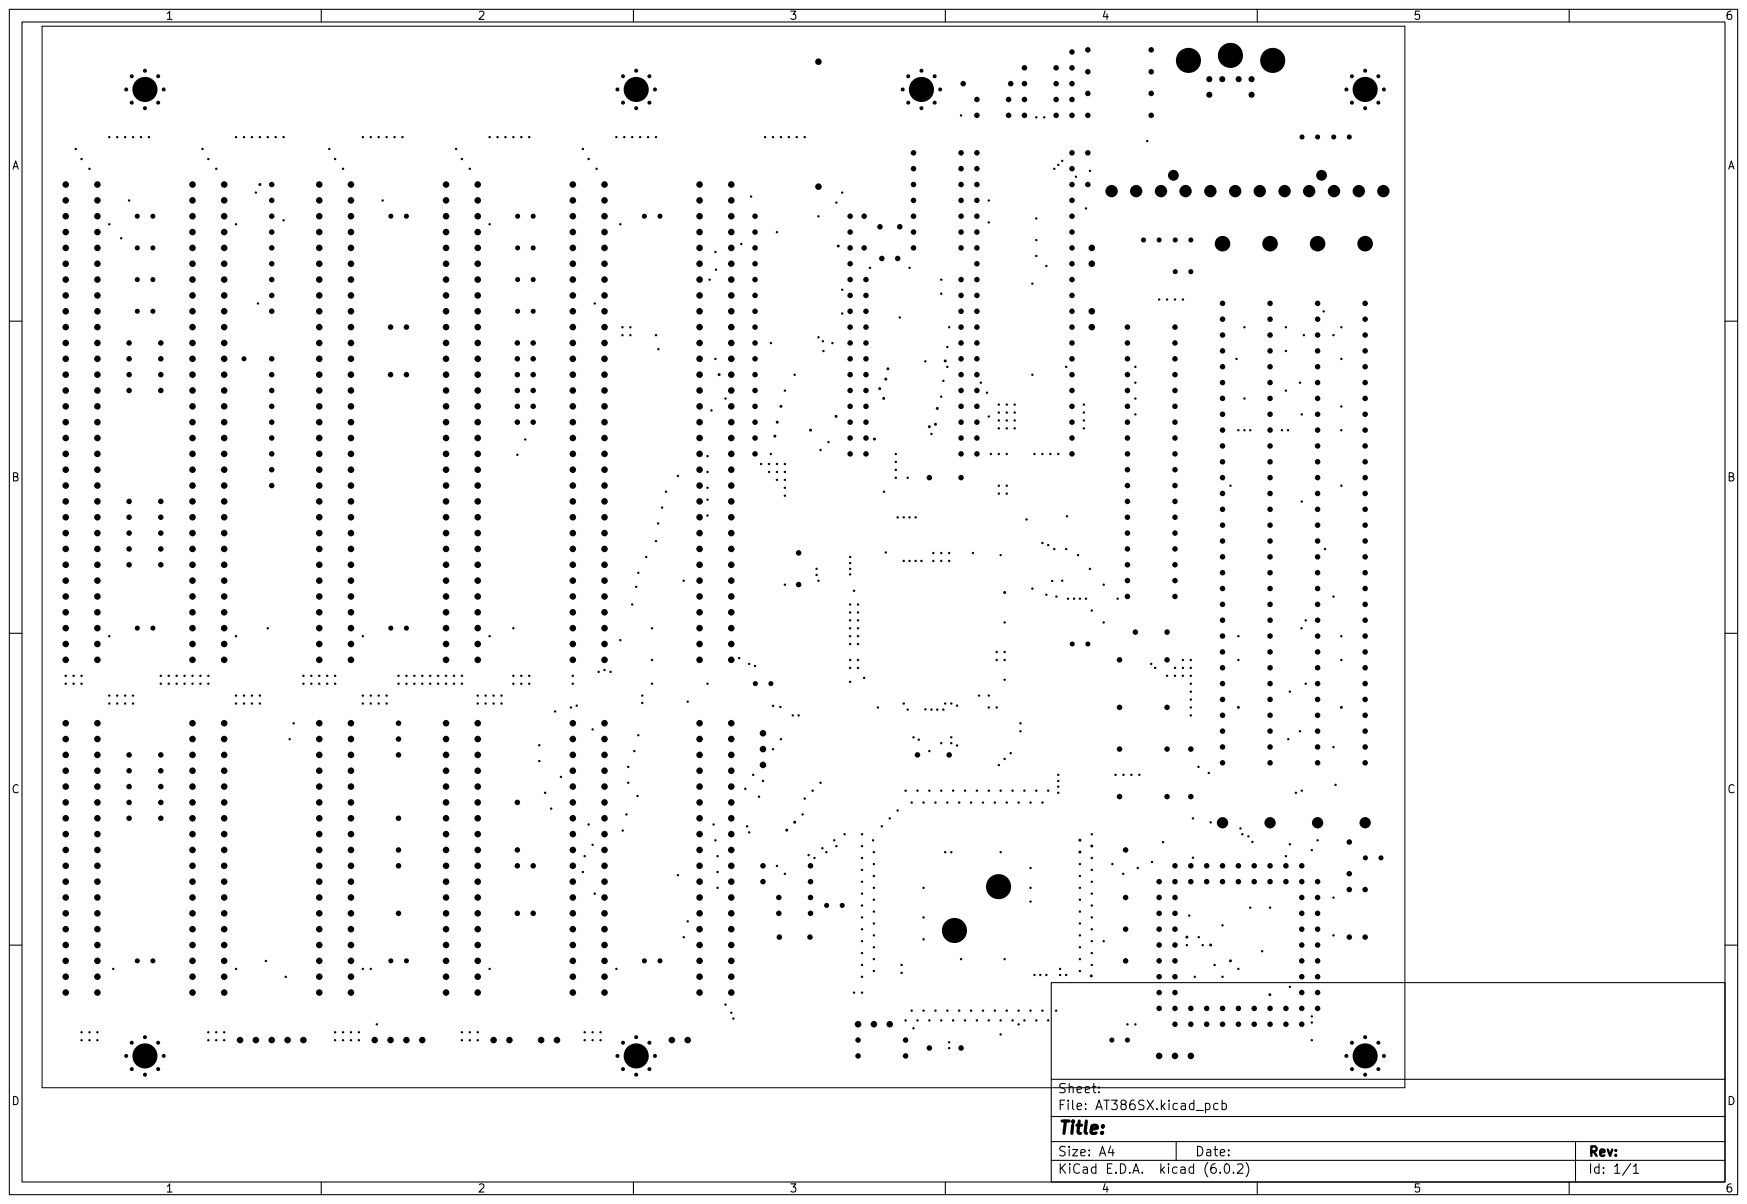
[picture p77: page 4]
