skiselev/mb386sx-rc2016/KiCad/AT386SX-Board-1.5.pdf

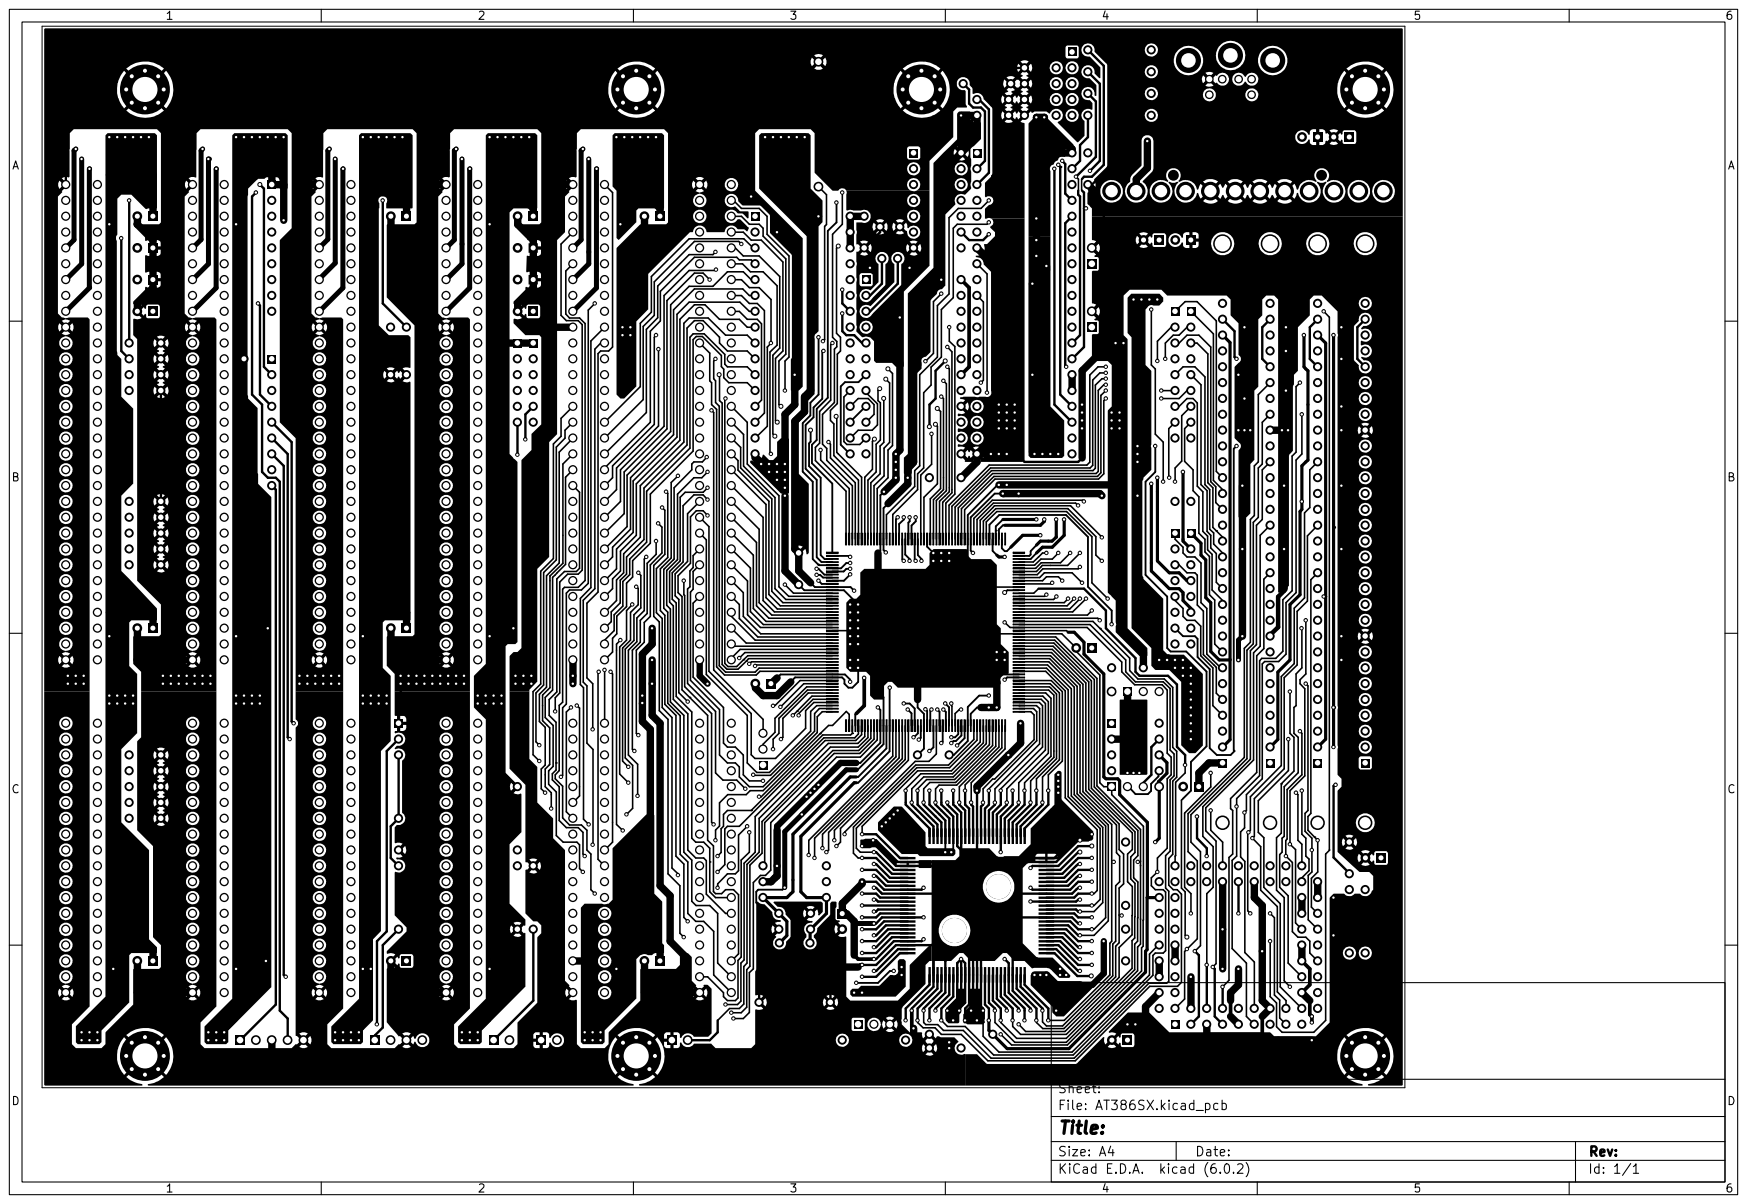
[picture p78: page 1]

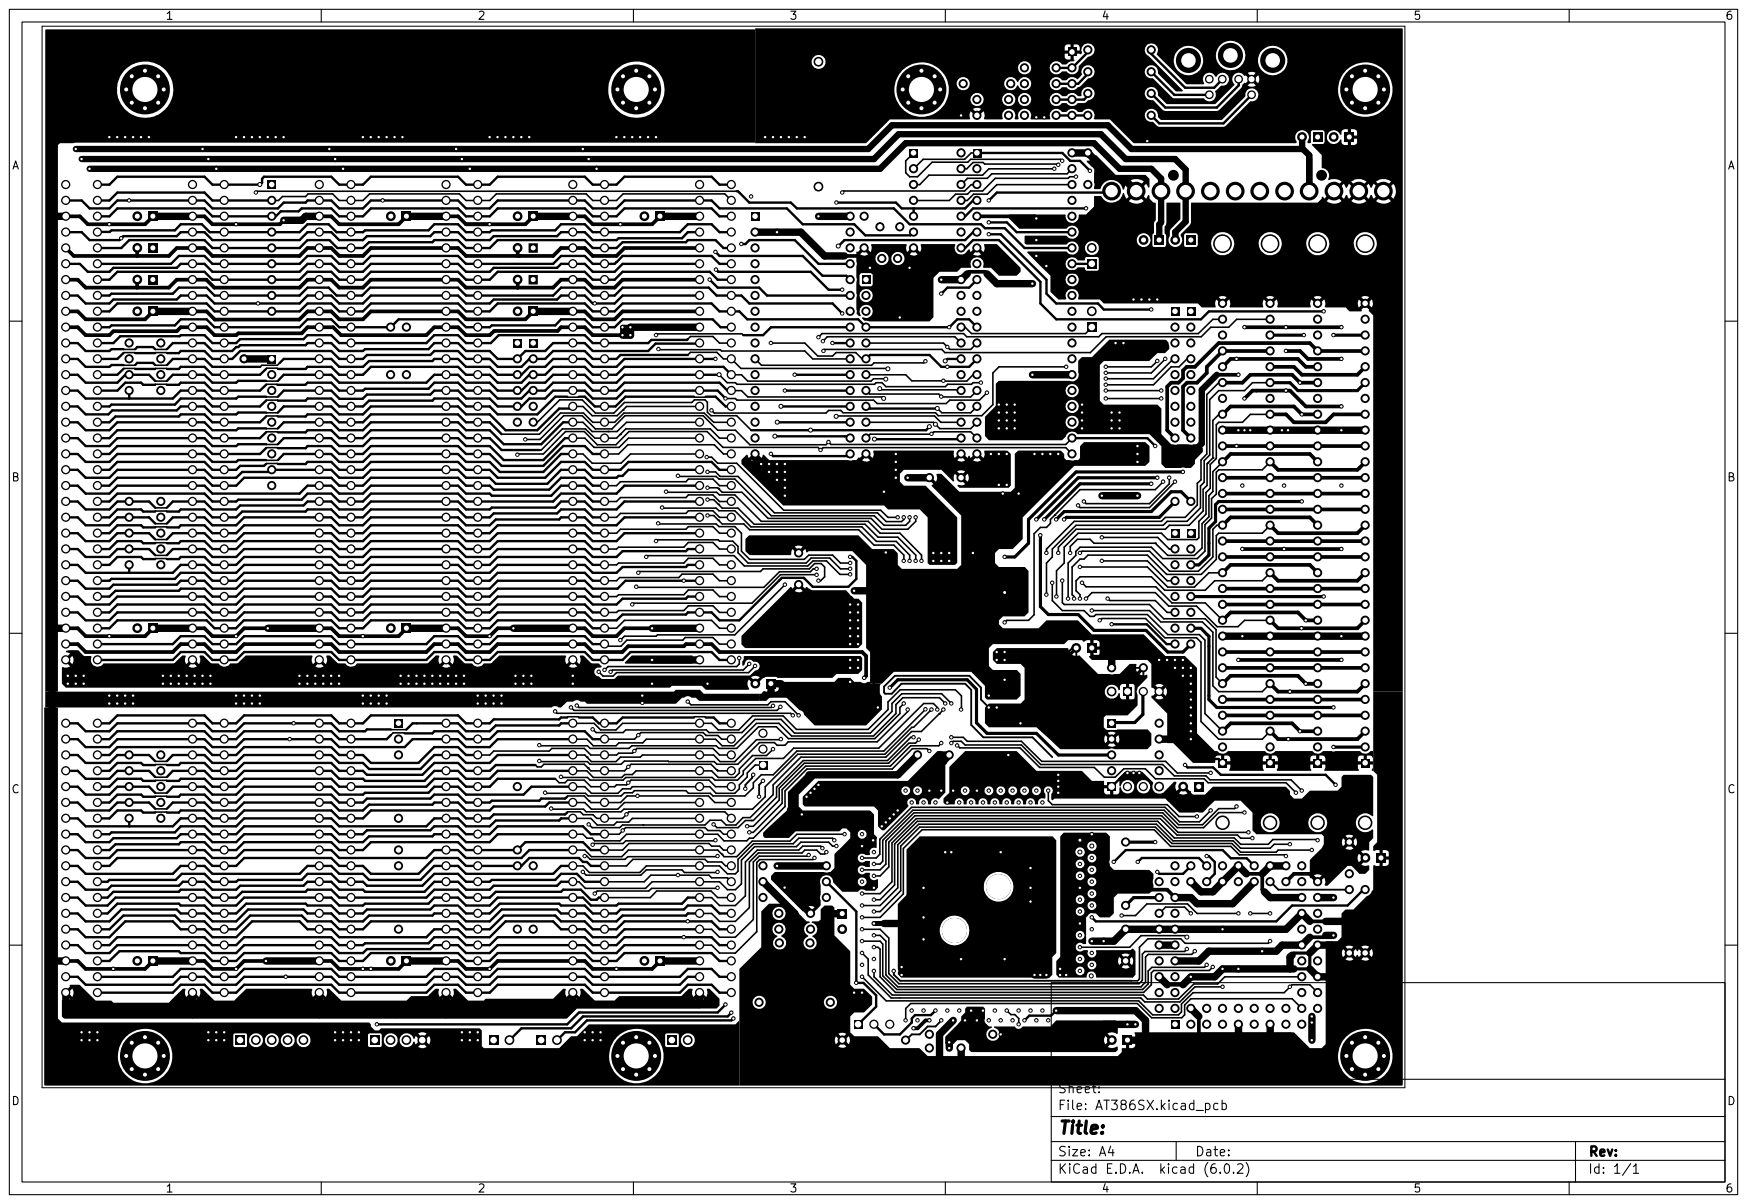
[picture p79: page 2]

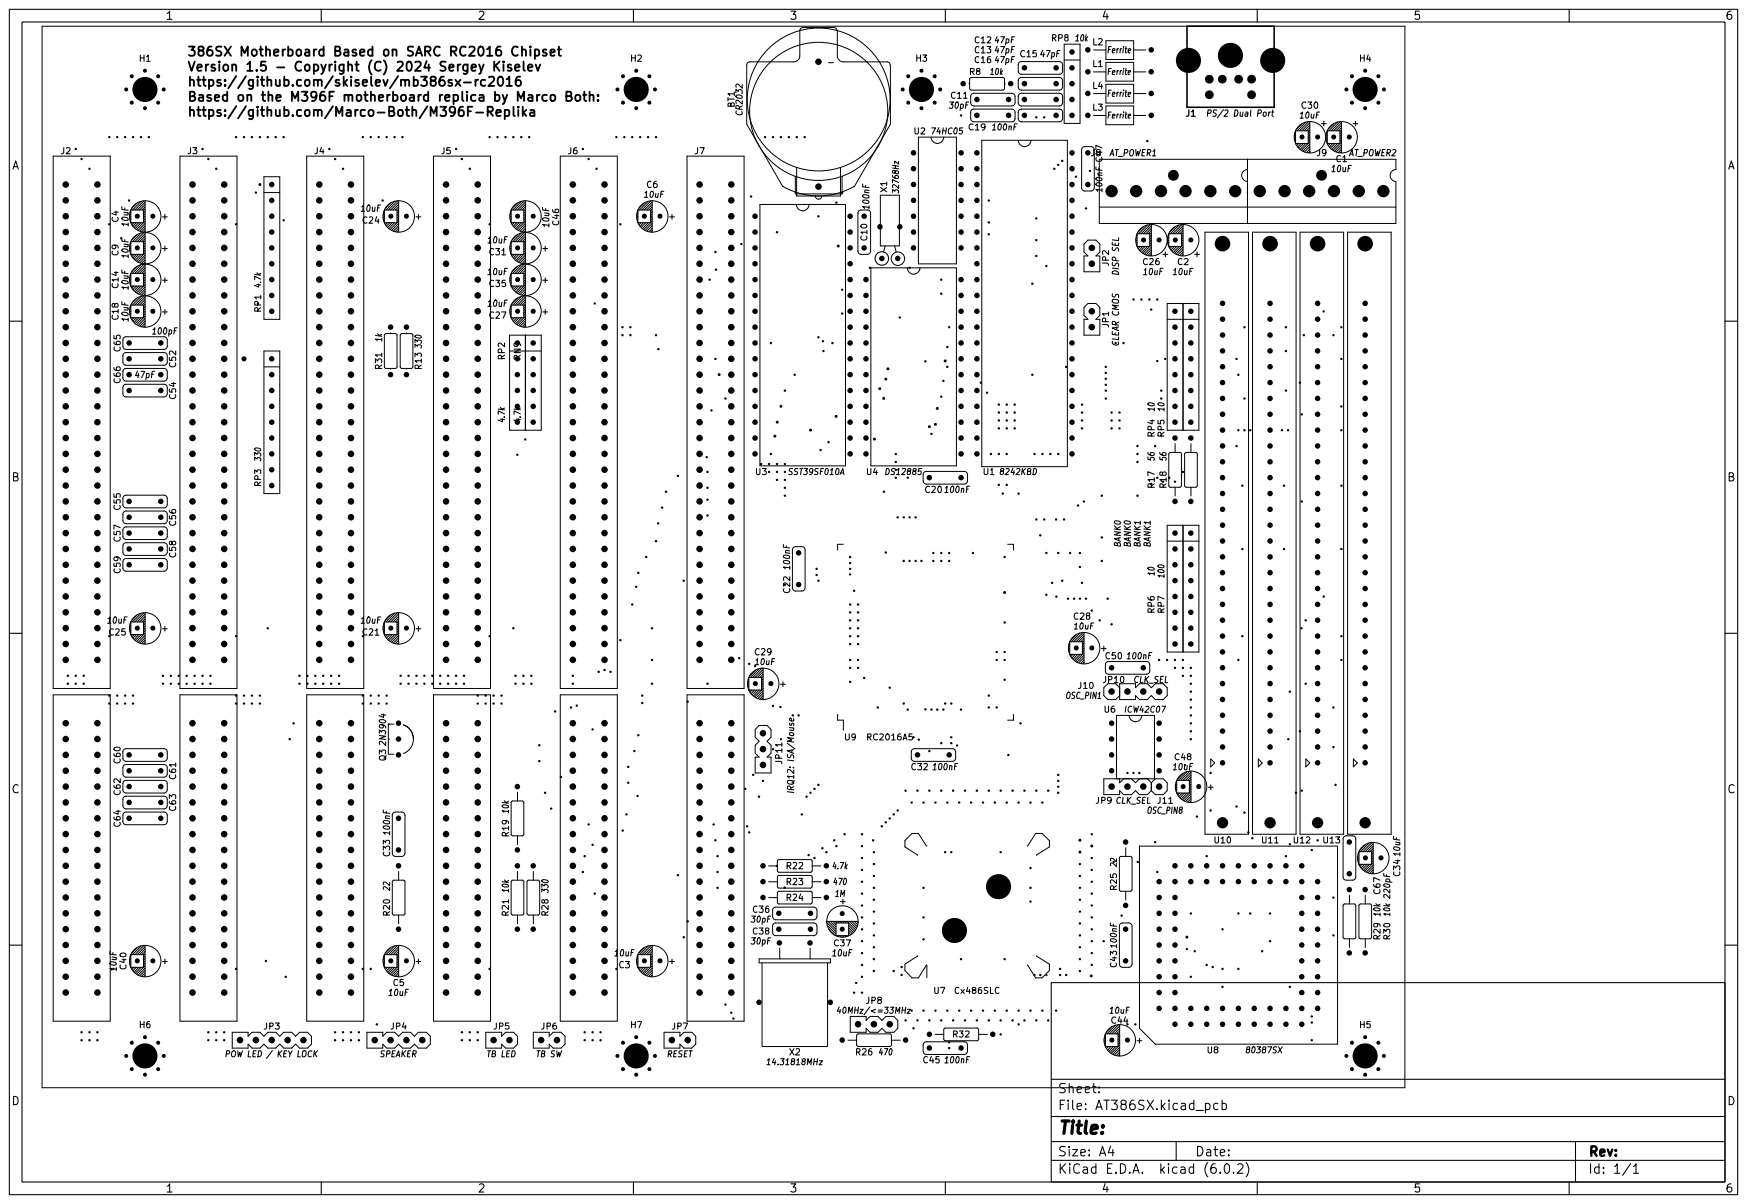
[picture p80: page 3]

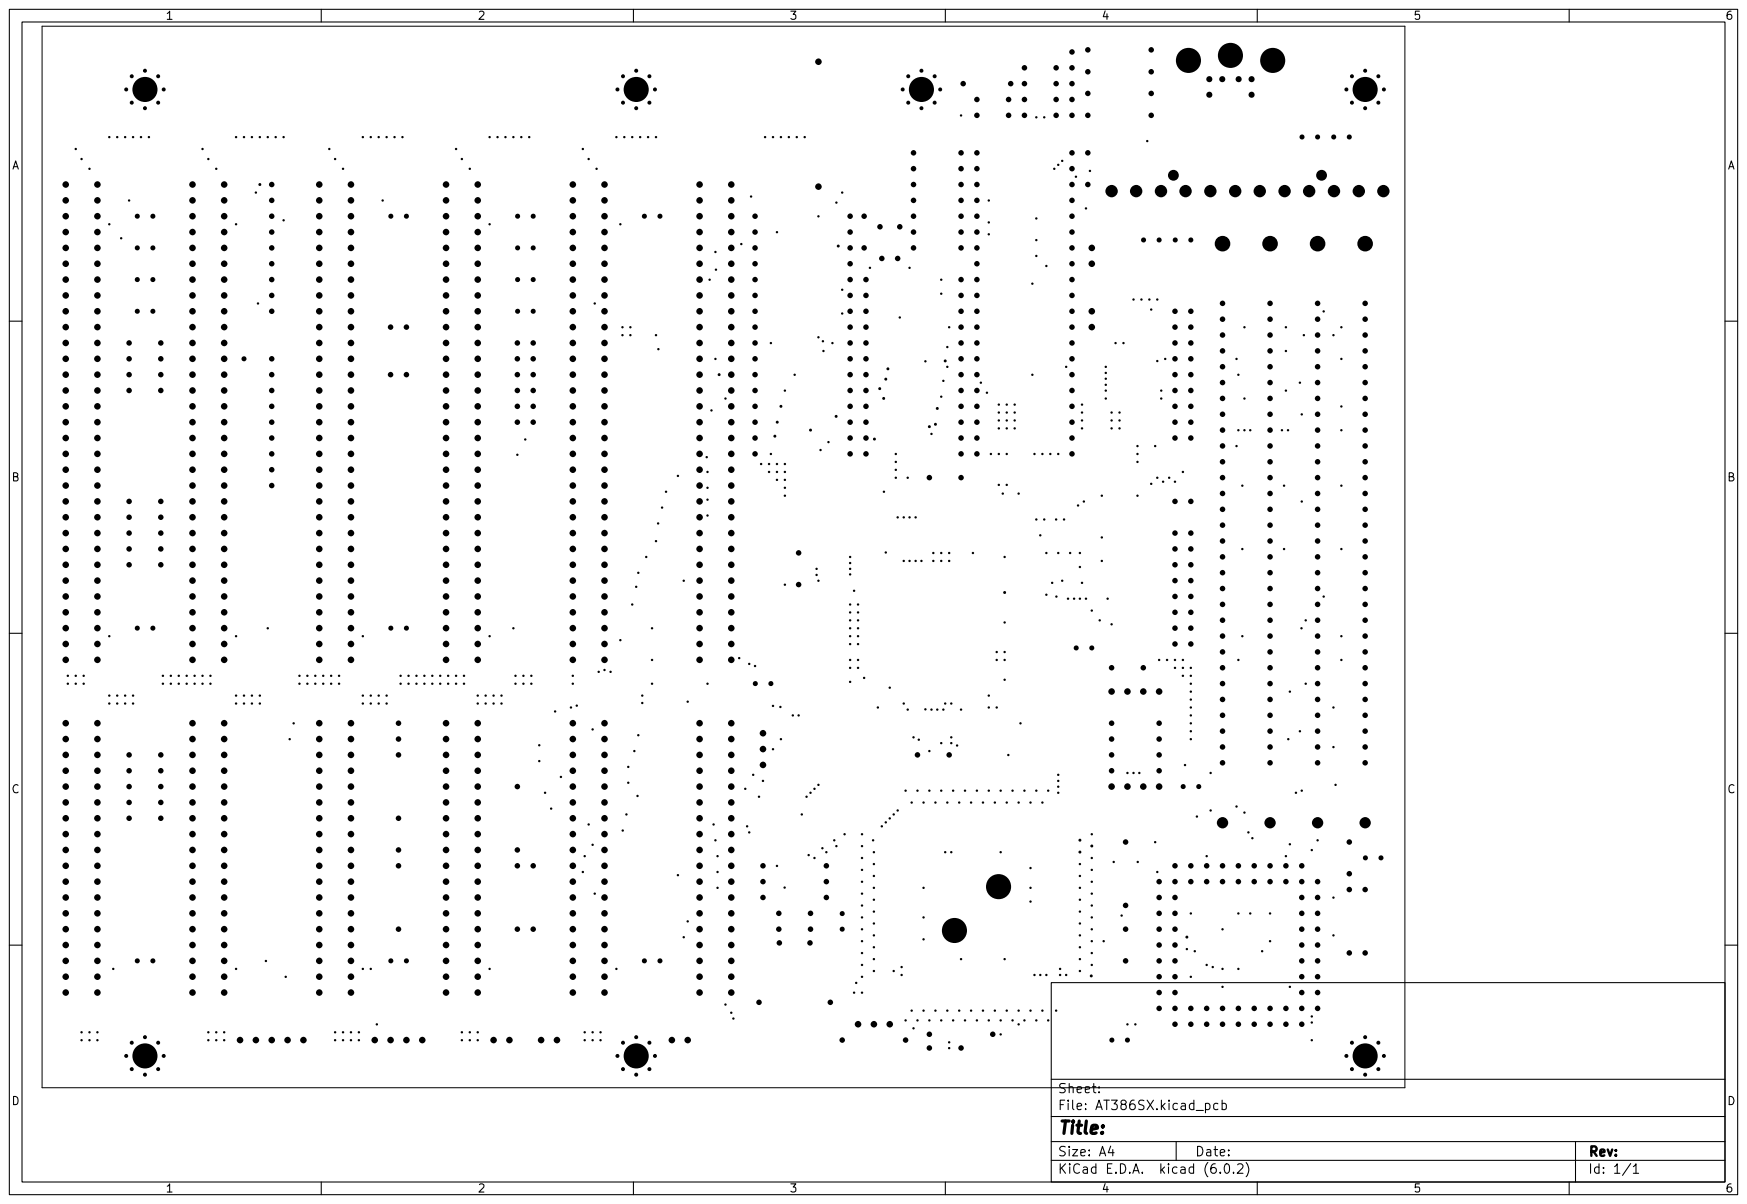
[picture p81: page 4]
