skiselev/mb386sx-rc2016/KiCad/AT386SX-Board-1.4.pdf

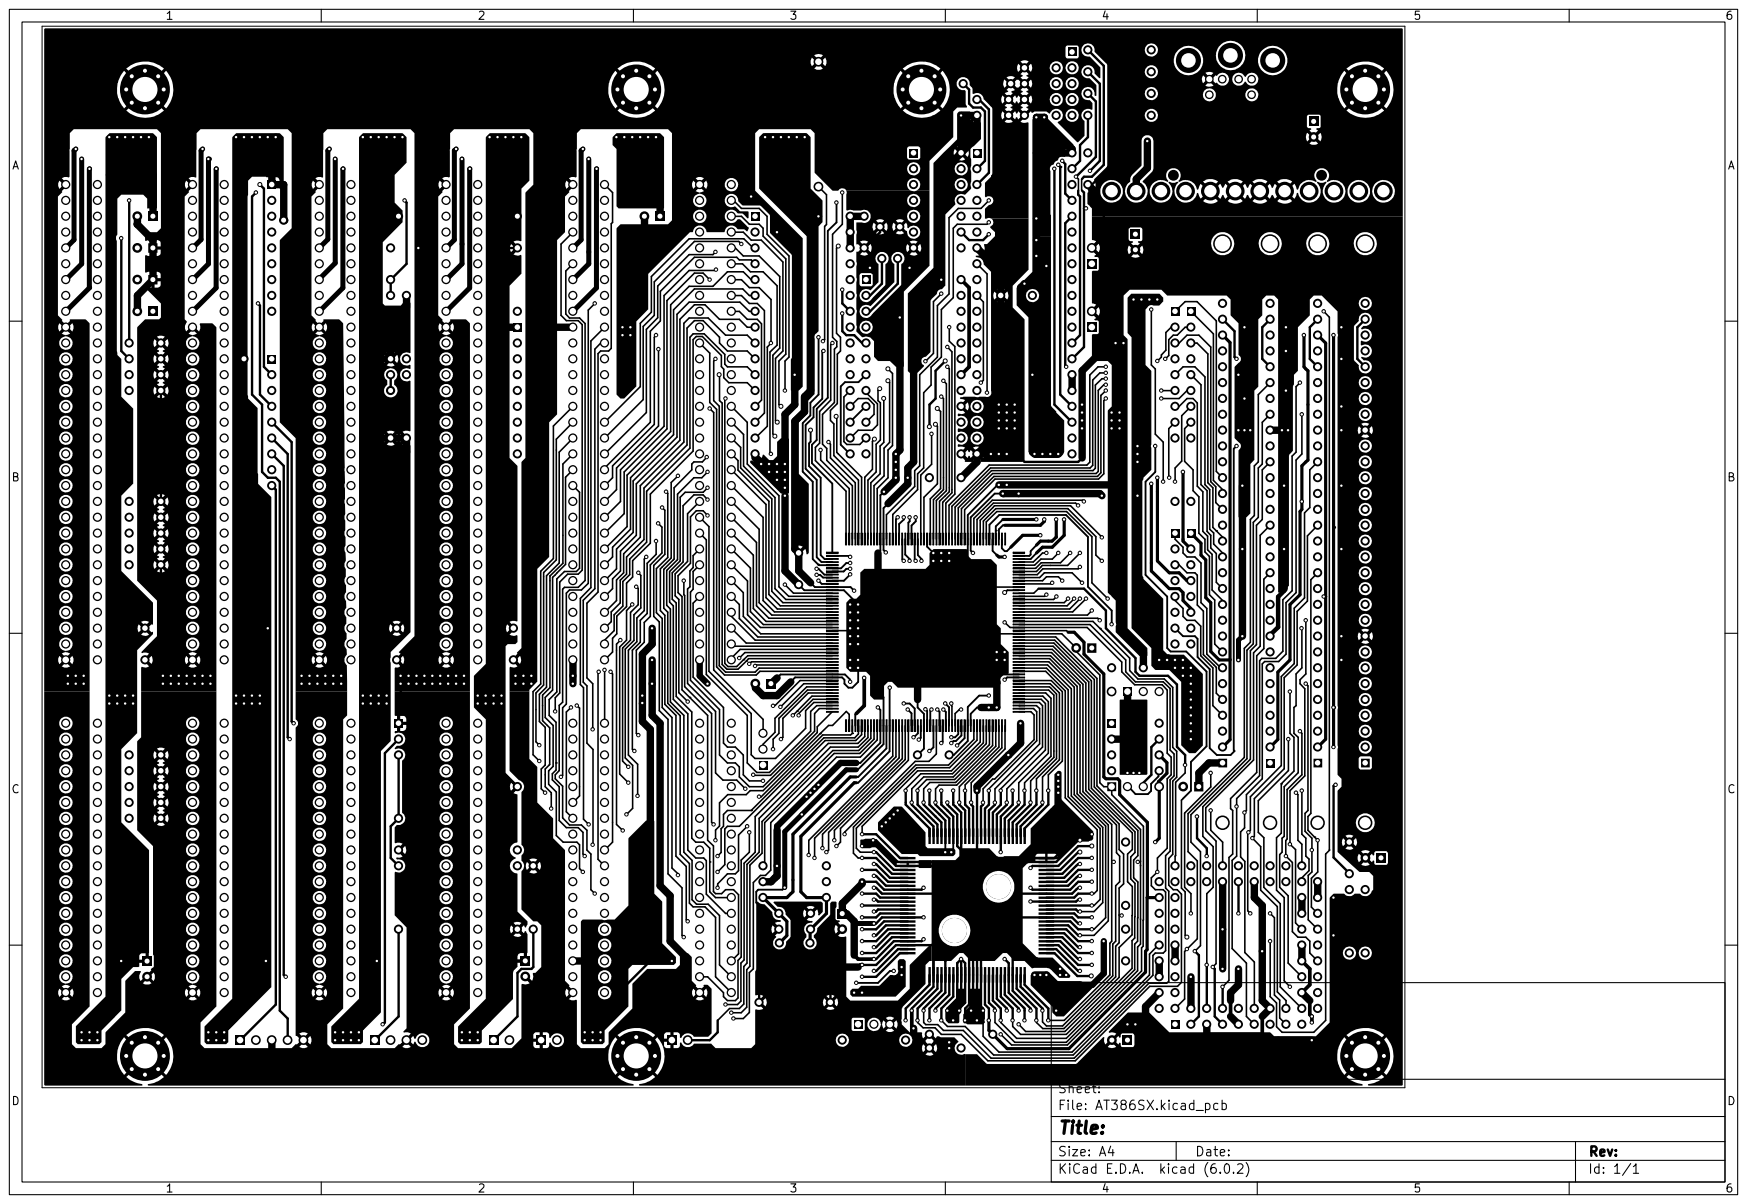
[picture p82: page 1]

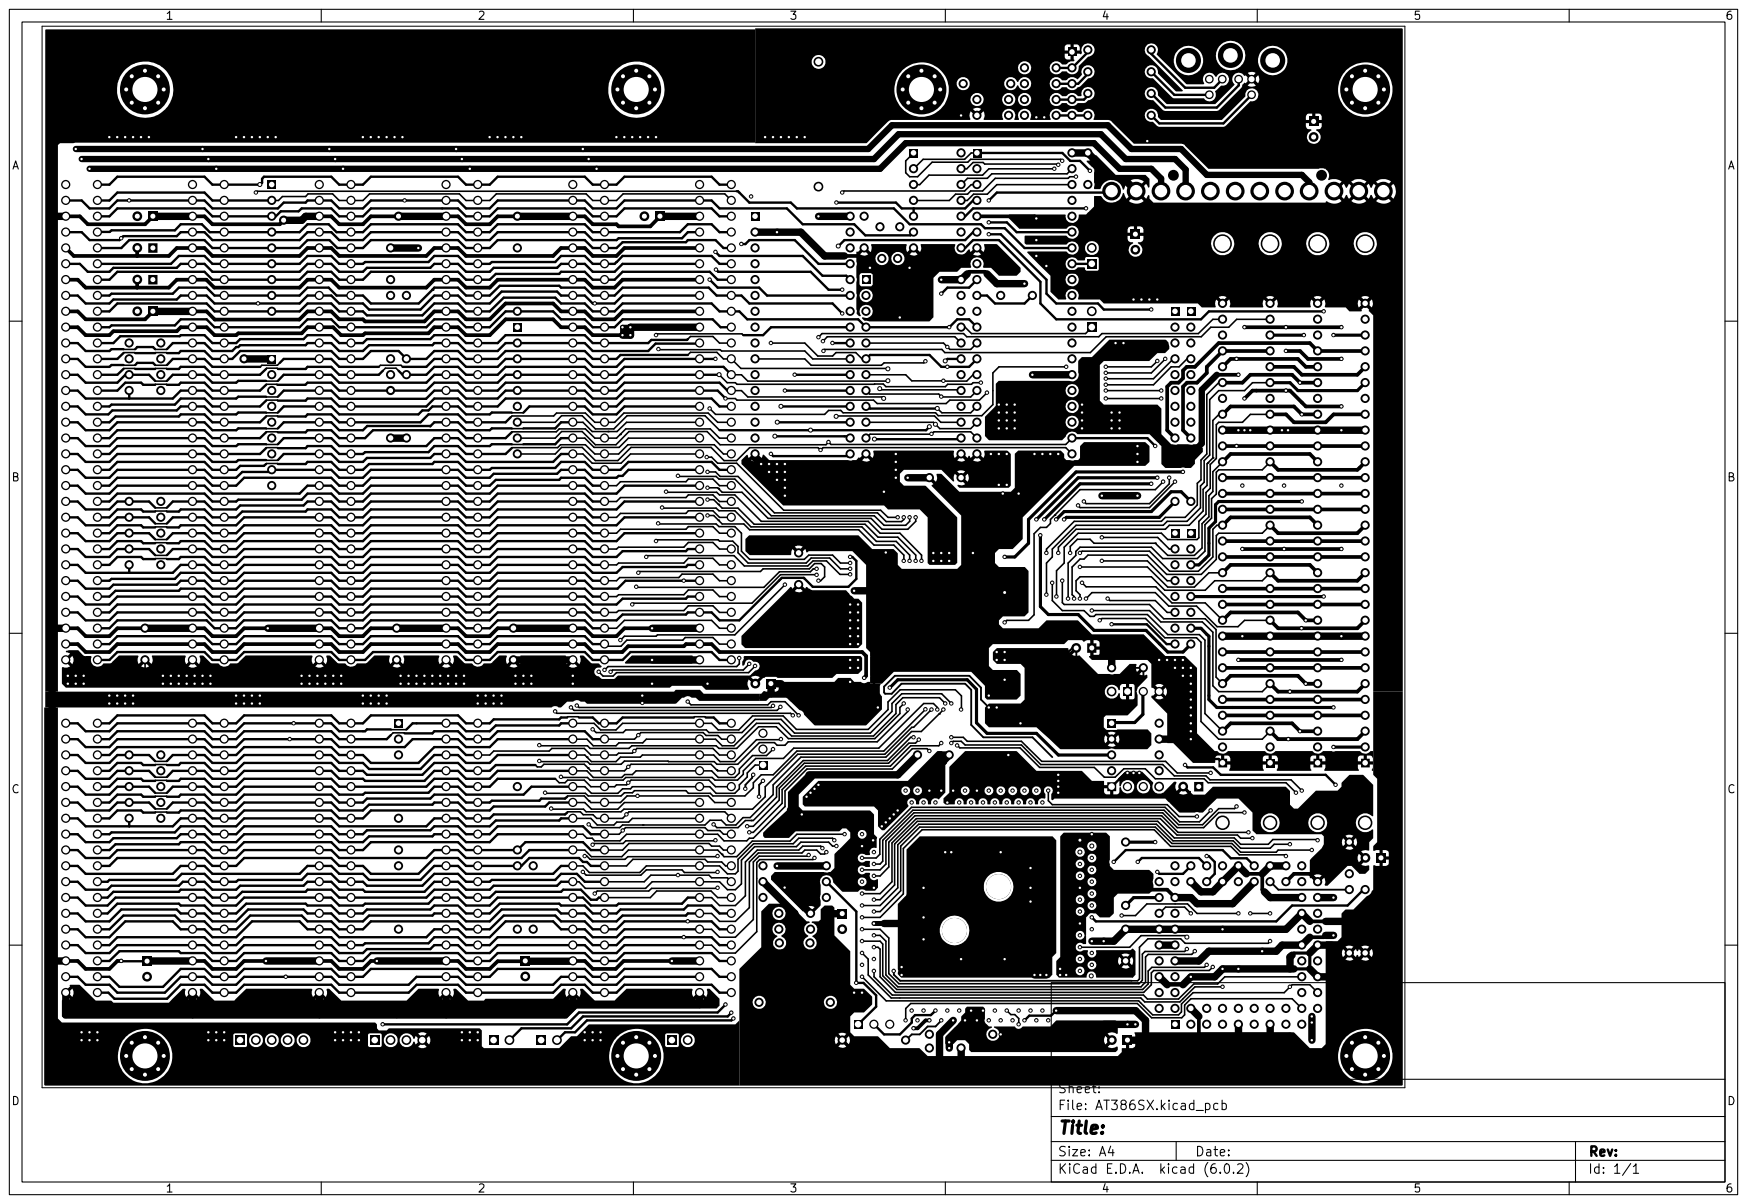
[picture p83: page 2]

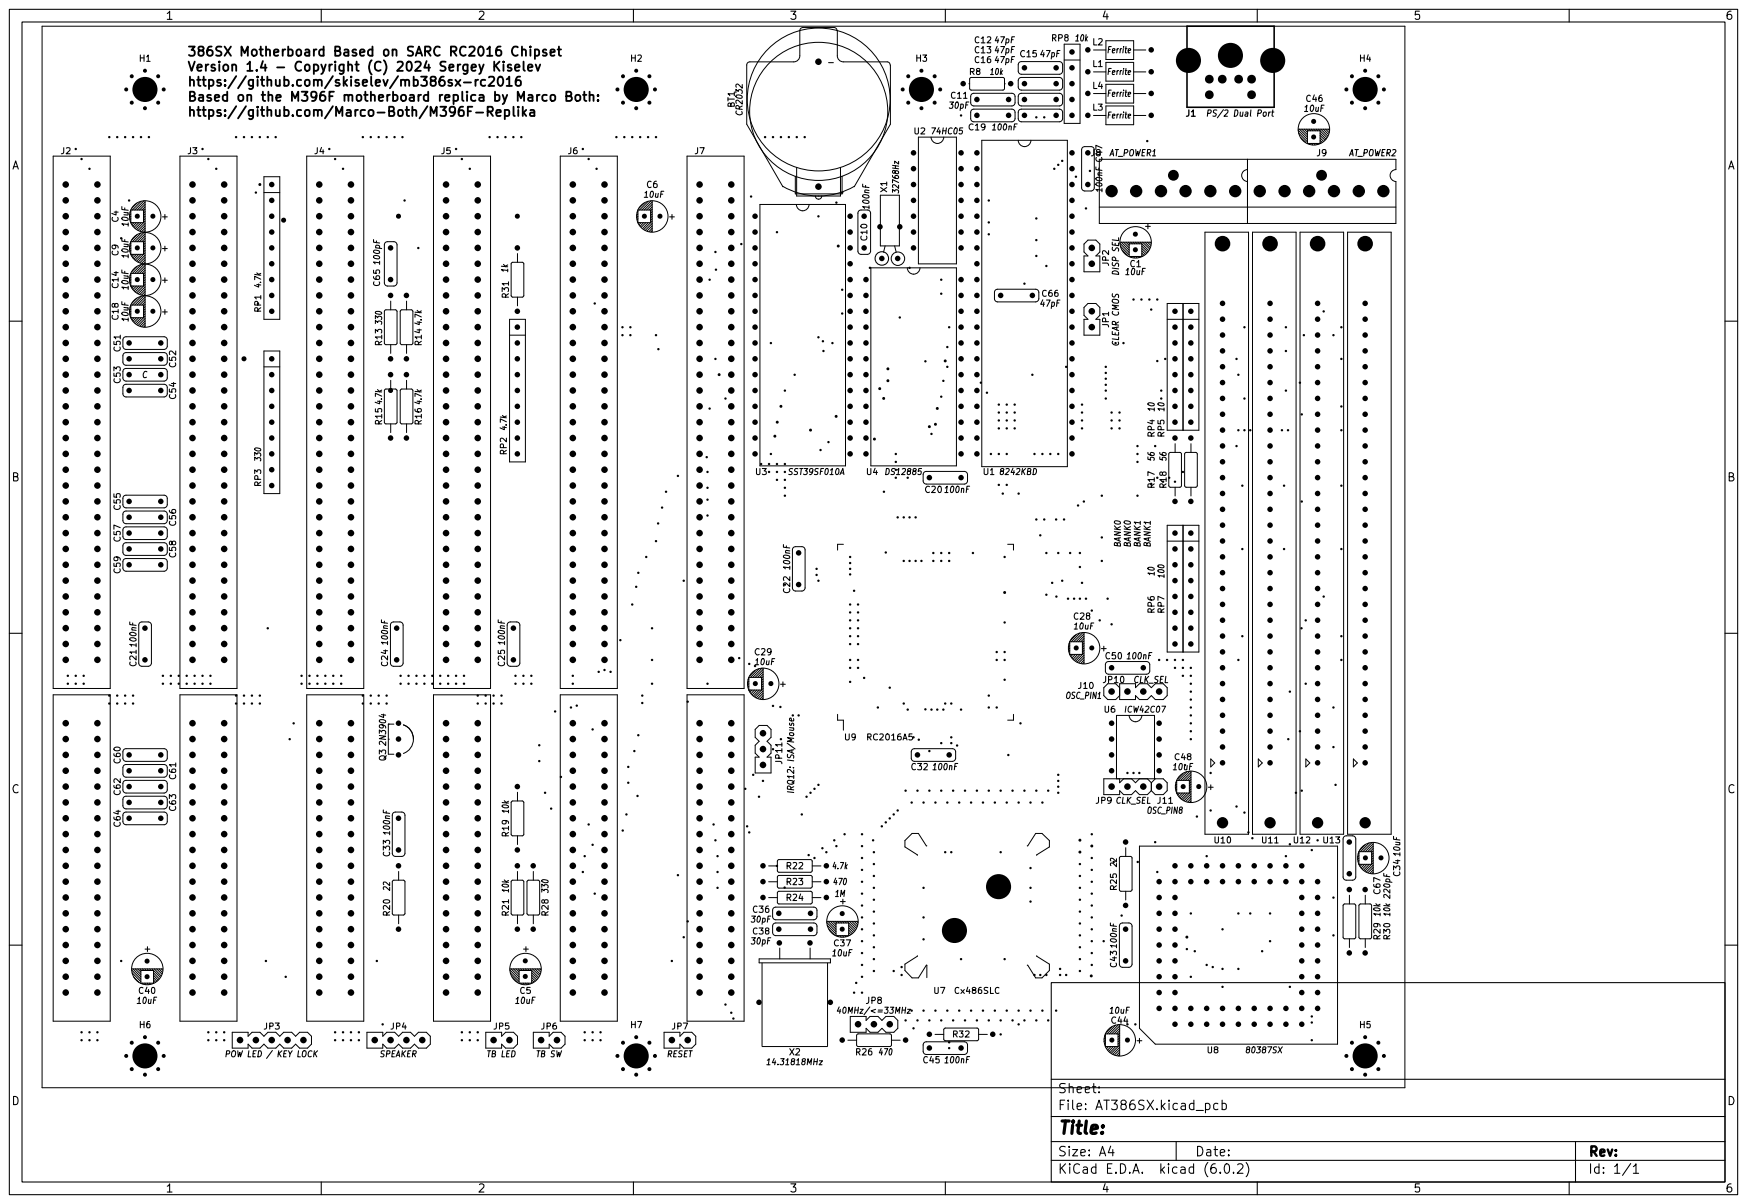
[picture p84: page 3]

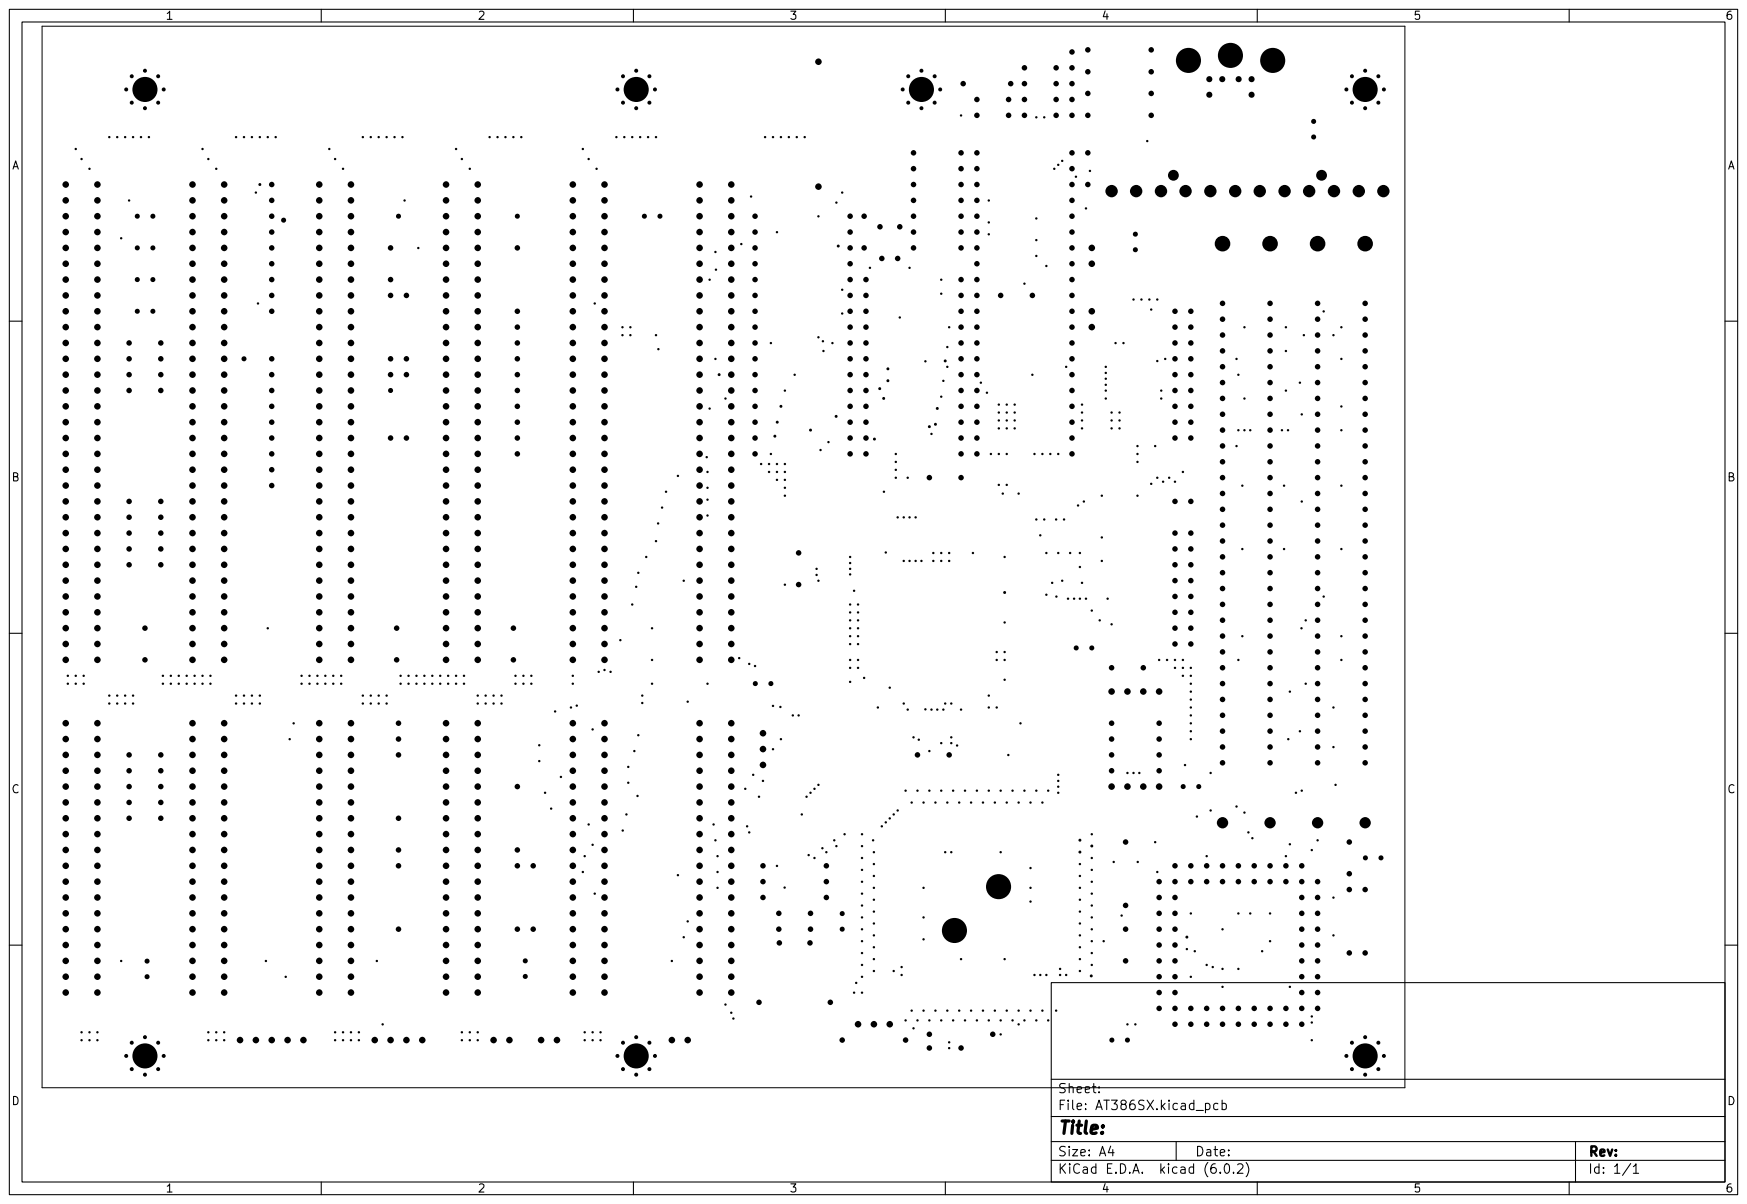
[picture p85: page 4]
