skiselev/mb386sx-rc2016/KiCad/AT386SX-Board-1.3.pdf

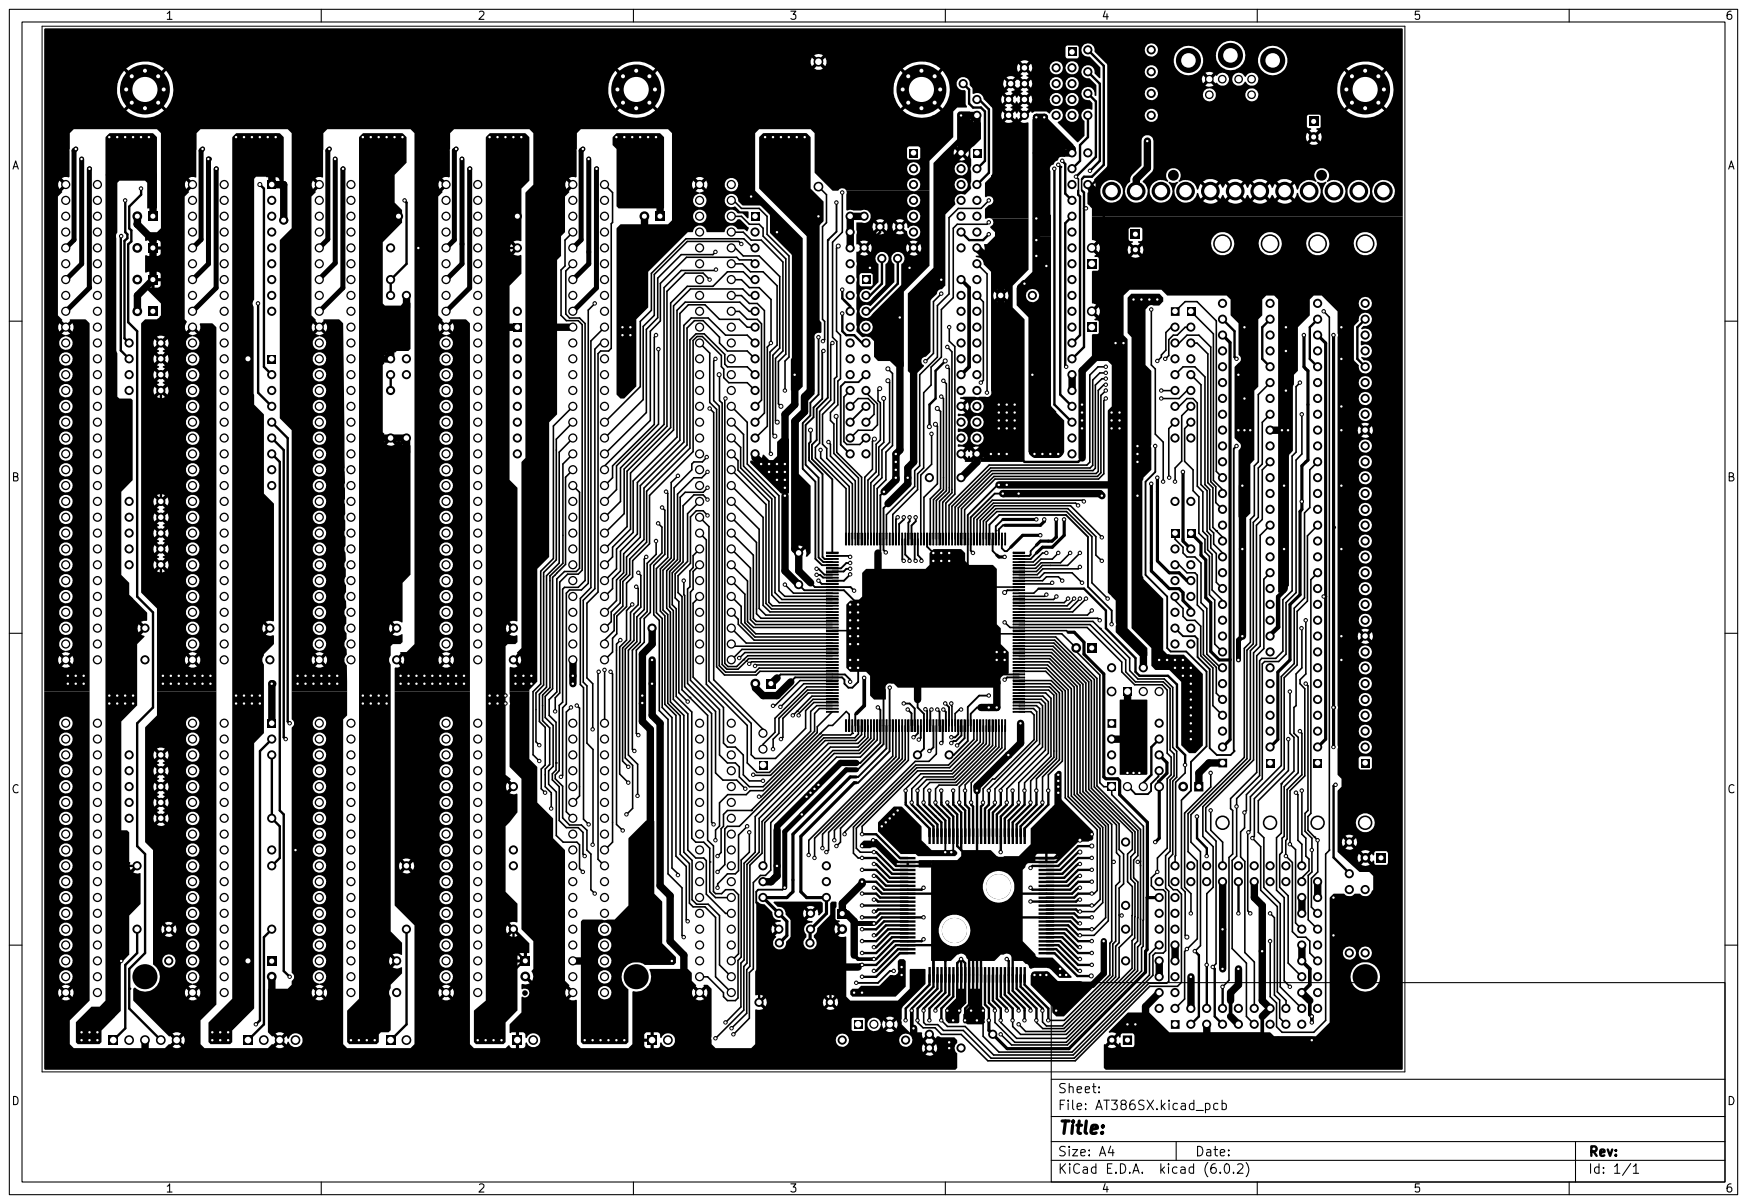
[picture p86: page 1]

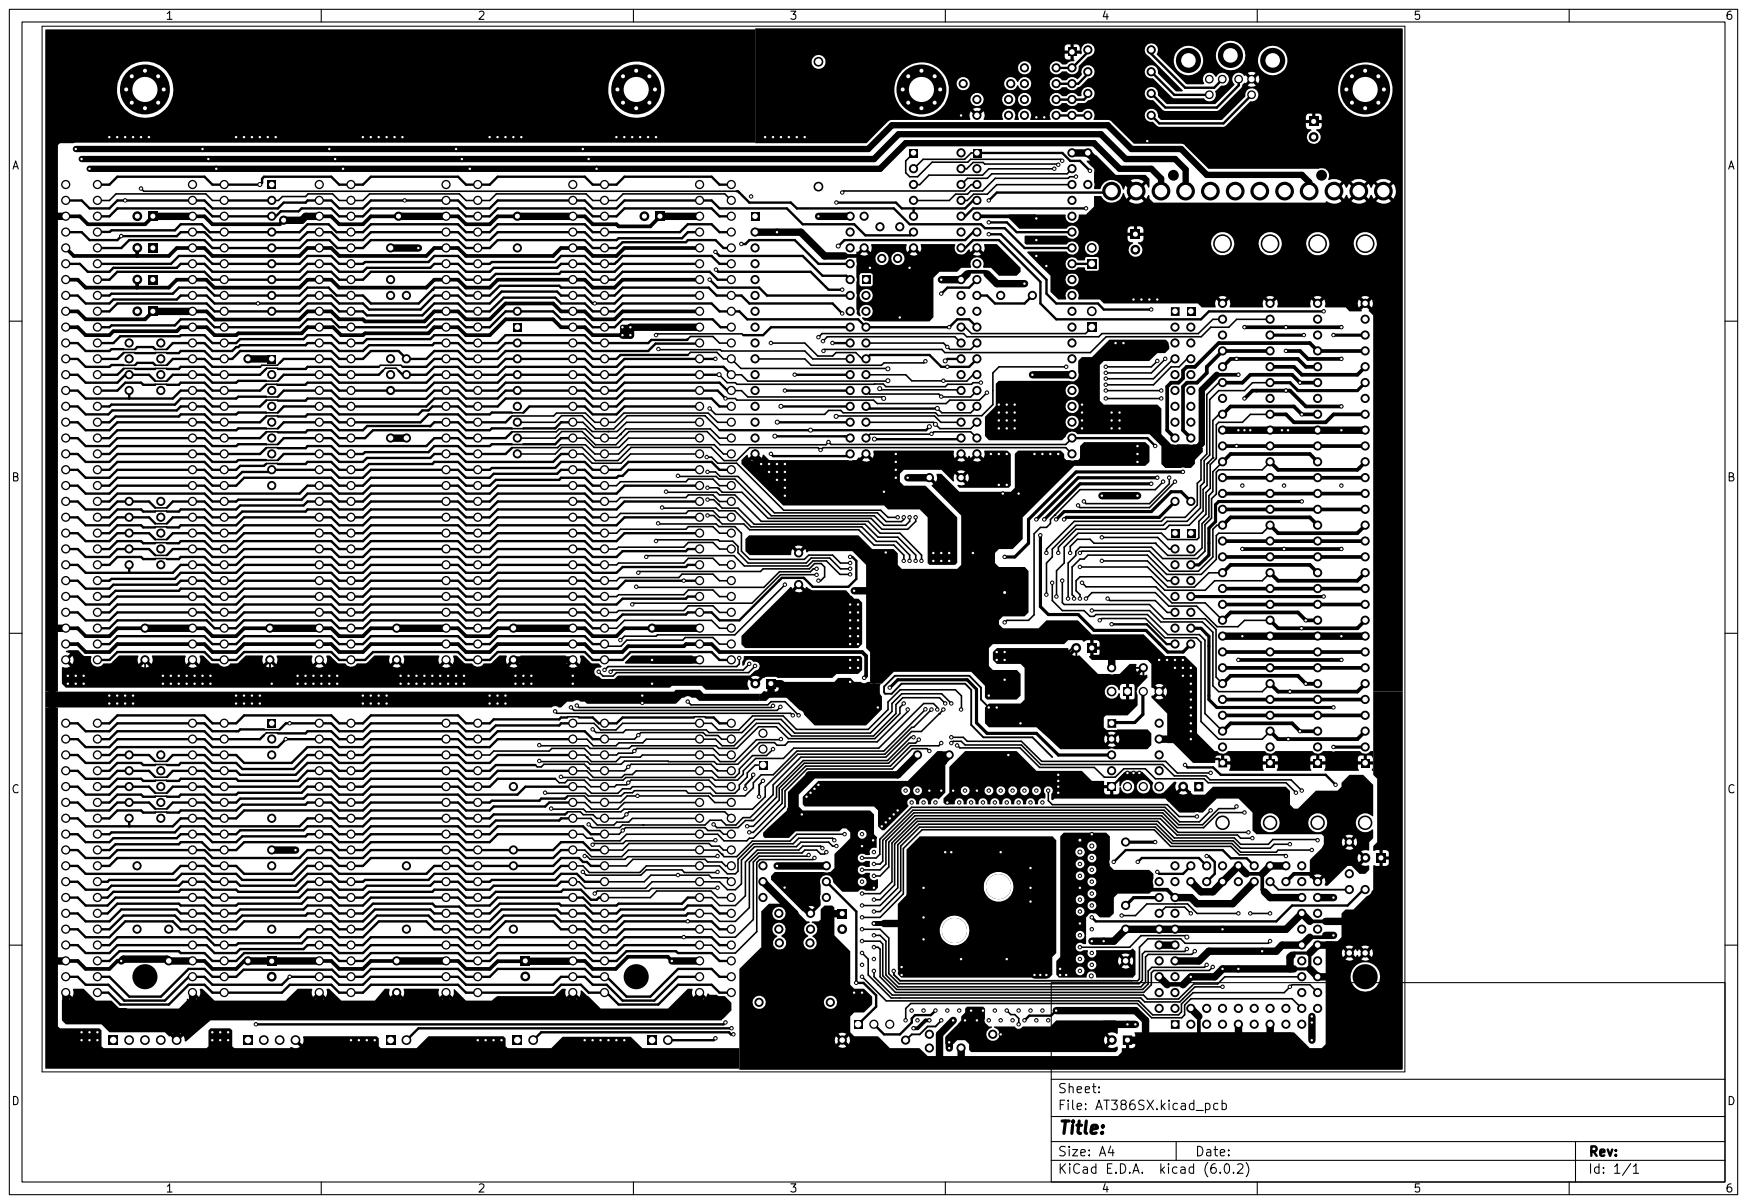
[picture p87: page 2]

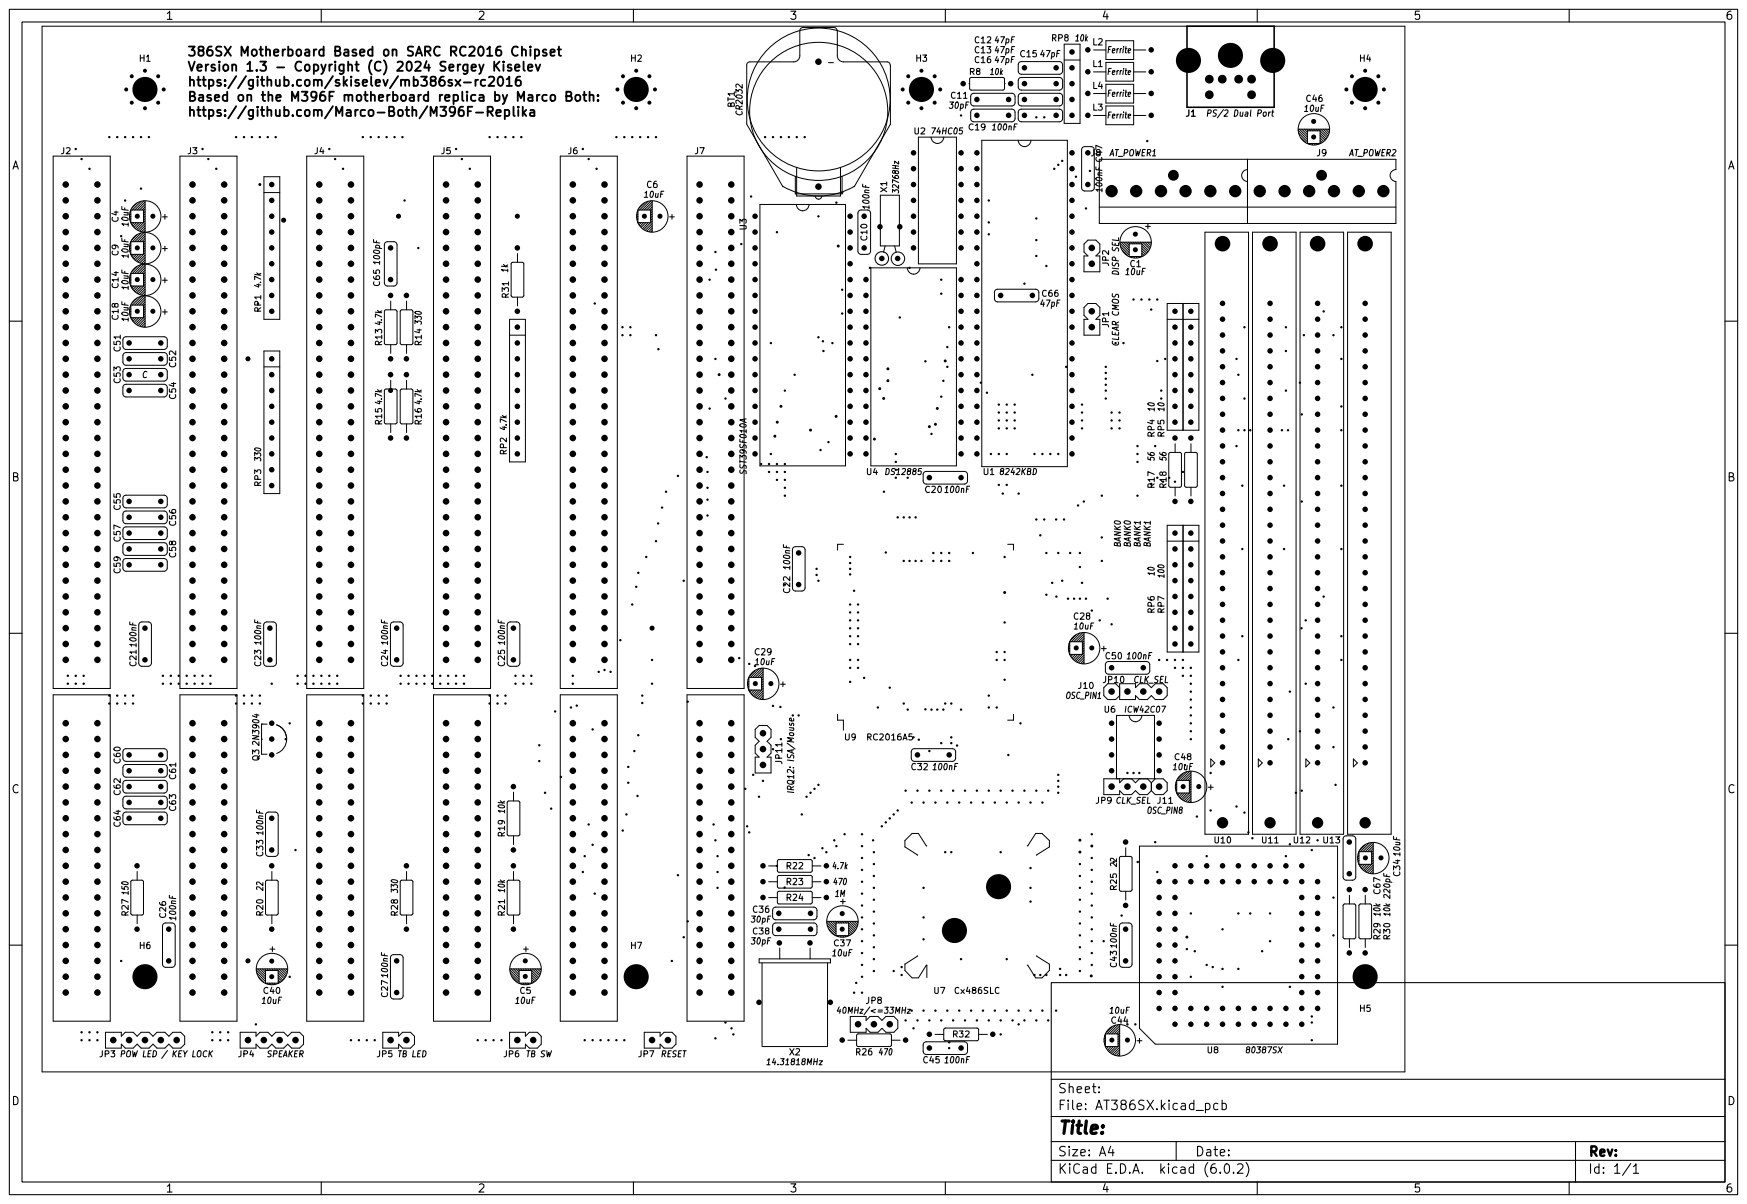
[picture p88: page 3]

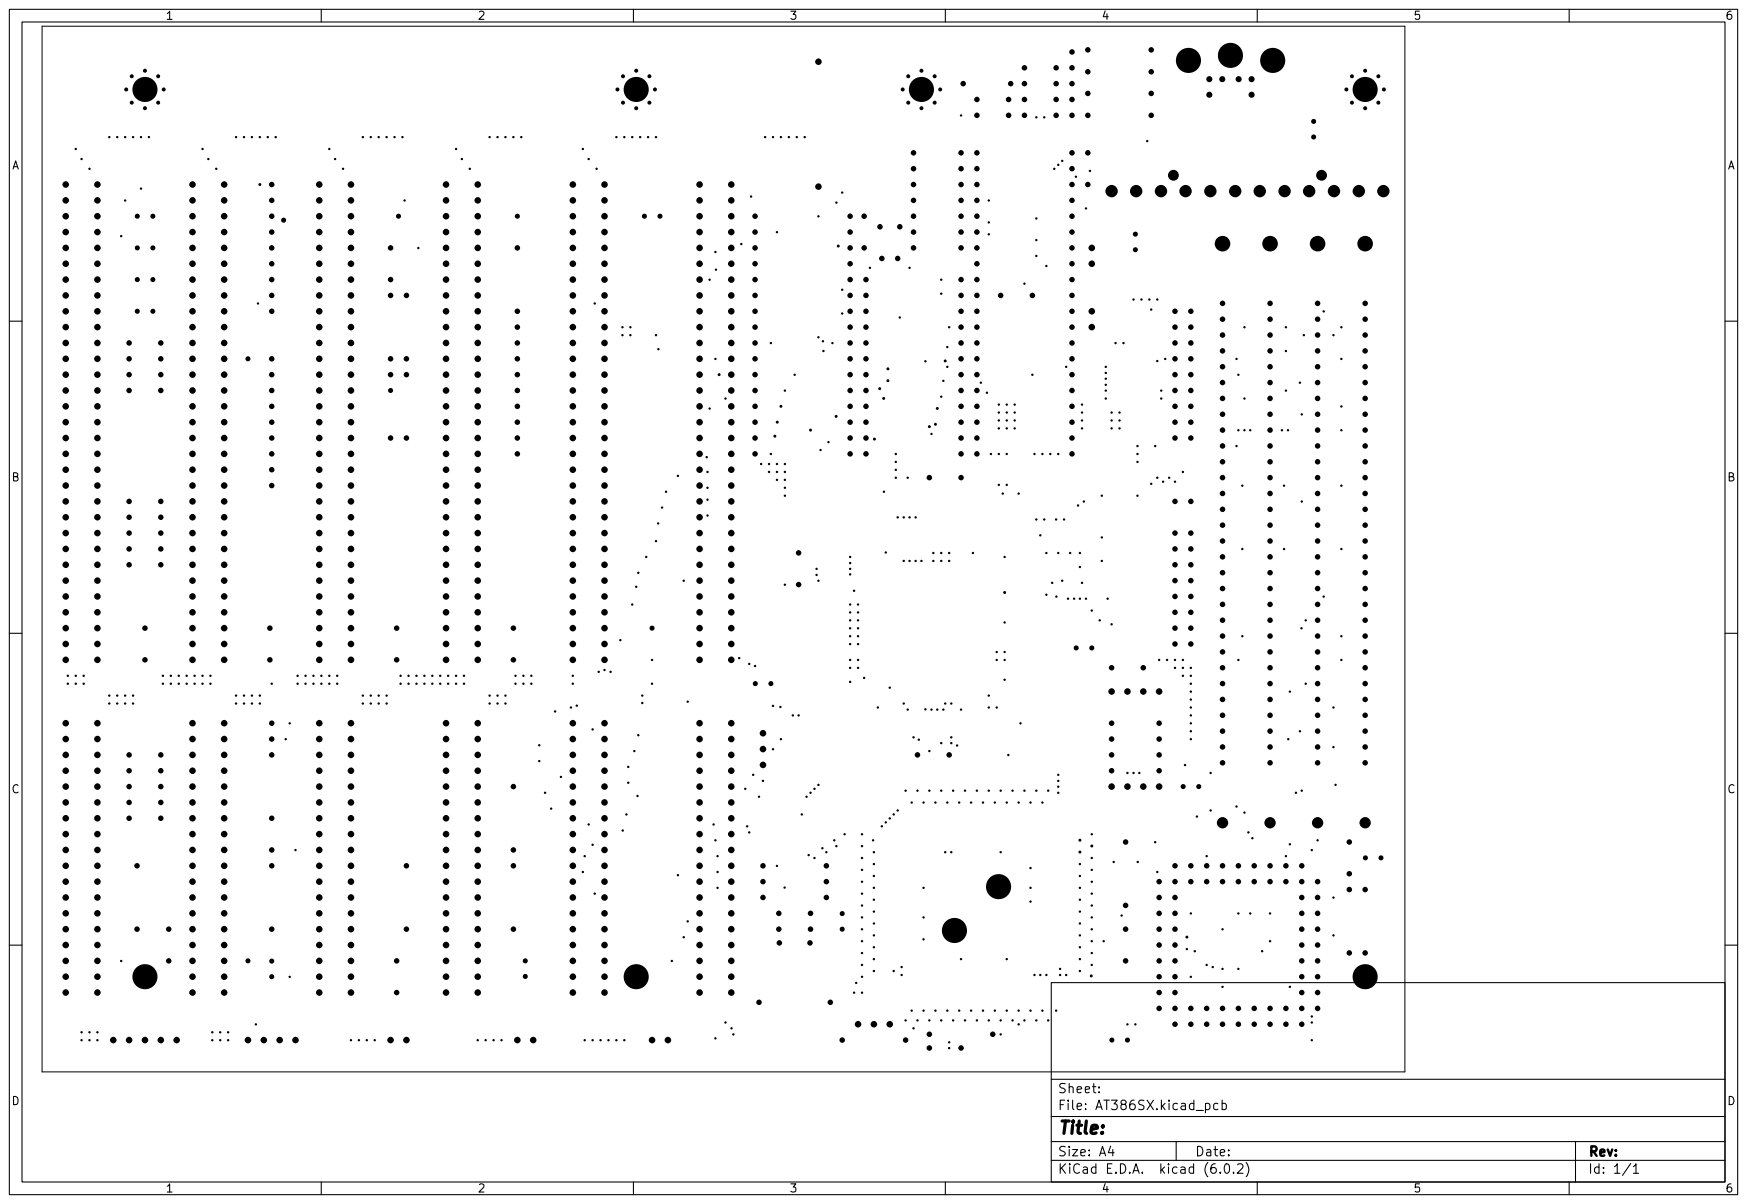
[picture p89: page 4]
