skiselev/mb386sx-rc2016/KiCad/AT386SX-Board-1.2.pdf

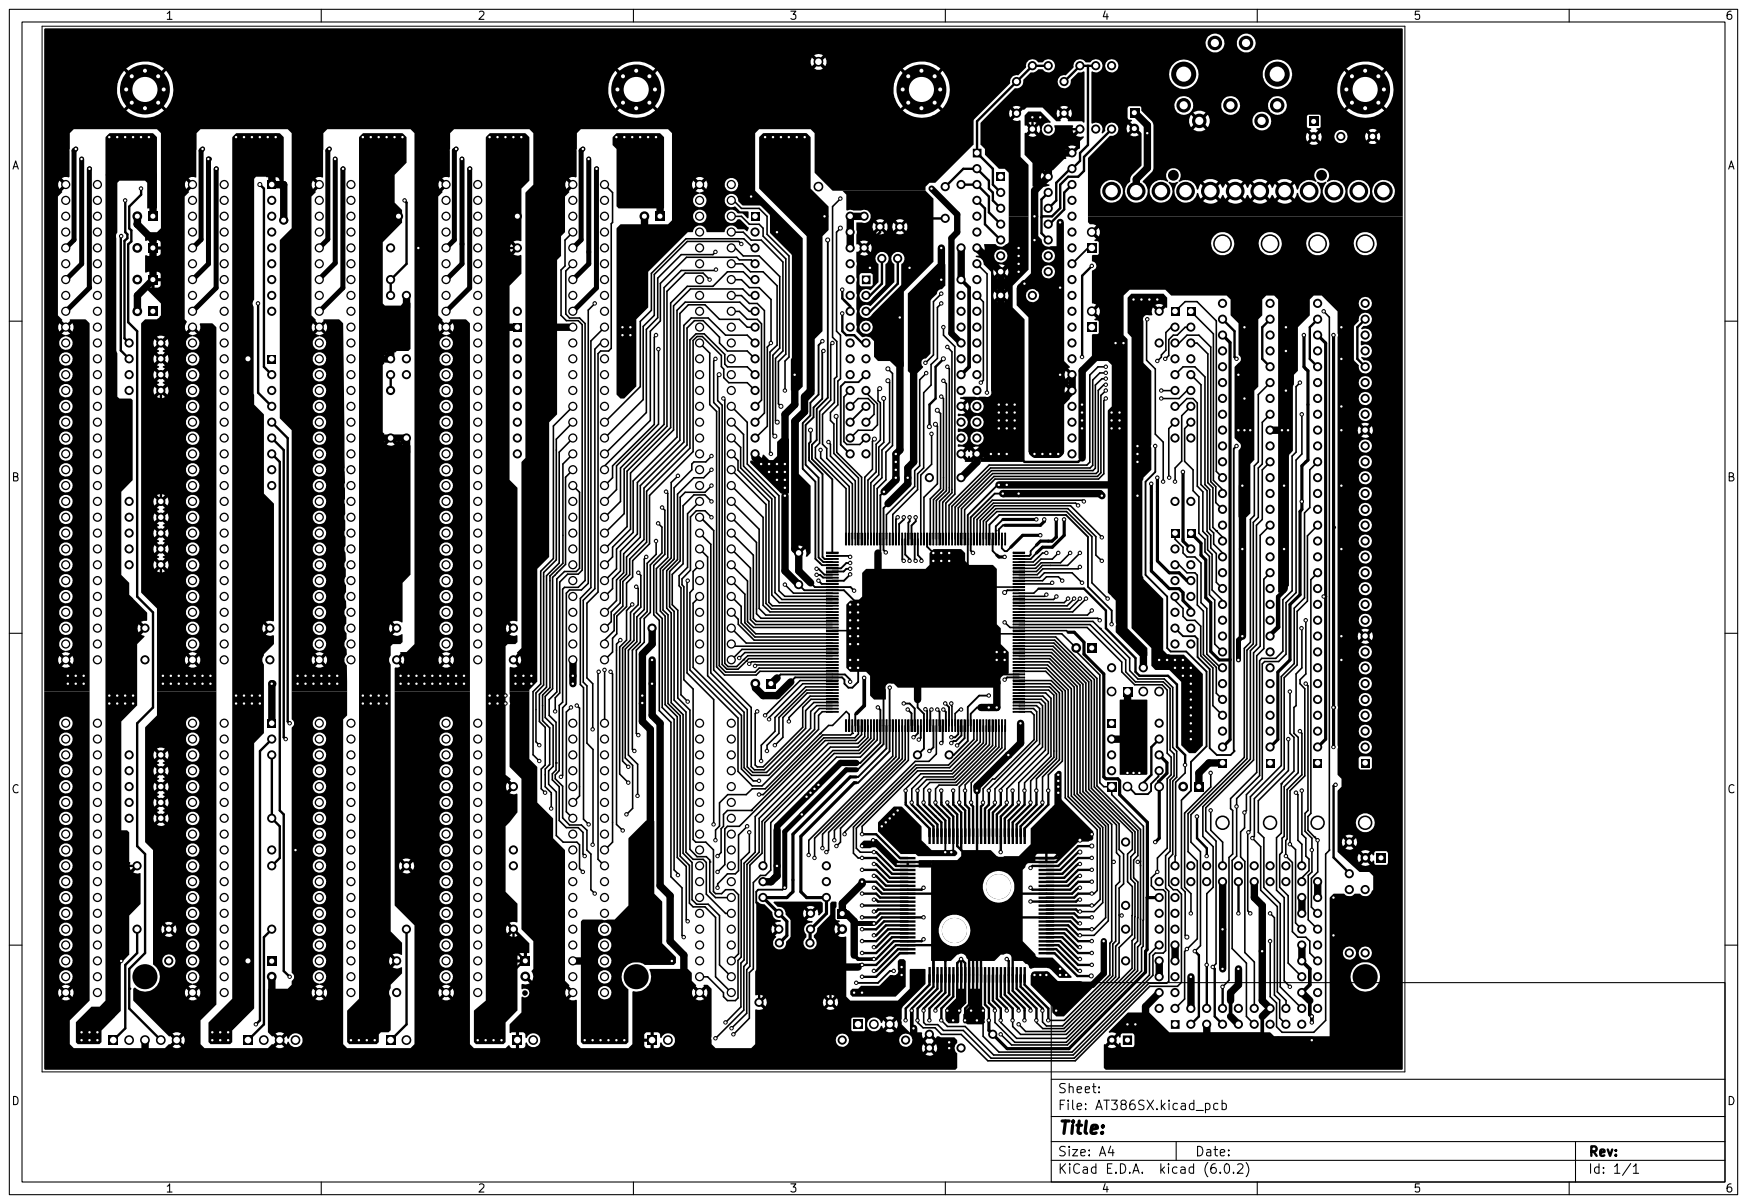
[picture p90: page 1]

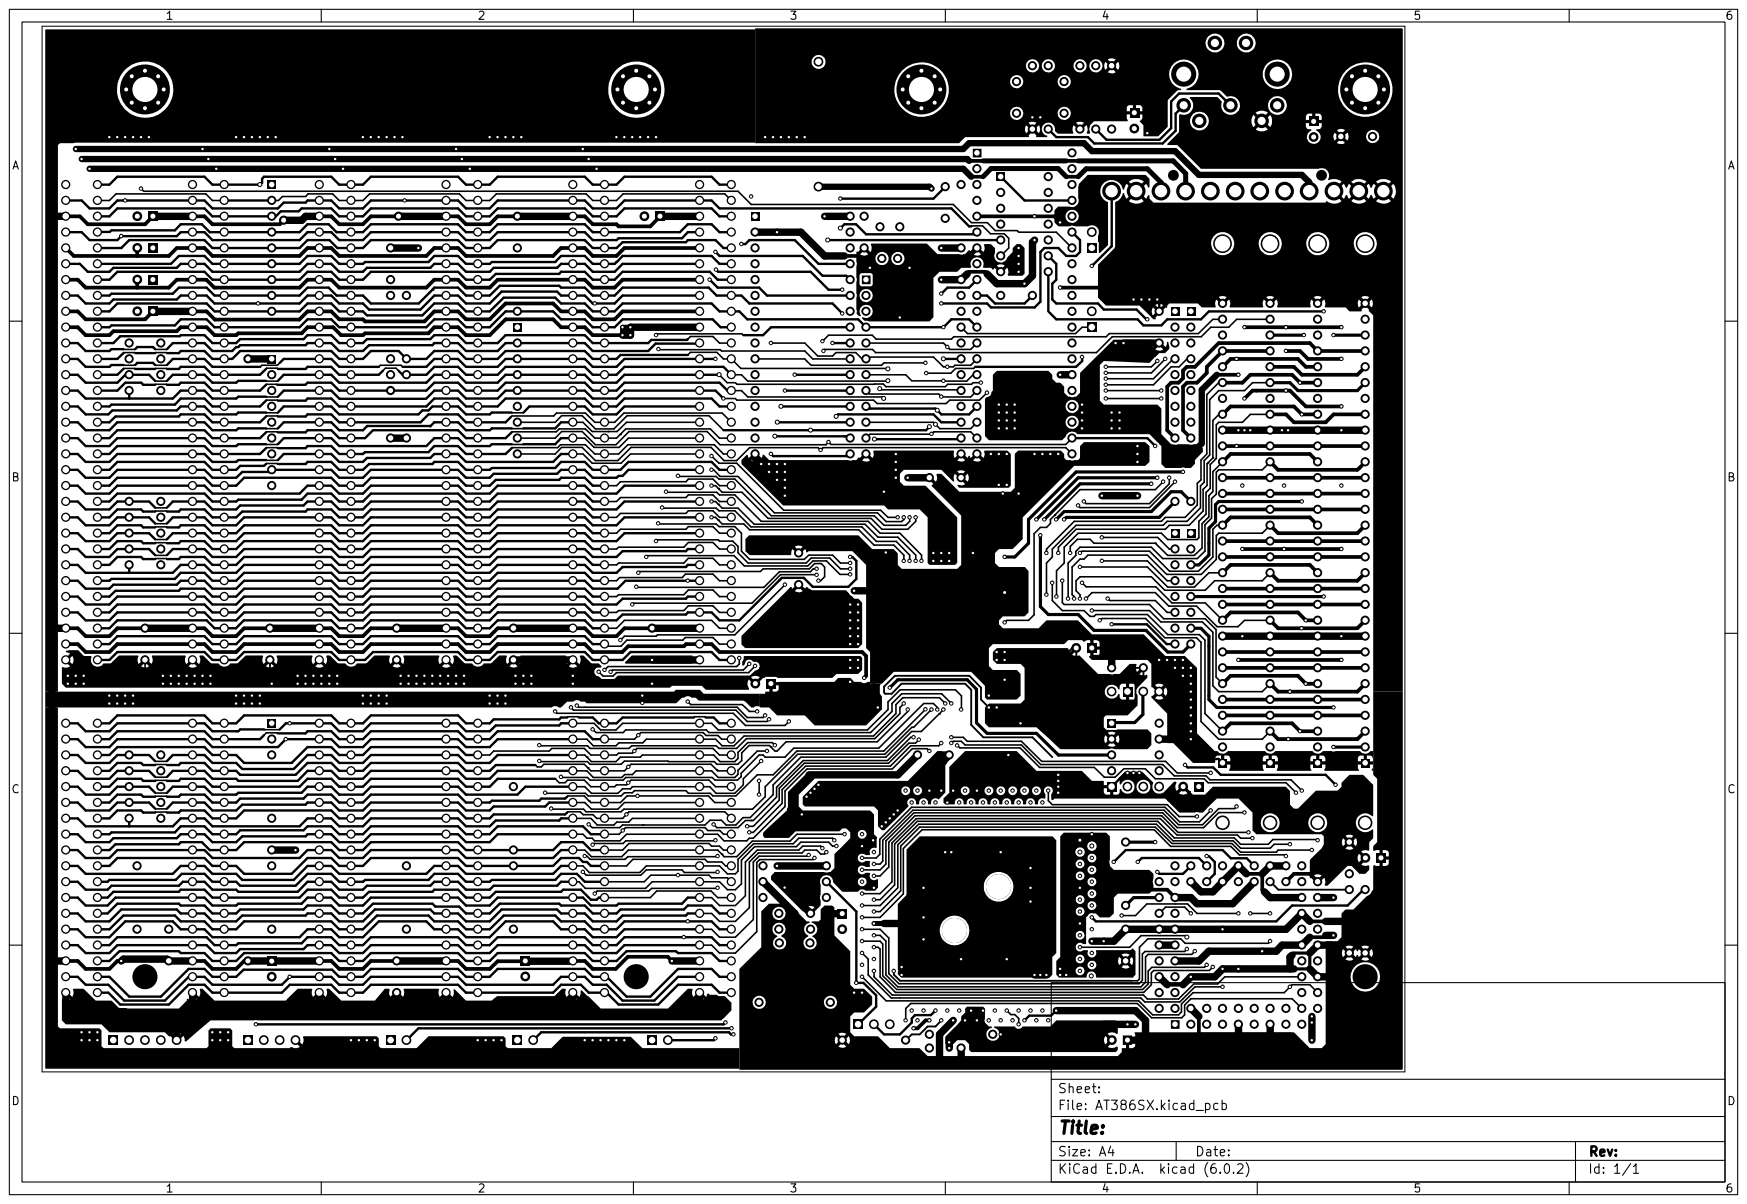
[picture p91: page 2]

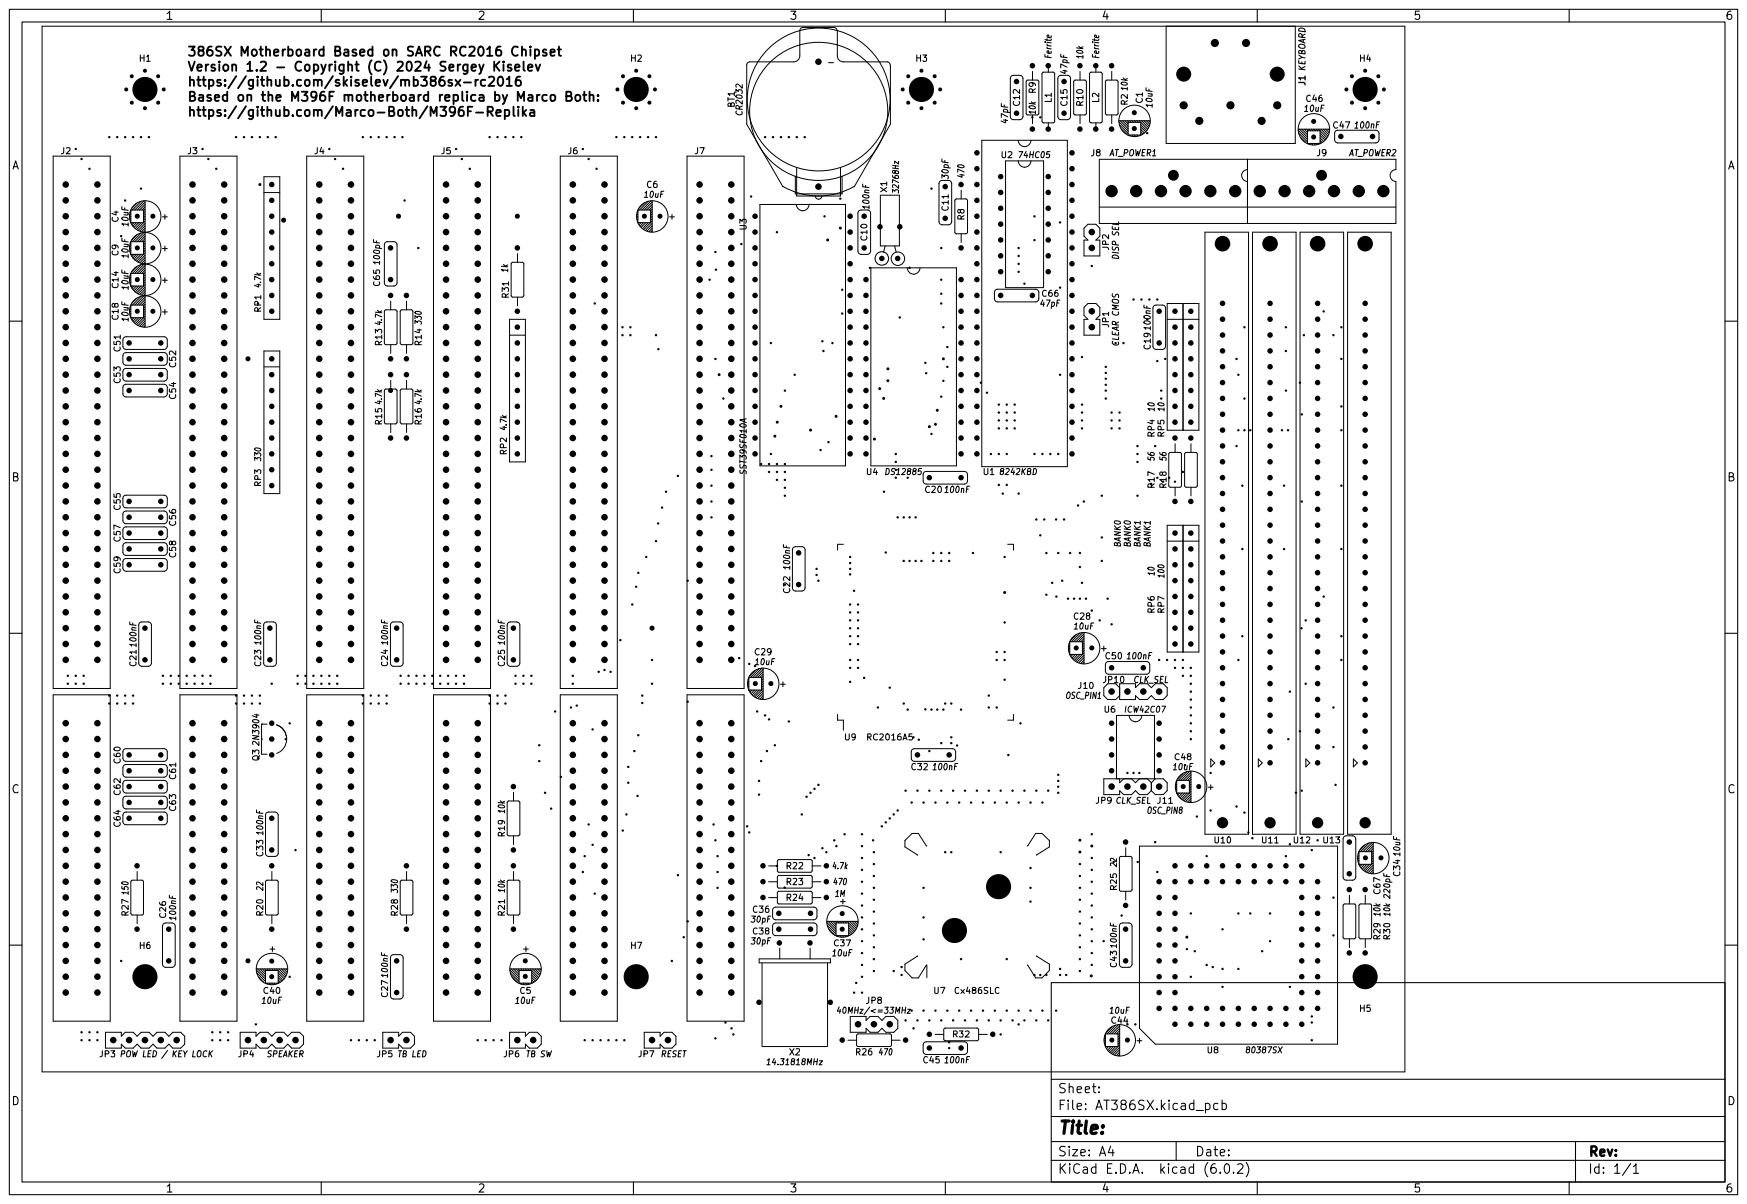
[picture p92: page 3]

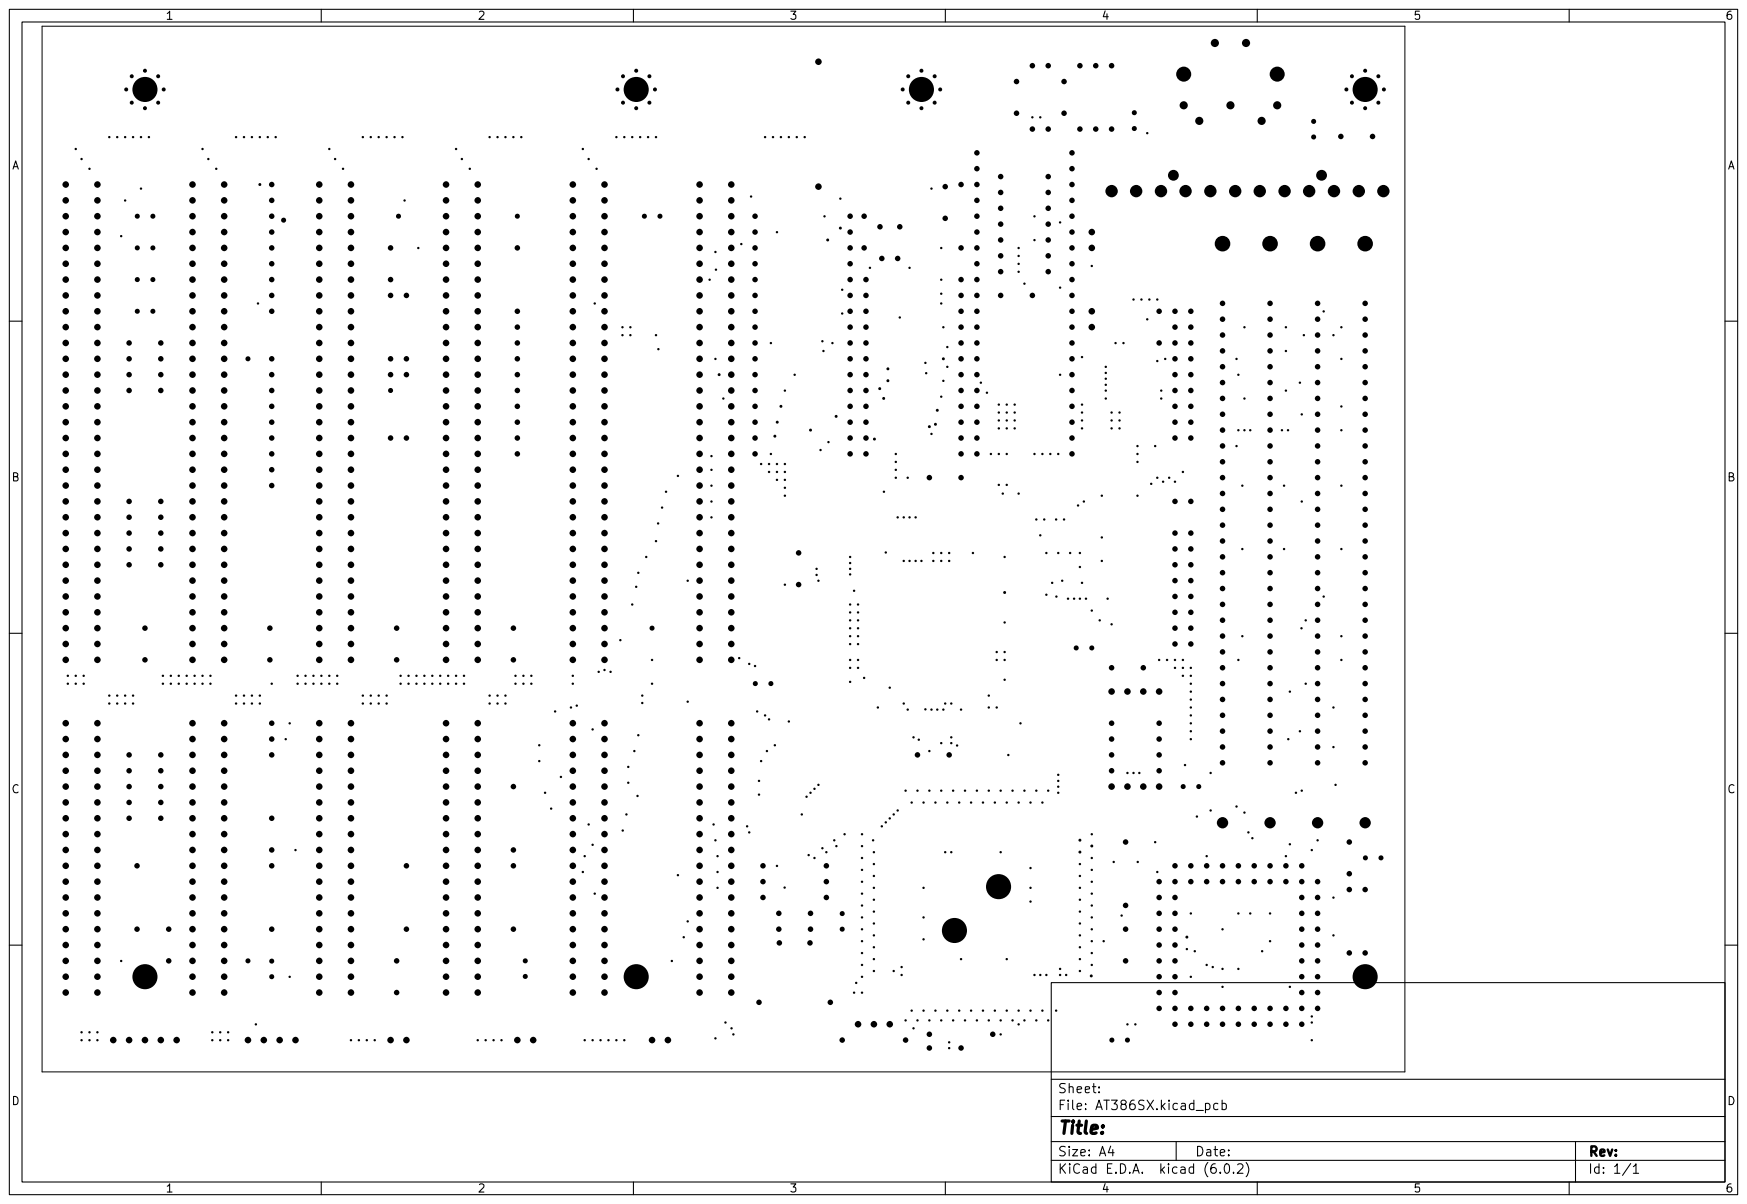
[picture p93: page 4]
