skiselev/mb386sx-rc2016/KiCad/AT386SX-Board-1.1.pdf

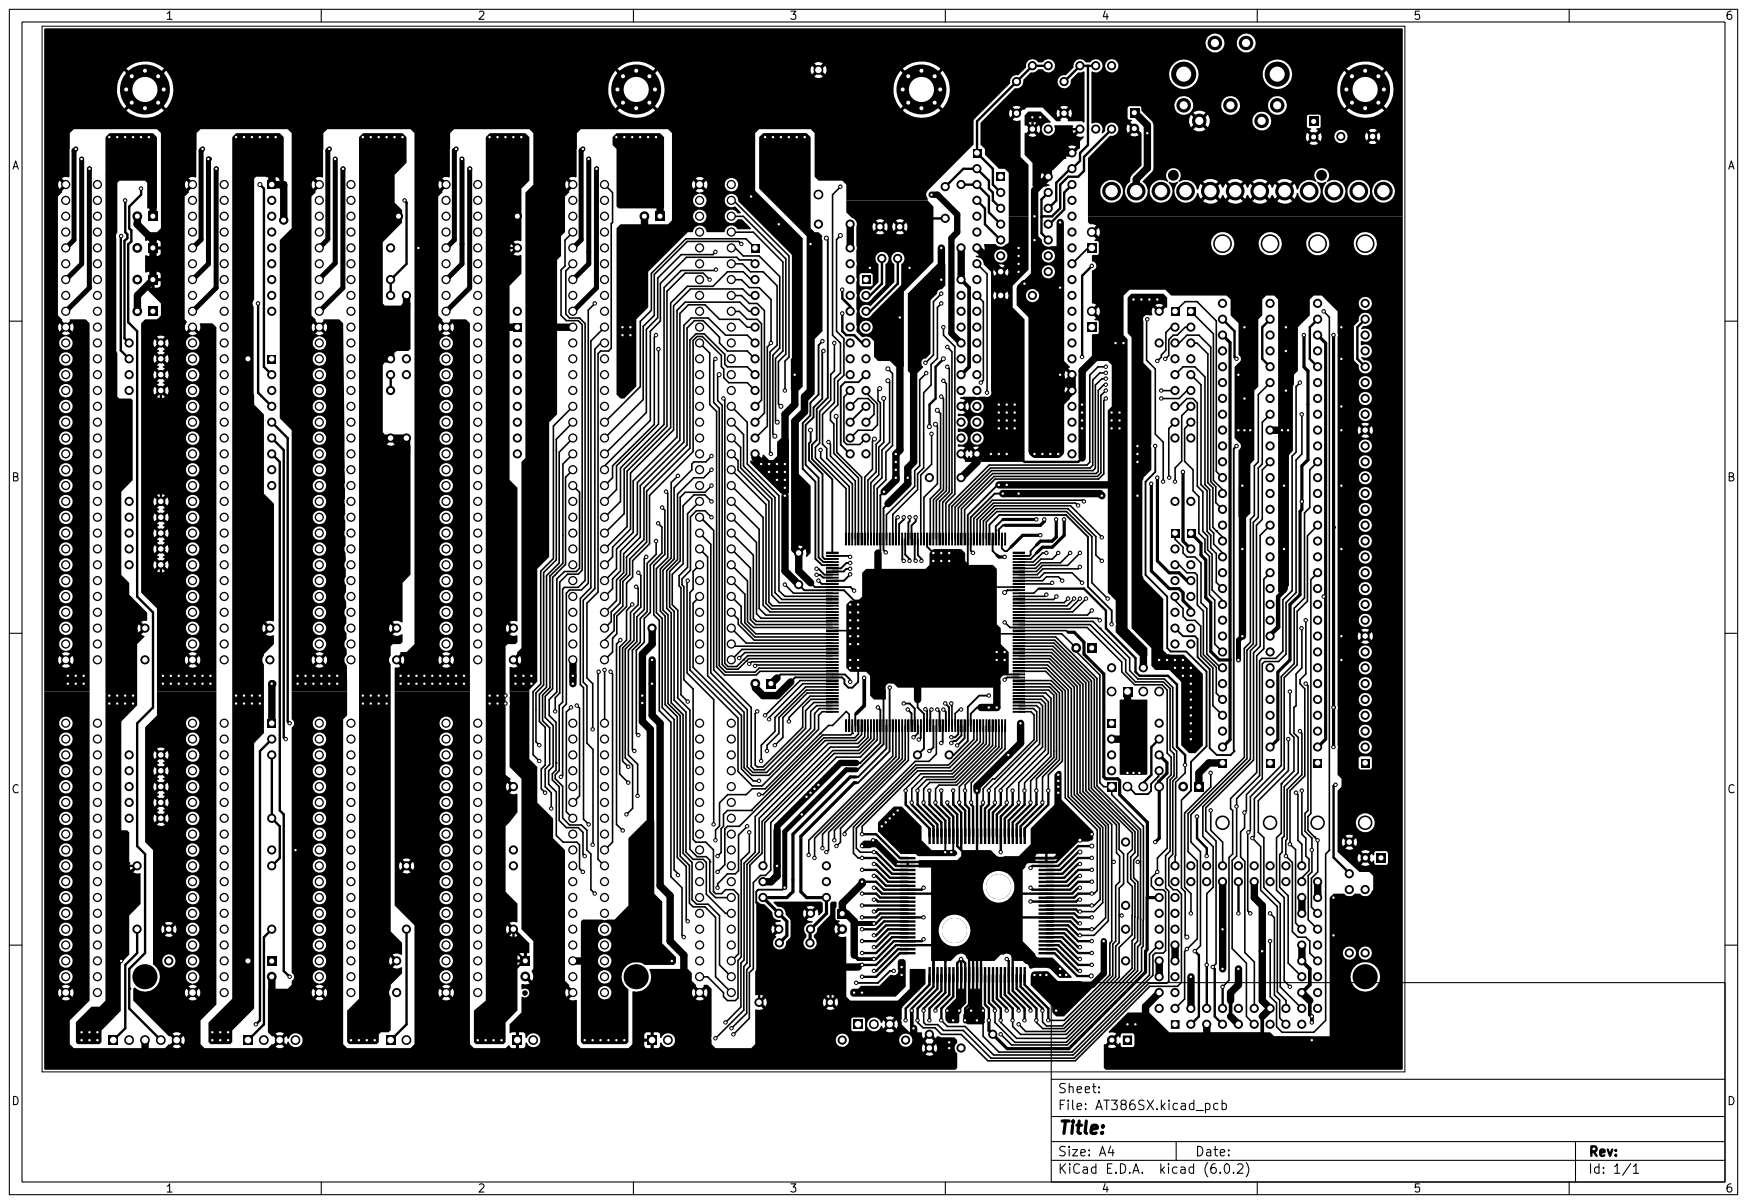
[picture p94: page 1]

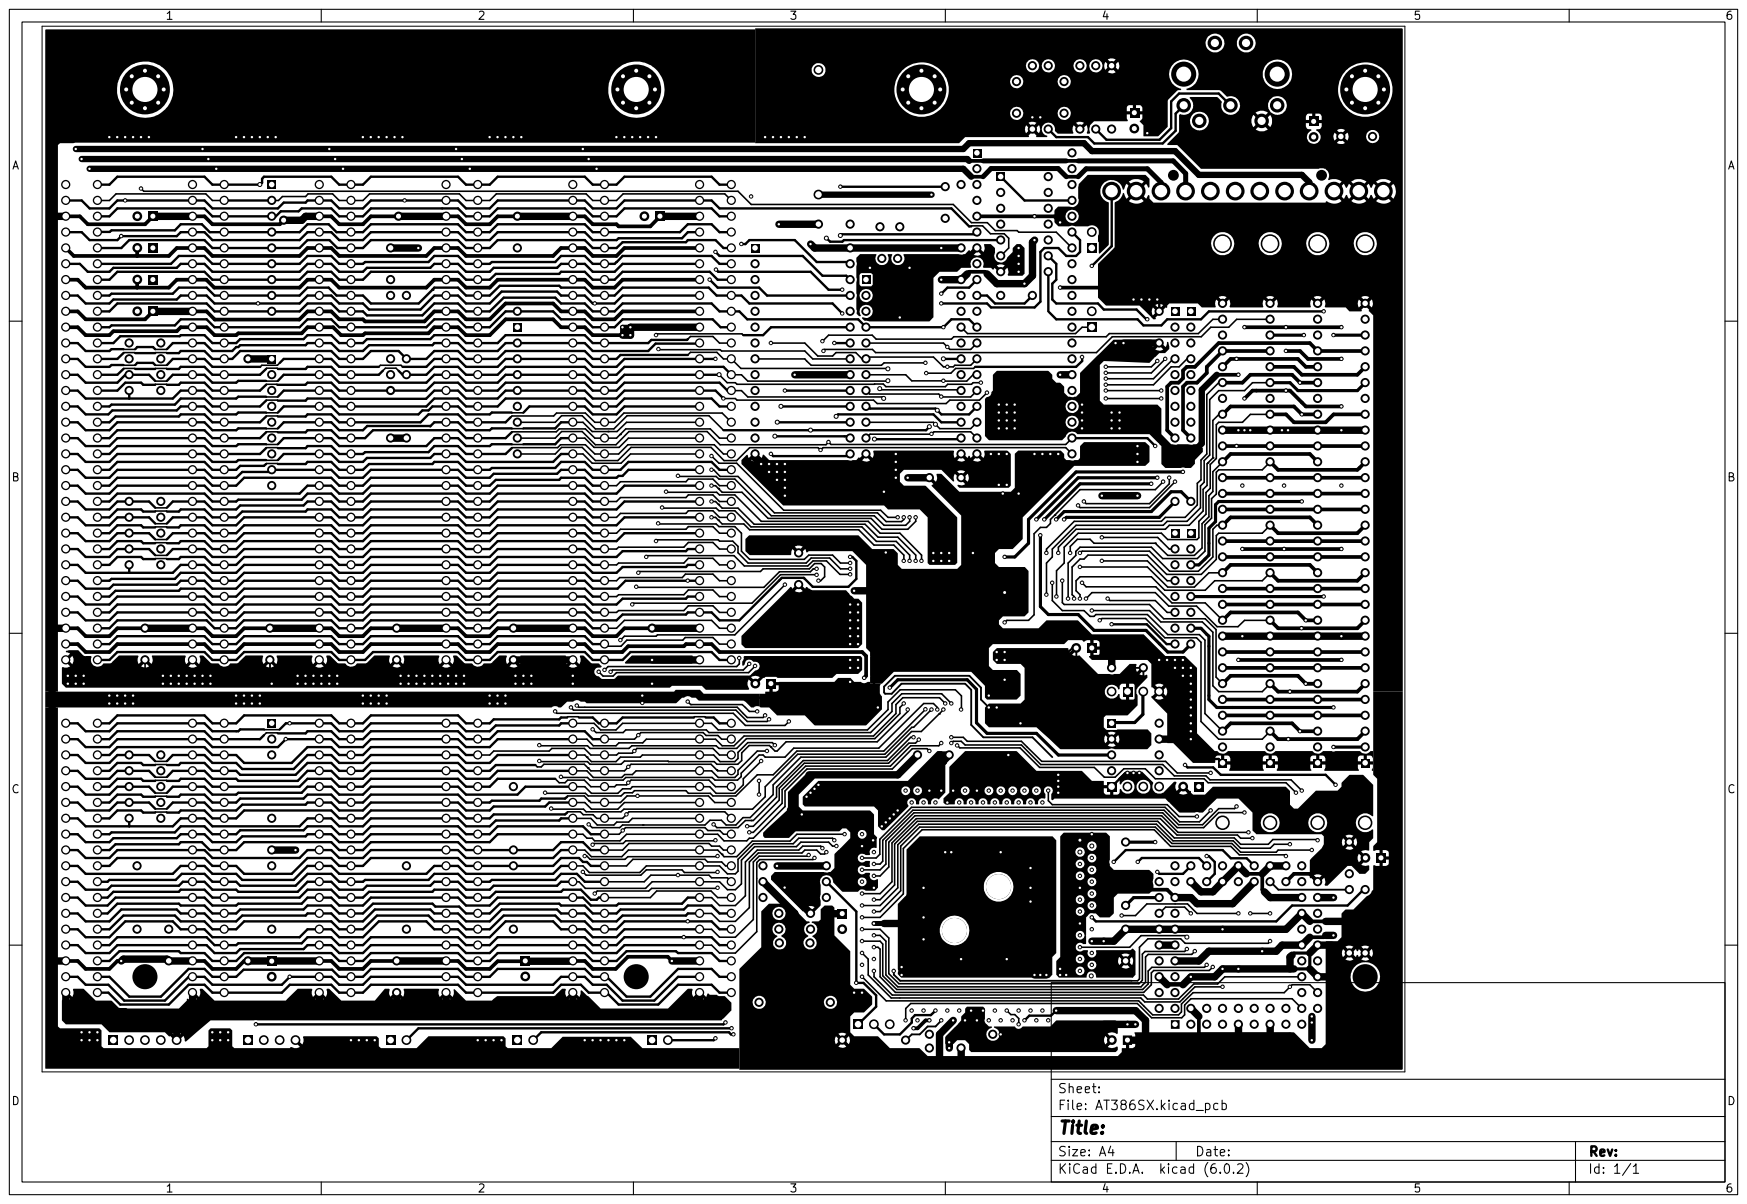
[picture p95: page 2]

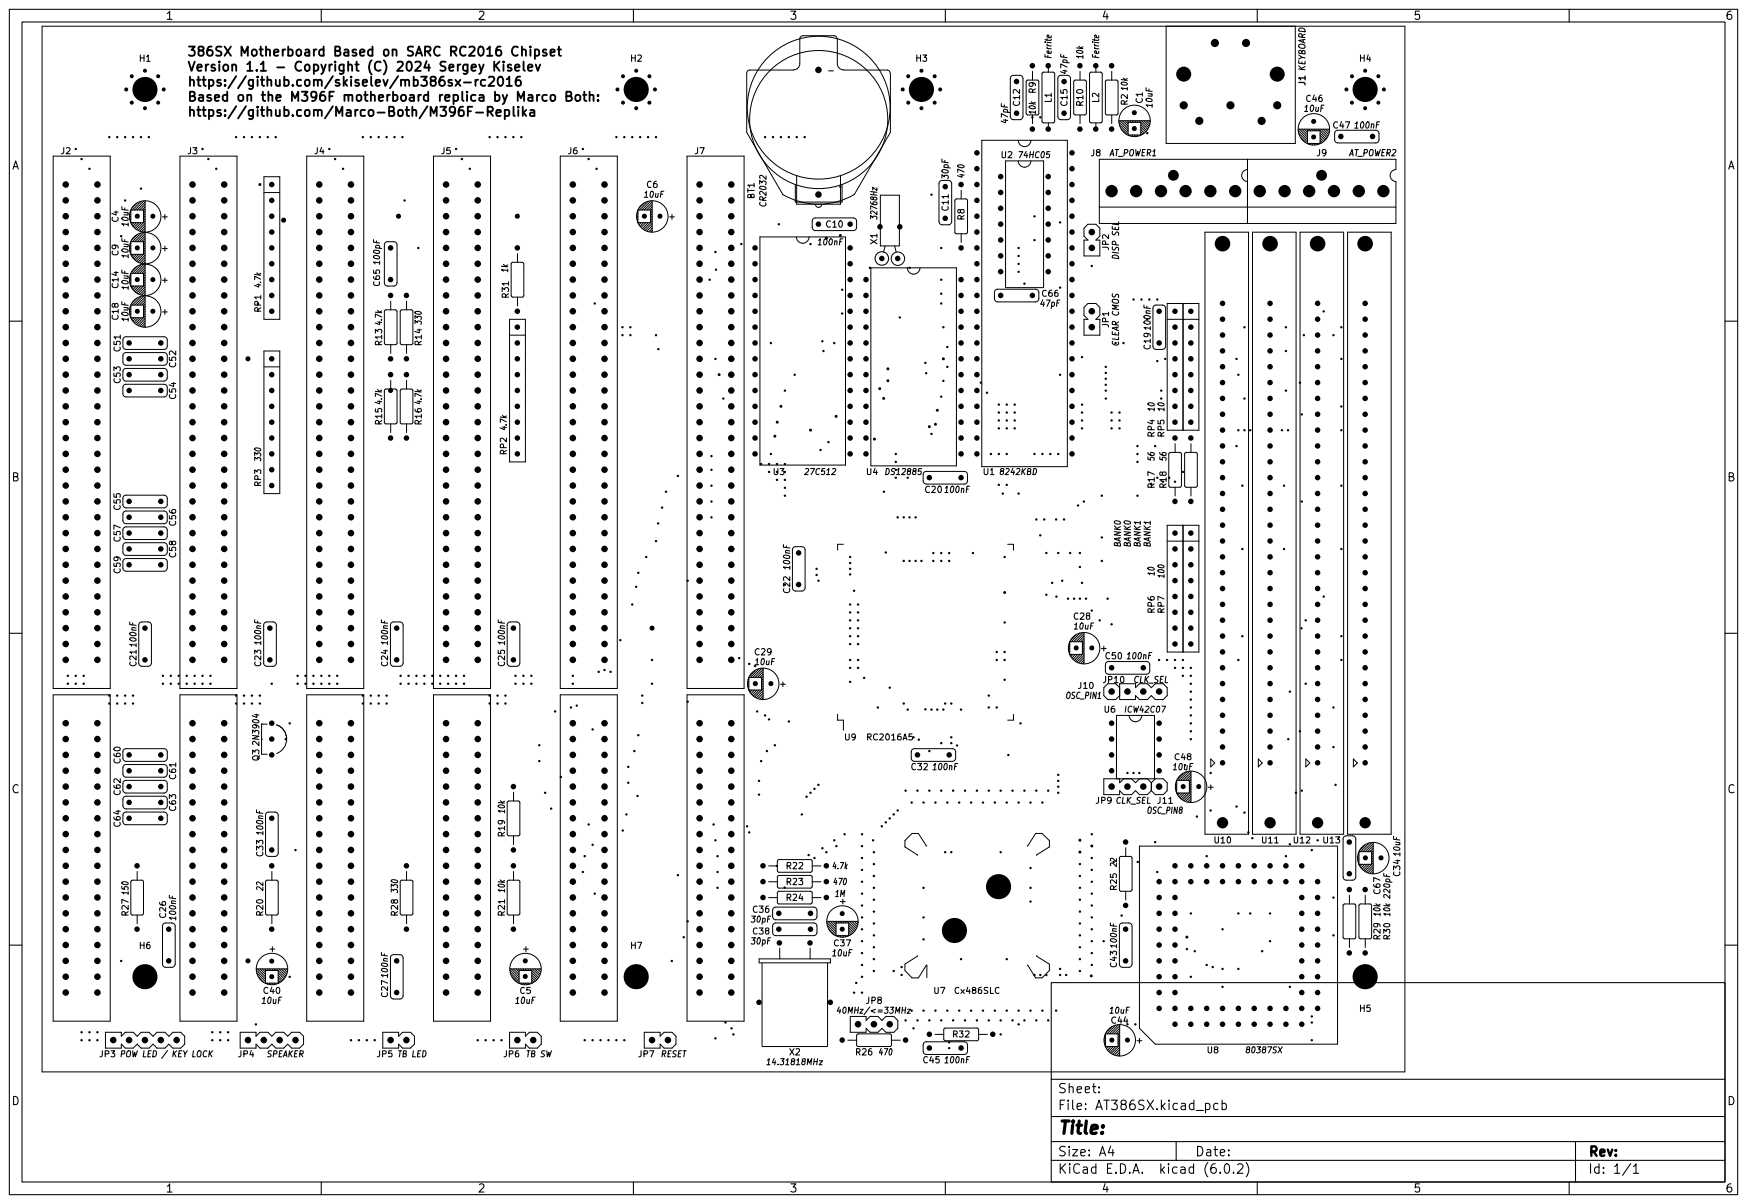
[picture p96: page 3]

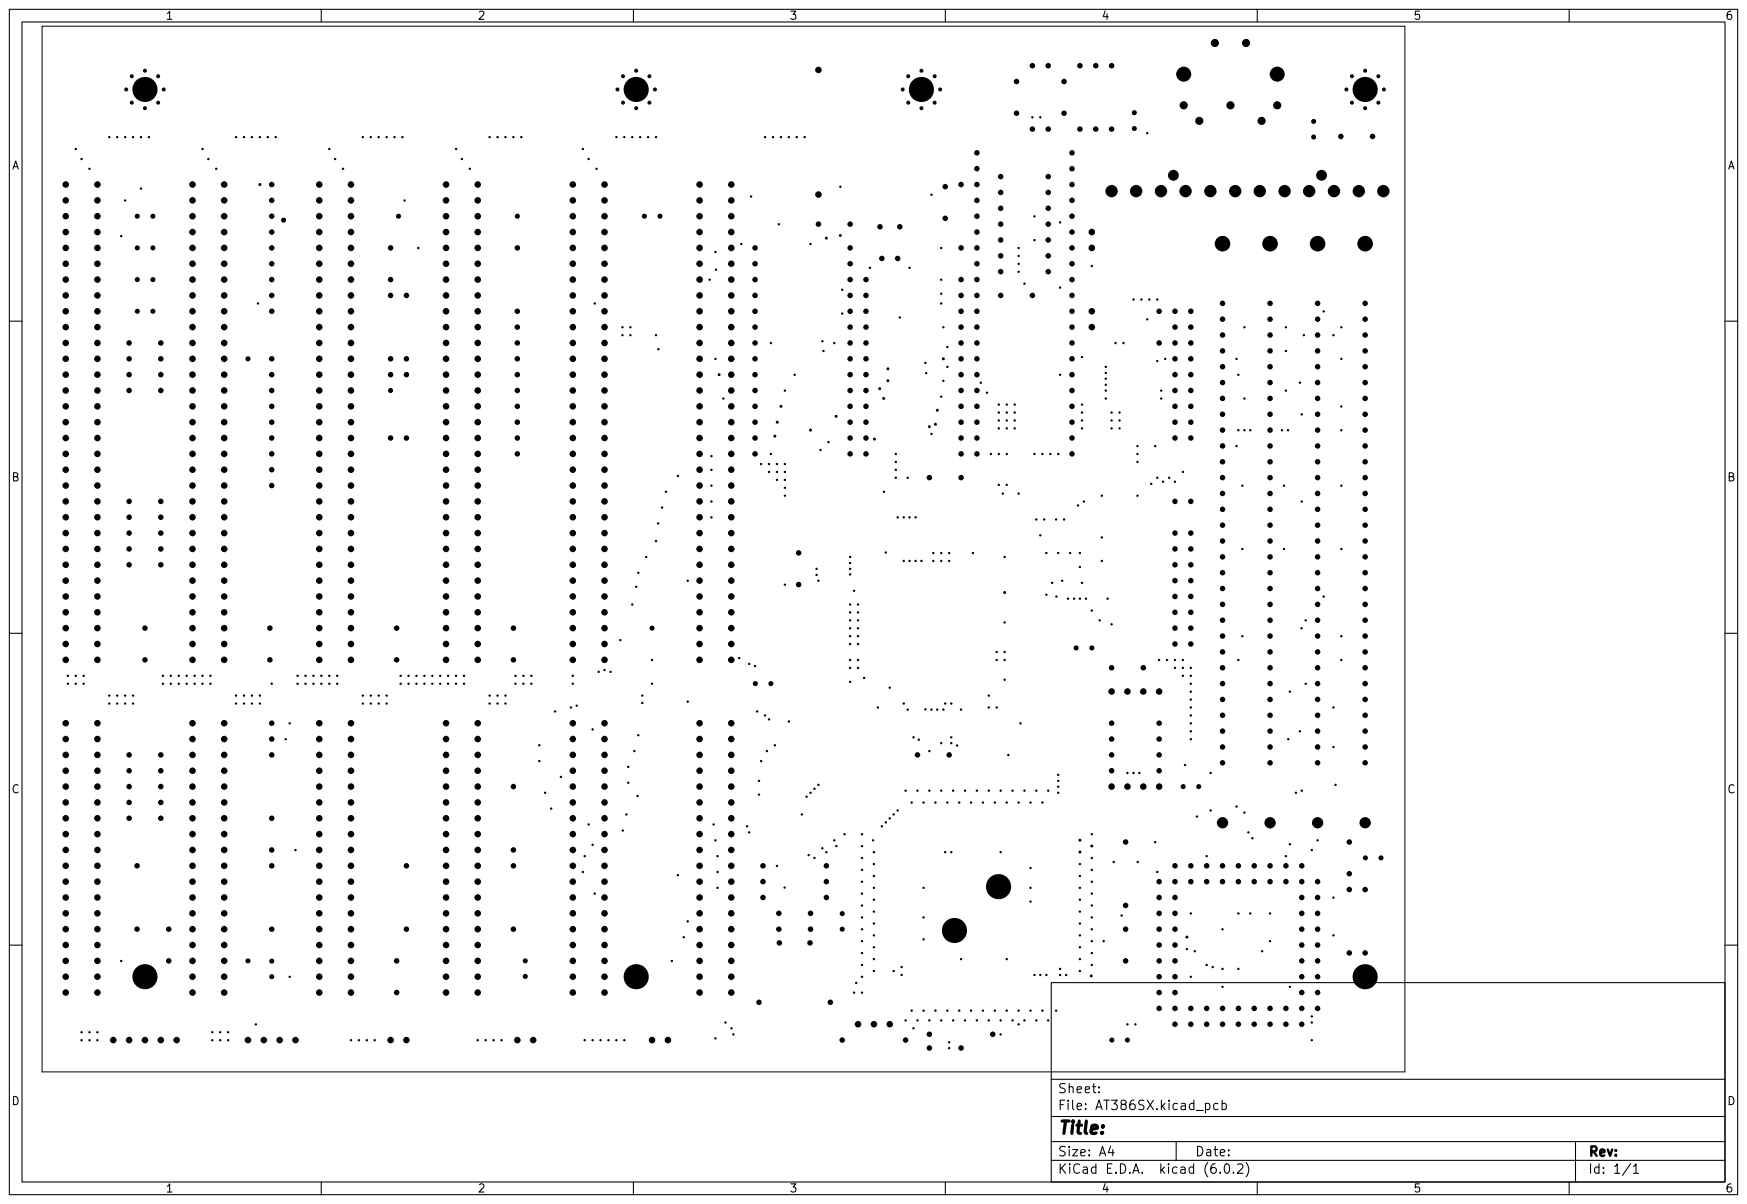
[picture p97: page 4]
