skiselev/mb386sx-rc2016/KiCad/AT386SX-Board-1.0.pdf

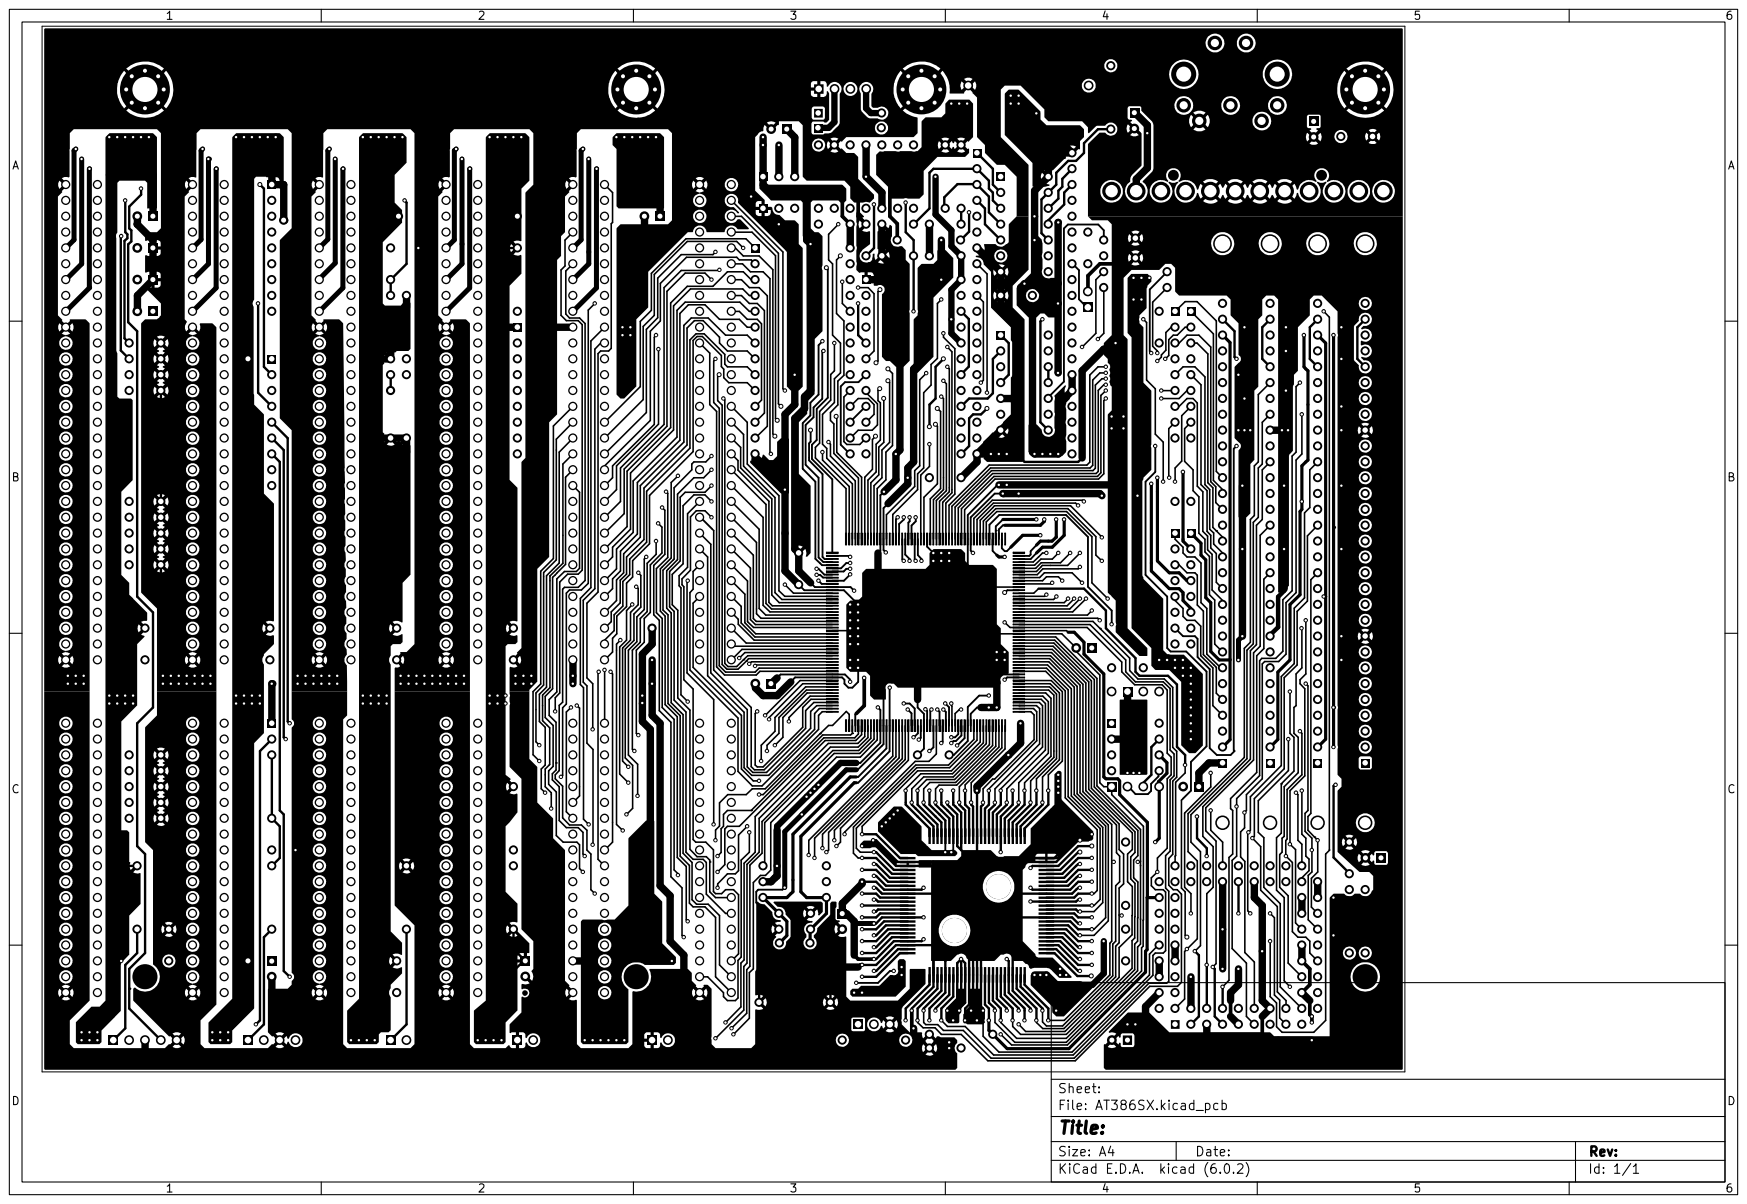
[picture p98: page 1]

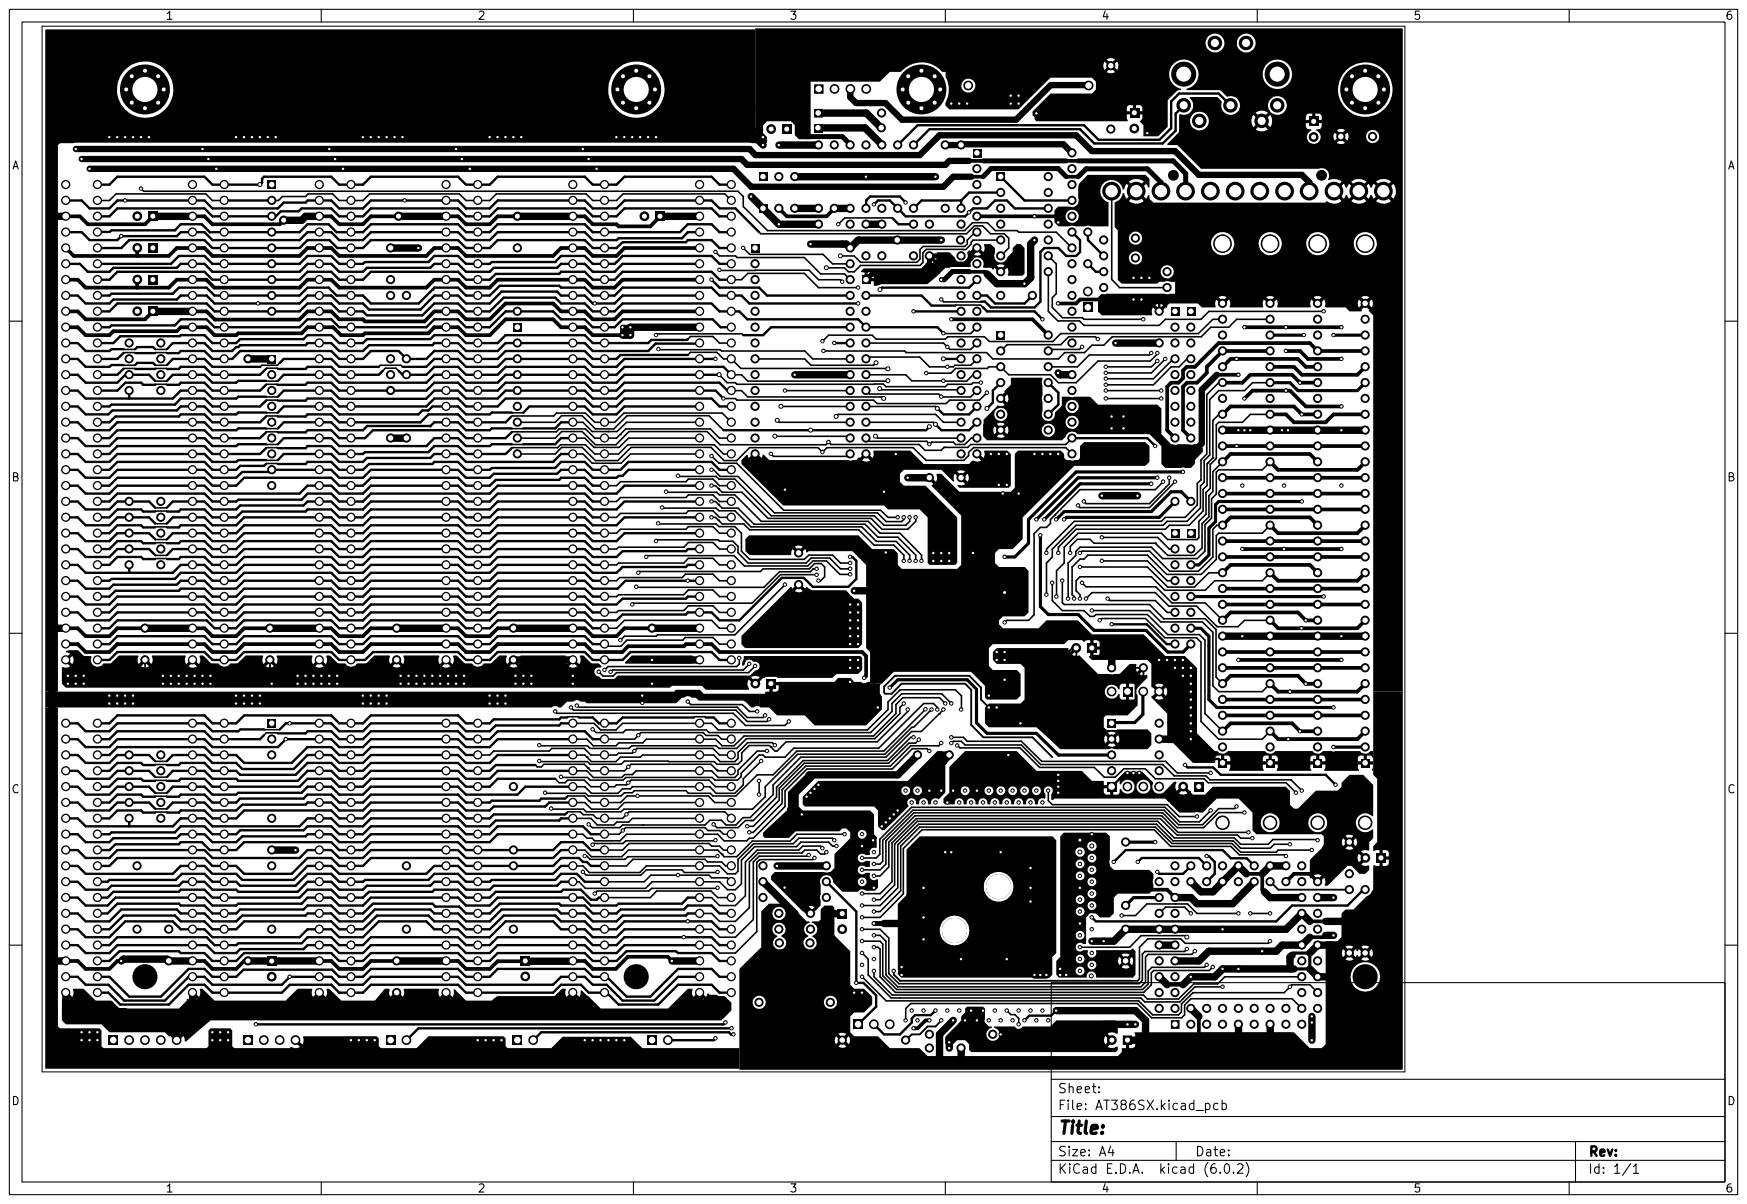
[picture p99: page 2]

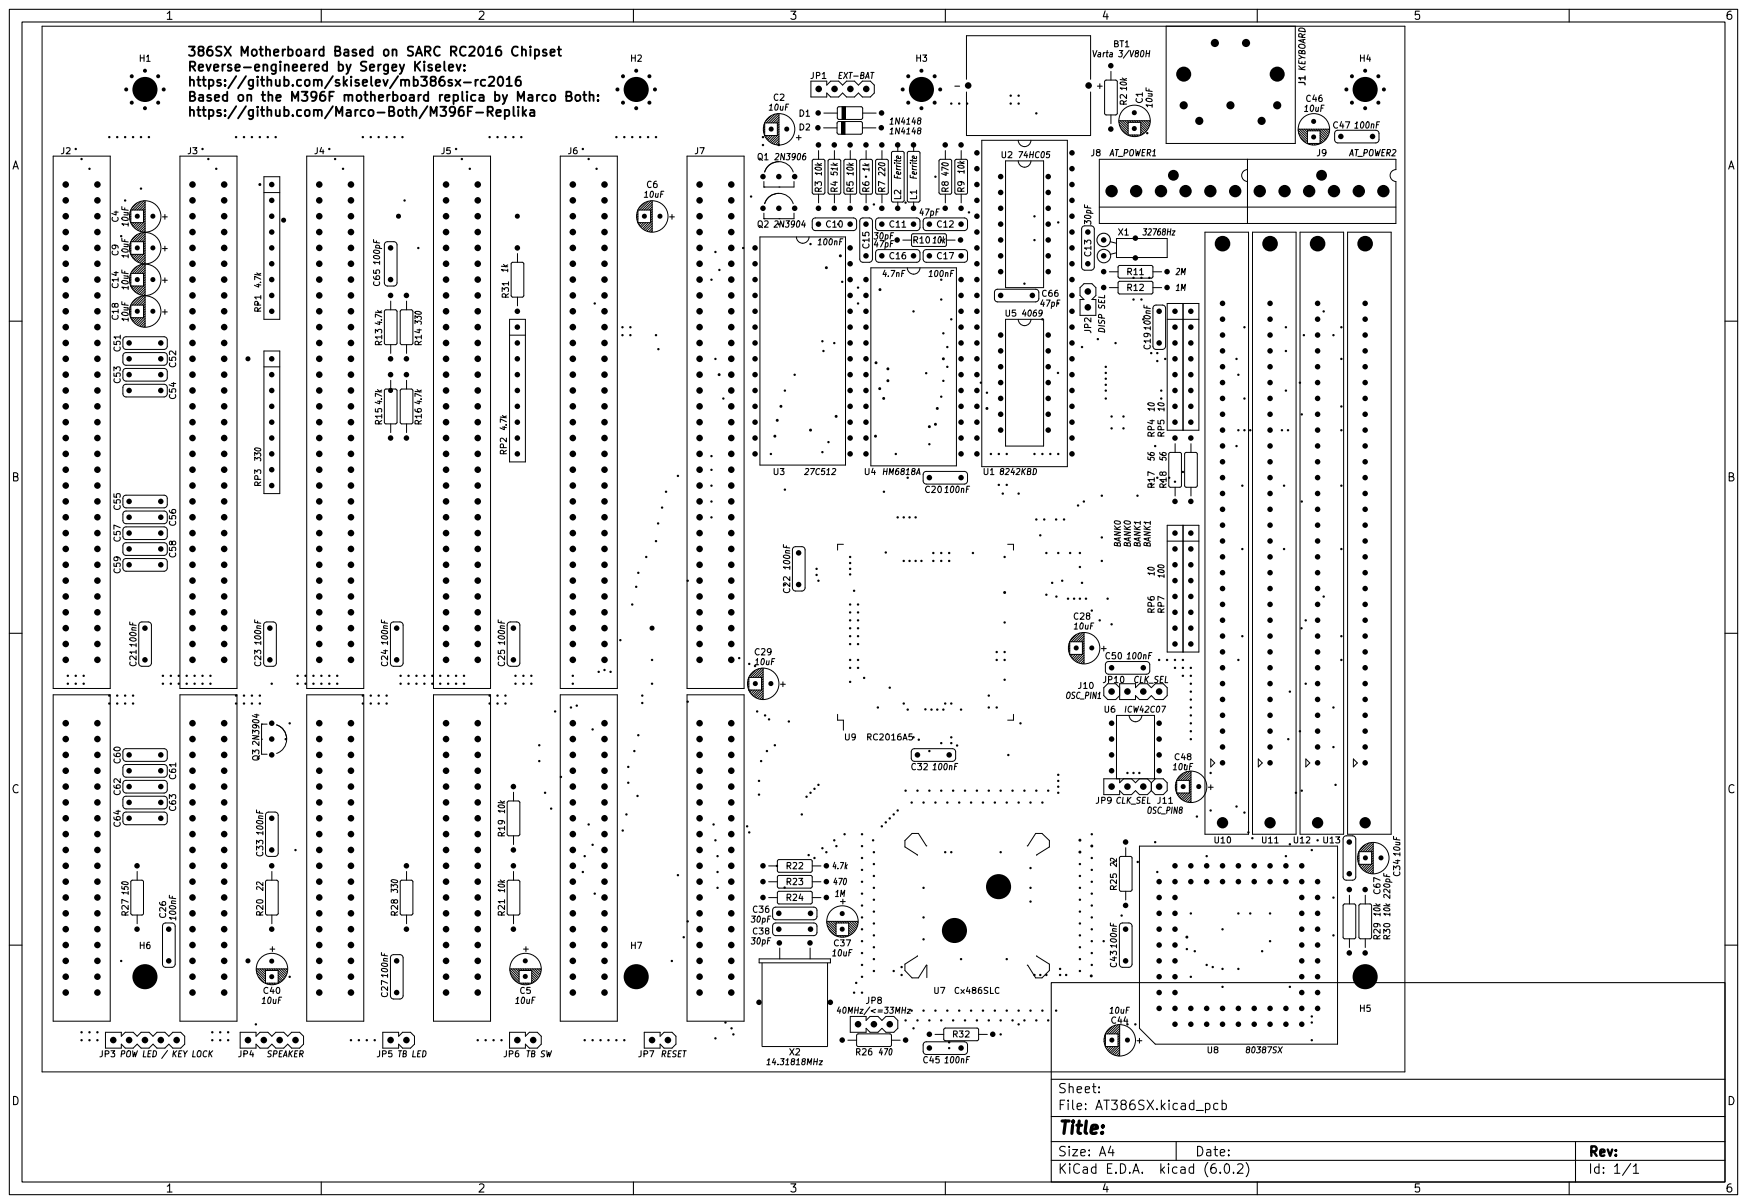
[picture p100: page 3]

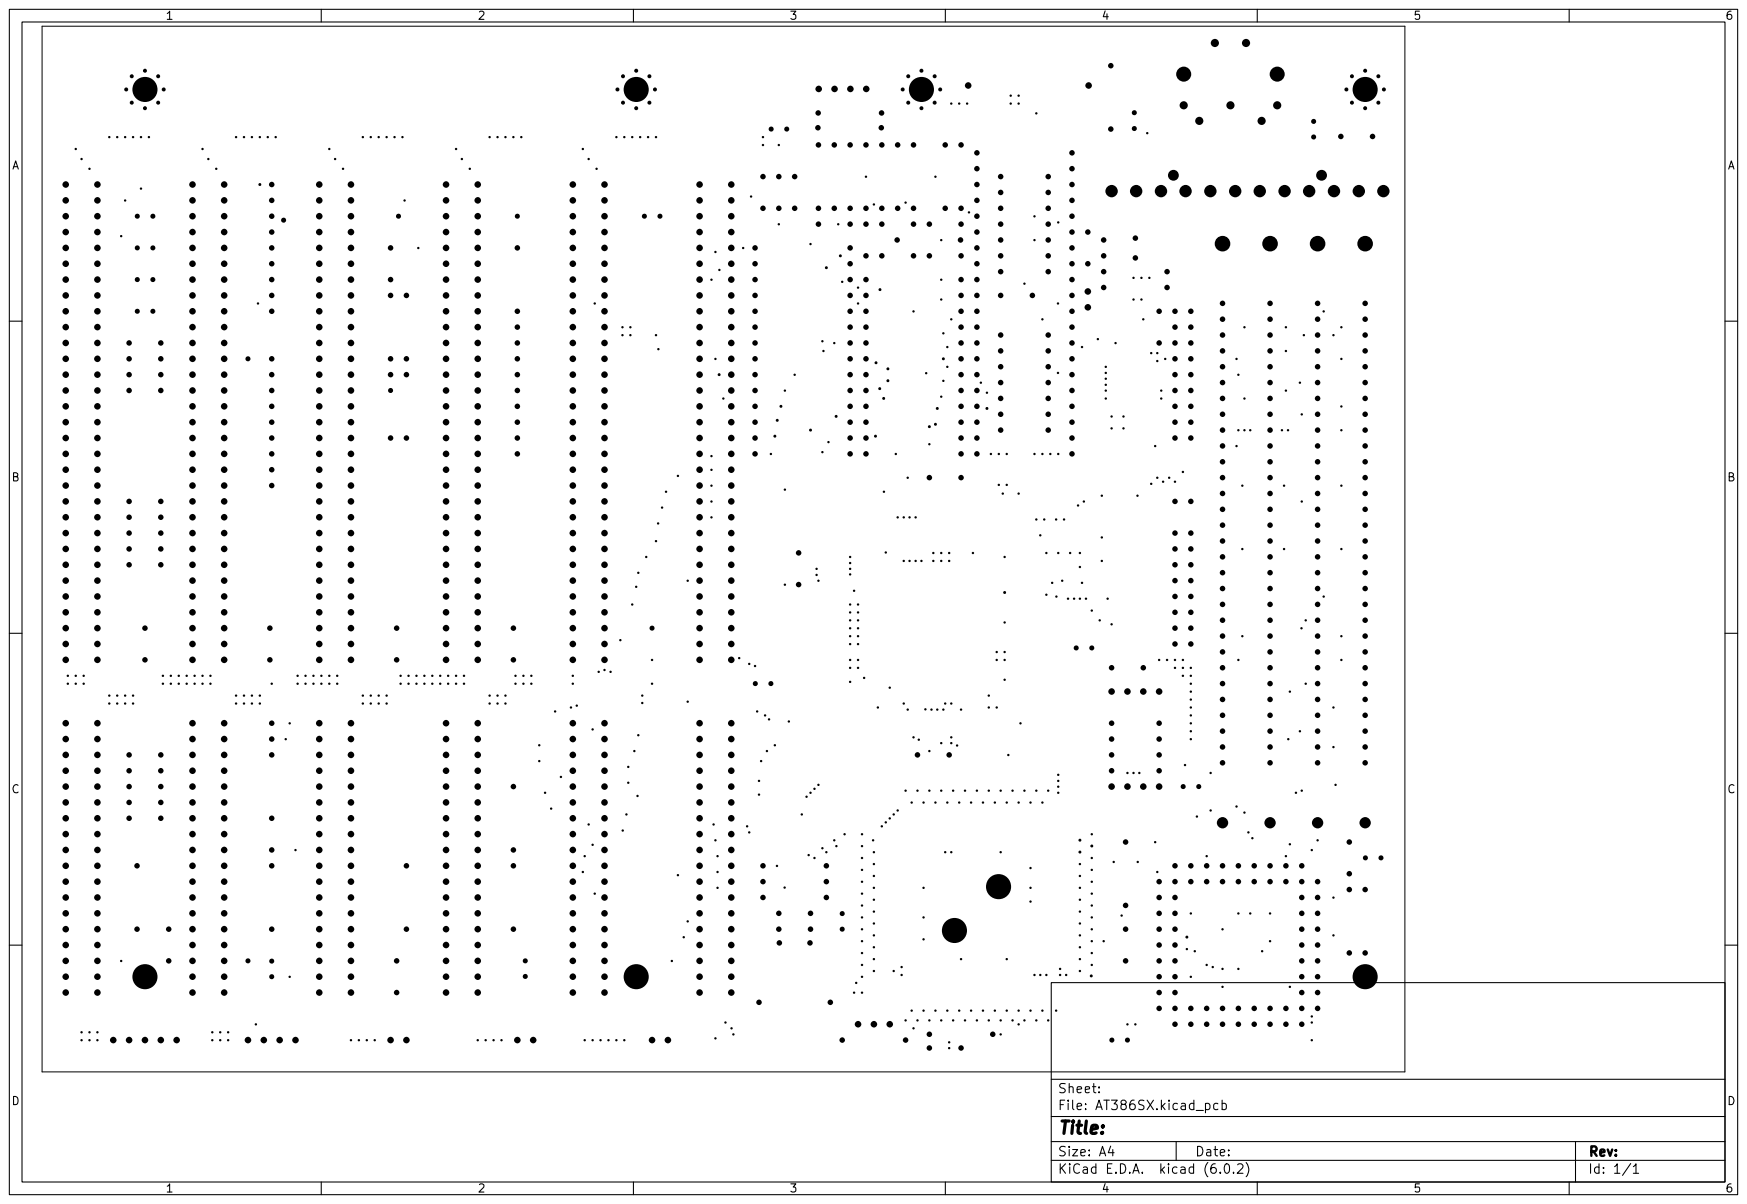
[picture p101: page 4]
